ThingySticks/EnvironmentMonitor/Arduino/V1/Images/PcbBottom.png

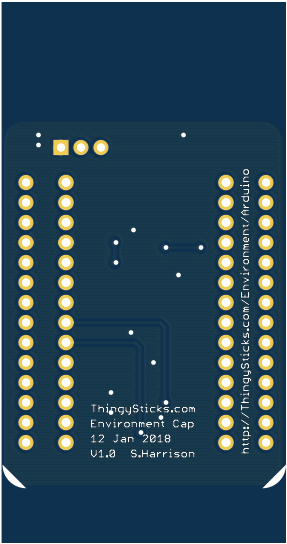
Arduino/V1/Images/PcbBottom.png
