ThingySticks/EnvironmentMonitor/Arduino/V1/Images/PcbTop.png

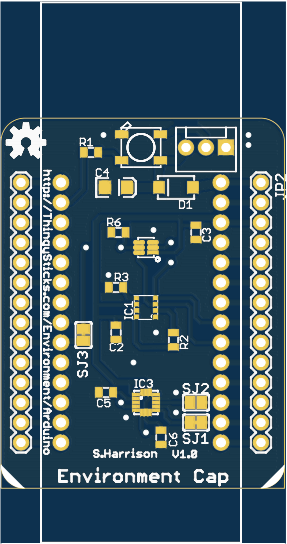
Arduino/V1/Images/PcbTop.png
