ThingySticks/EnvironmentMonitor/ArduinoNano33/V10/BottomBasic/Images/V10/PcbBottomSilkAndValues.png

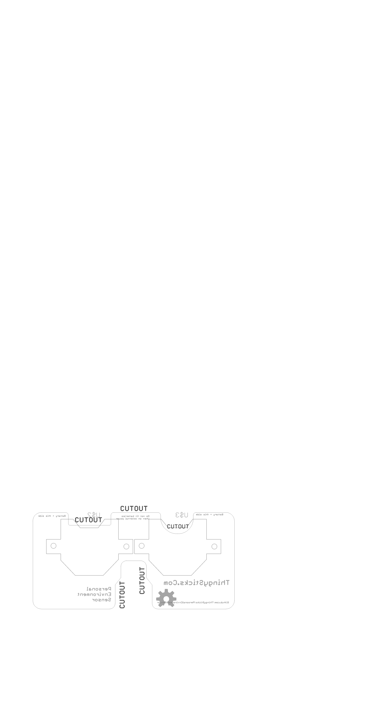
ArduinoNano33/V10/BottomBasic/Images/V10/PcbBottomSilkAndValues.png
