ThingySticks/EnvironmentMonitor/ArduinoNano33/V10/BottomBasic/Images/V10/PcbTopDesign.png

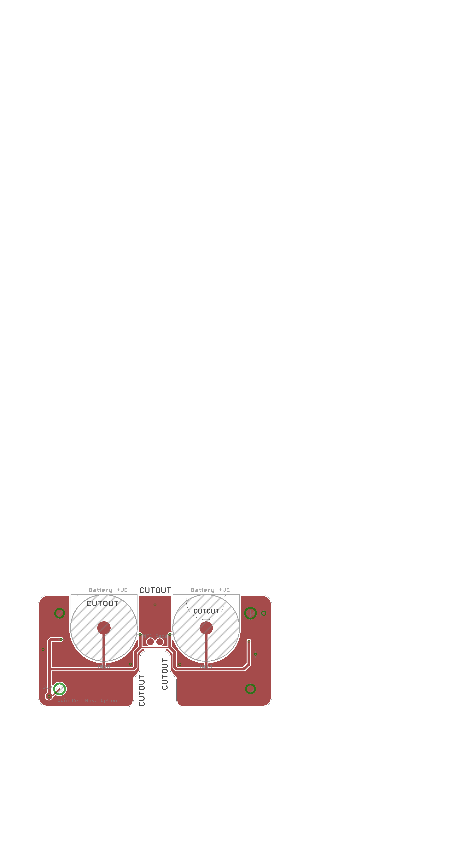
ArduinoNano33/V10/BottomBasic/Images/V10/PcbTopDesign.png
