ThingySticks/EnvironmentMonitor/ArduinoNano33/V10/BottomBasic/Images/V10/PcbTopSilkAndValues.png

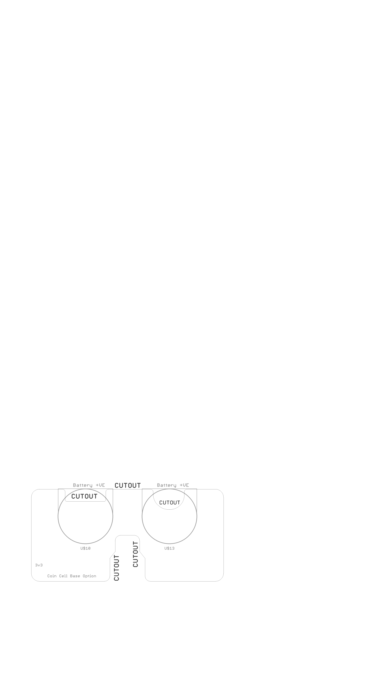
ArduinoNano33/V10/BottomBasic/Images/V10/PcbTopSilkAndValues.png
