ThingySticks/EnvironmentMonitor/ArduinoNano33/V10/BottomCustom/Images/PcbBottomDesign.png

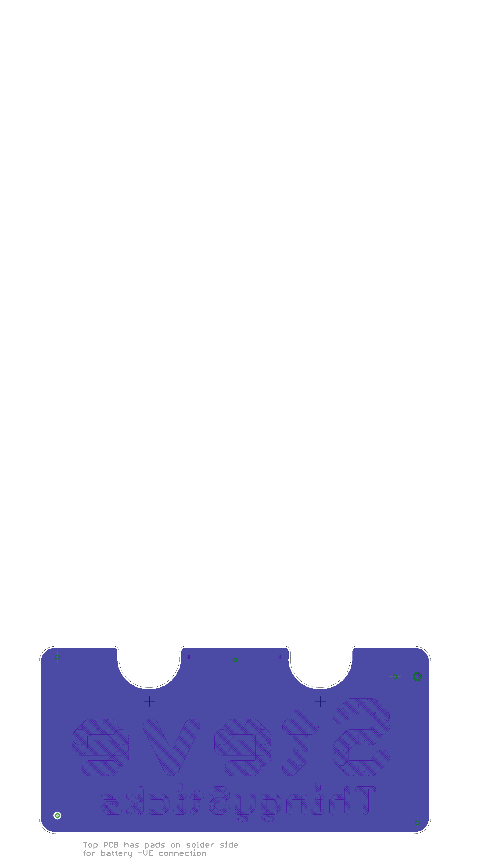
ArduinoNano33/V10/BottomCustom/Images/PcbBottomDesign.png
