ThingySticks/EnvironmentMonitor/ArduinoNano33/V10/BottomCustom/Images/PcbBottomSilkAndValues.png

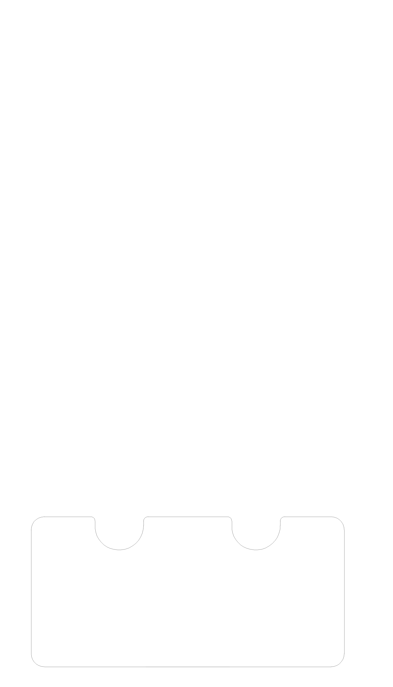
ArduinoNano33/V10/BottomCustom/Images/PcbBottomSilkAndValues.png
