ThingySticks/EnvironmentMonitor/ArduinoNano33/V10/BottomCustom/Images/PcbTopDesign.png

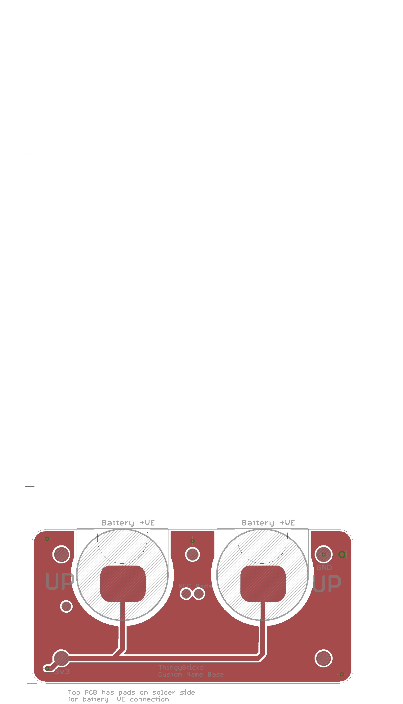
ArduinoNano33/V10/BottomCustom/Images/PcbTopDesign.png
