ThingySticks/EnvironmentMonitor/ArduinoNano33/V10/BottomCustom/Images/PcbTopSilkAndValues.png

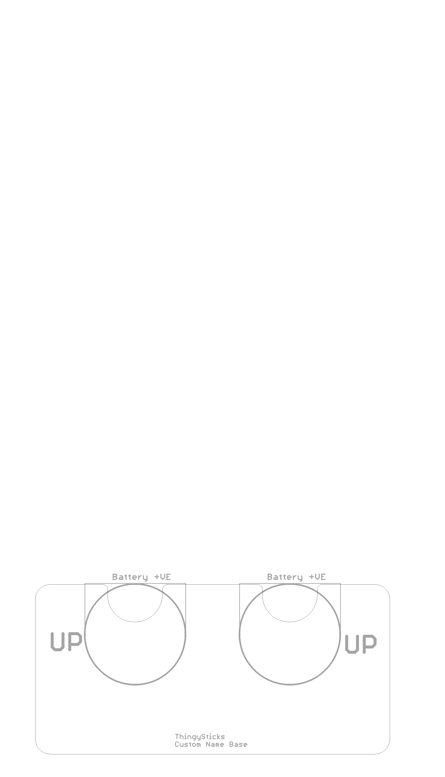
ArduinoNano33/V10/BottomCustom/Images/PcbTopSilkAndValues.png
