ThingySticks/EnvironmentMonitor/ArduinoNano33/V10/BottomCustom/Images/Schematic.png

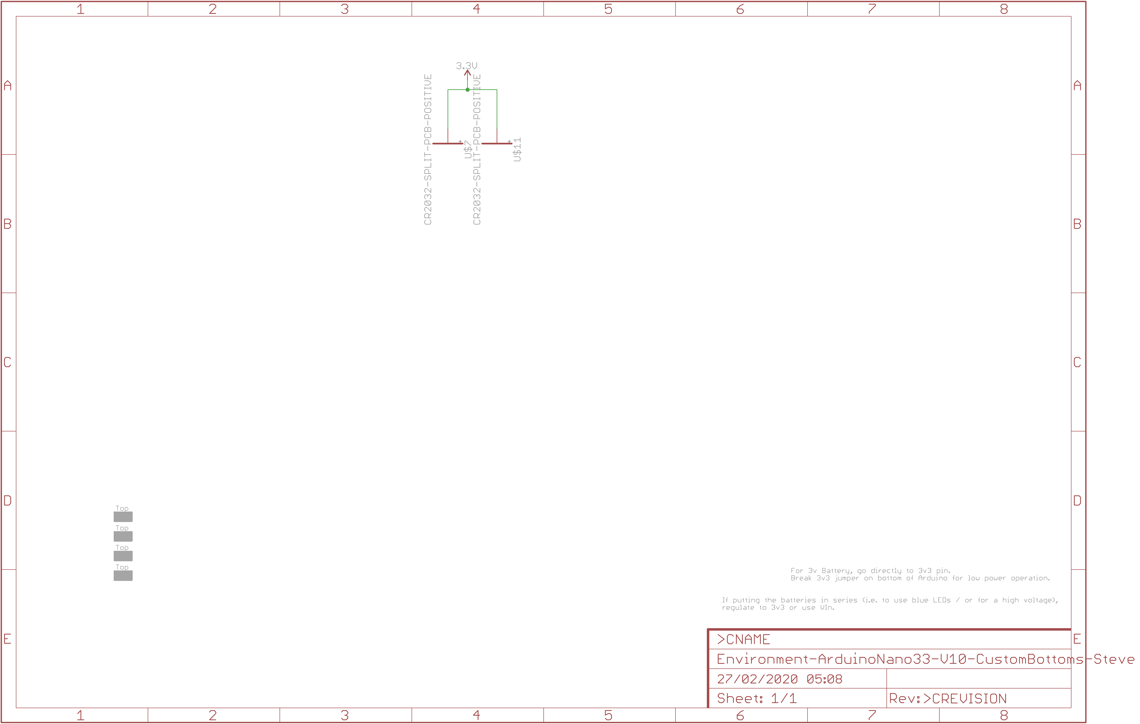
ArduinoNano33/V10/BottomCustom/Images/Schematic.png
