ThingySticks/EnvironmentMonitor/ArduinoNano33/V10/MiddleBasic/Images/V10.1/PcbAllLayersDesign.png

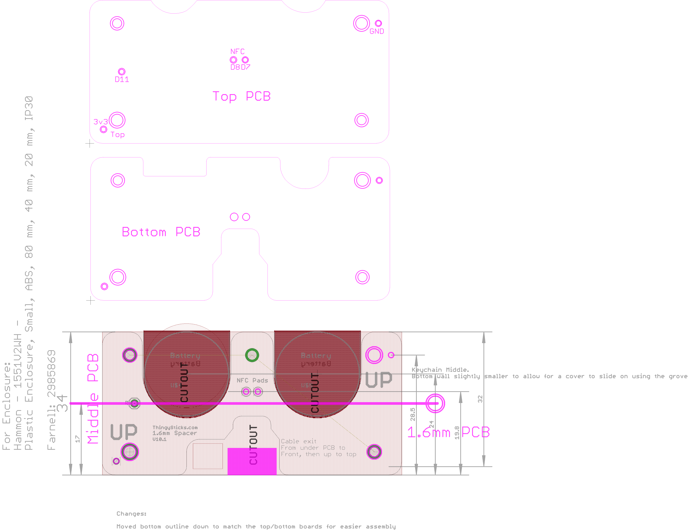
ArduinoNano33/V10/MiddleBasic/Images/V10.1/PcbAllLayersDesign.png
