ThingySticks/EnvironmentMonitor/ArduinoNano33/V10/MiddleBasic/Images/V10.1/PcbBottomDesign.png

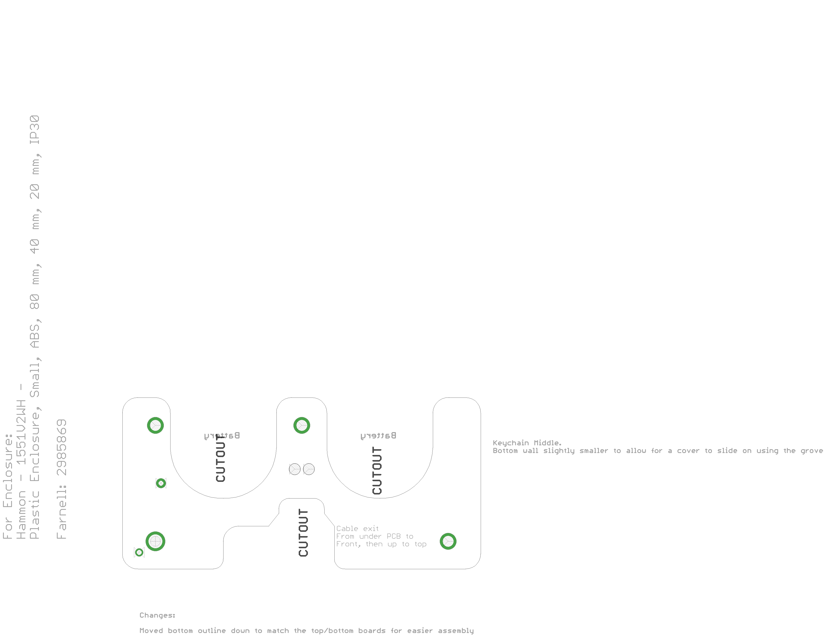
ArduinoNano33/V10/MiddleBasic/Images/V10.1/PcbBottomDesign.png
