ThingySticks/EnvironmentMonitor/ArduinoNano33/V10/MiddleBasic/Images/V10.1/PcbTopDesign.png

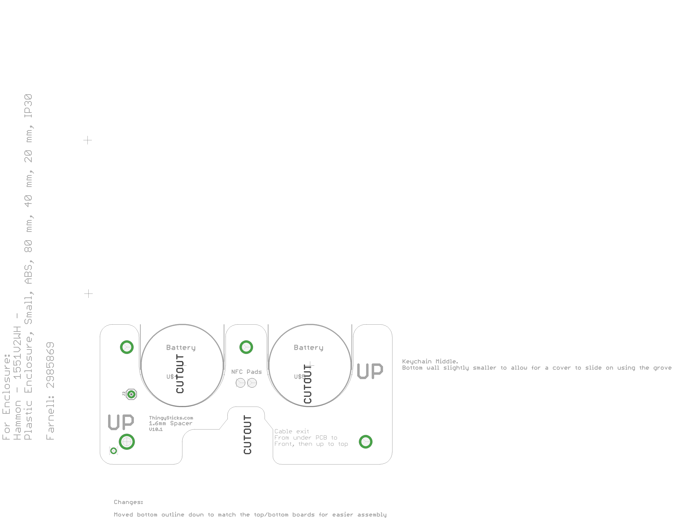
ArduinoNano33/V10/MiddleBasic/Images/V10.1/PcbTopDesign.png
