ThingySticks/EnvironmentMonitor/ArduinoNano33/V10/MiddleWithRing/Images/V10.1/Schematic.png

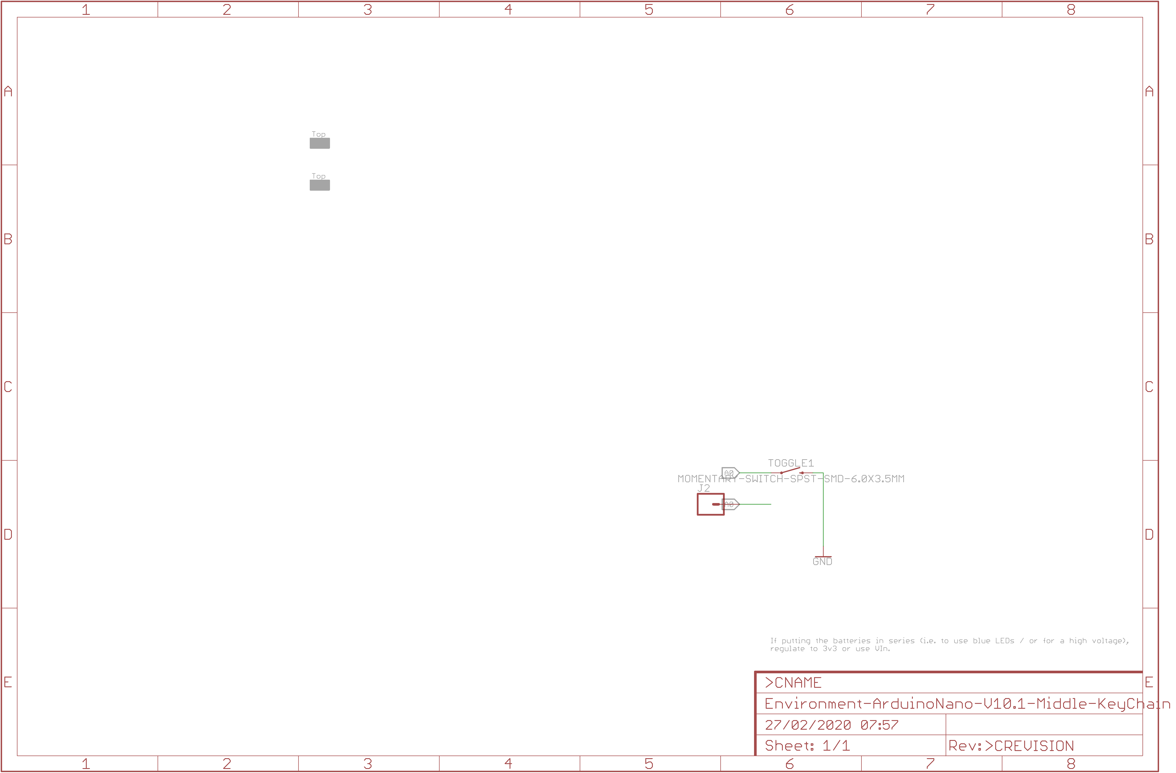
ArduinoNano33/V10/MiddleWithRing/Images/V10.1/Schematic.png
