ThingySticks/EnvironmentMonitor/ArduinoNano33/V10/StencilHolder/Images/PcbAllLayersDesign.png

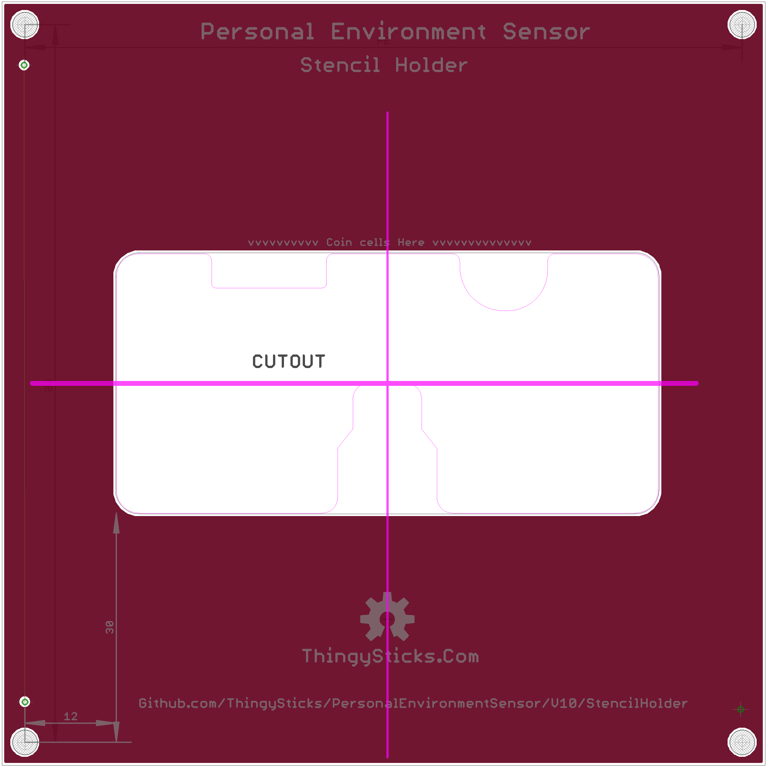
ArduinoNano33/V10/StencilHolder/Images/PcbAllLayersDesign.png
