ThingySticks/EnvironmentMonitor/ArduinoNano33/V10/StencilHolder/Images/PcbBottomDesign.png

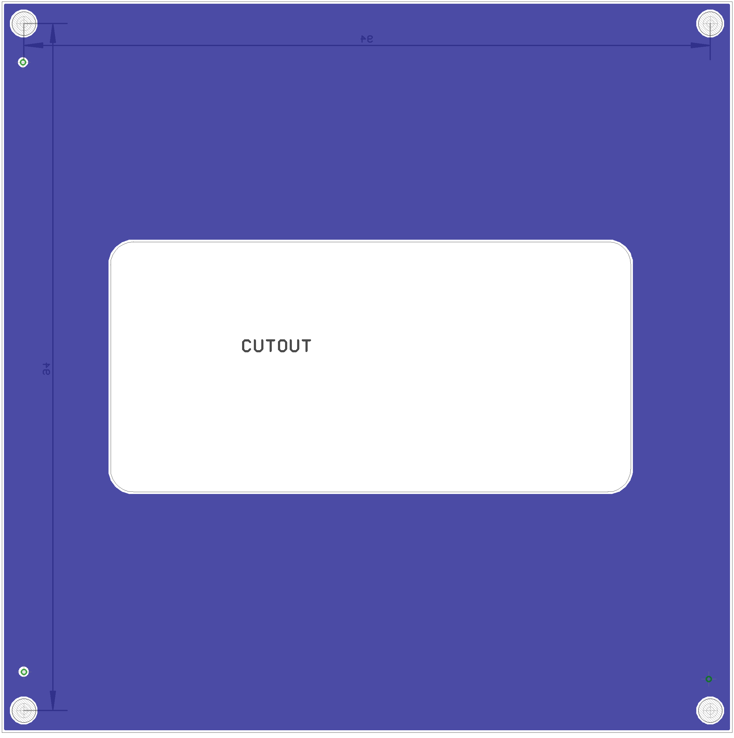
ArduinoNano33/V10/StencilHolder/Images/PcbBottomDesign.png
