ThingySticks/EnvironmentMonitor/ArduinoNano33/V10/StencilHolder/Images/PcbBottomSilkAndValues.png

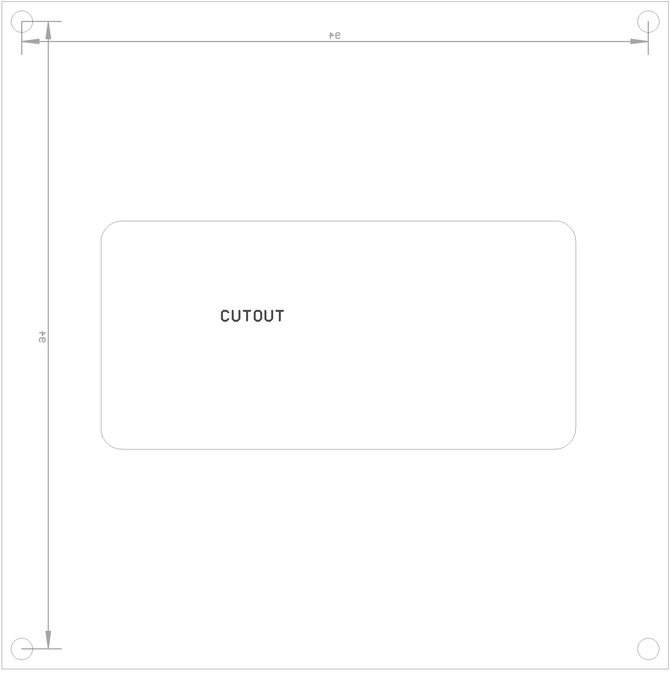
ArduinoNano33/V10/StencilHolder/Images/PcbBottomSilkAndValues.png
