ThingySticks/EnvironmentMonitor/ArduinoNano33/V10/StencilHolder/Images/PcbStencilHolderSilkAndValues.png

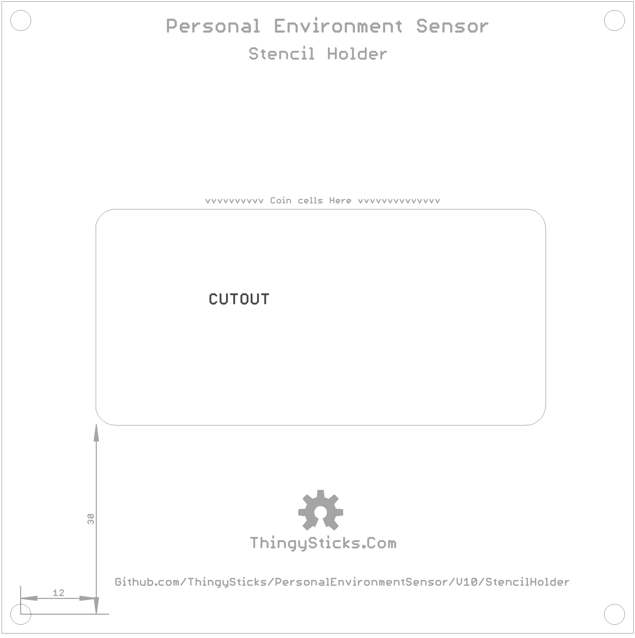
ArduinoNano33/V10/StencilHolder/Images/PcbStencilHolderSilkAndValues.png
