ThingySticks/EnvironmentMonitor/ArduinoNano33/V10/Top/Images/Environment-ArduinoNano33-V10.1-Top.png

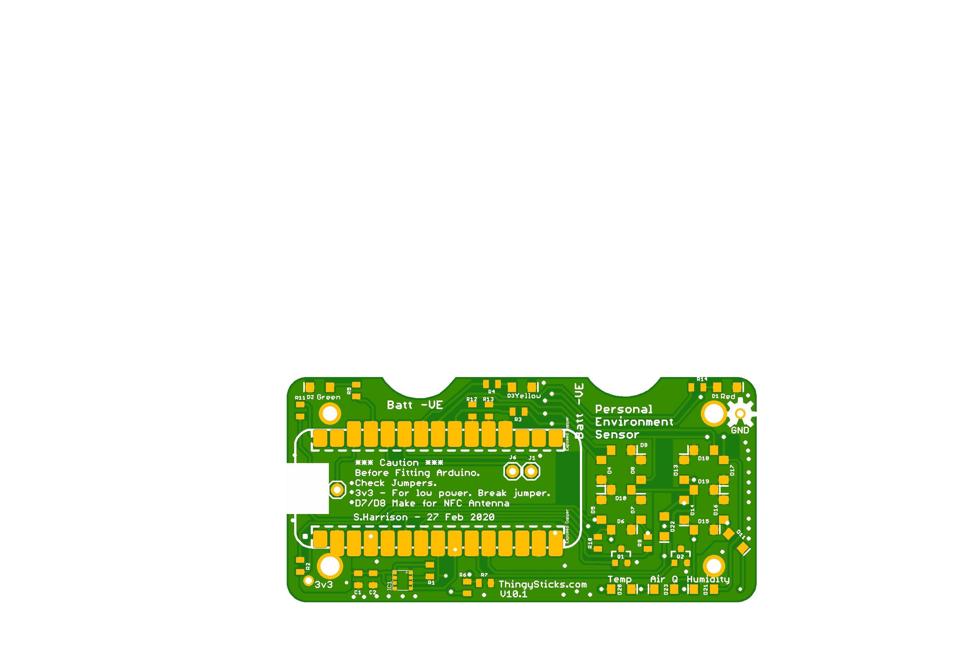
ArduinoNano33/V10/Top/Images/Environment-ArduinoNano33-V10.1-Top.png
