ThingySticks/EnvironmentMonitor/ArduinoNano33/V10/Top/Images/V10.1/PcbBottomDesign.png

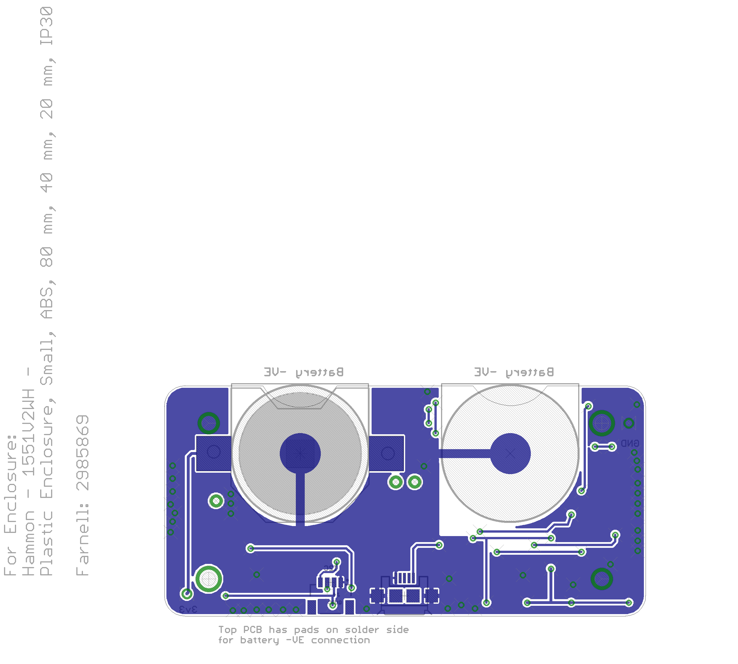
ArduinoNano33/V10/Top/Images/V10.1/PcbBottomDesign.png
