ThingySticks/EnvironmentMonitor/ArduinoNano33/V10/Top/Images/V10.1/PcbTopDesign.png

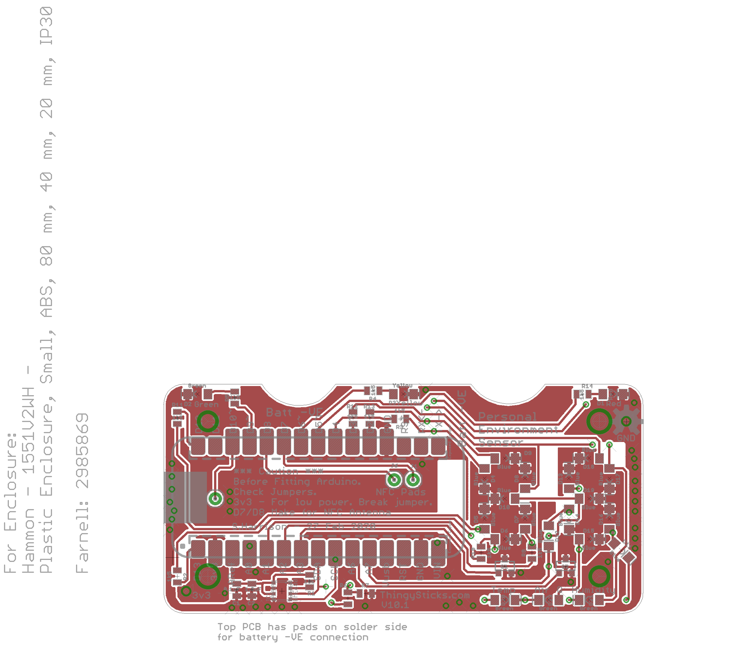
ArduinoNano33/V10/Top/Images/V10.1/PcbTopDesign.png
