ThingySticks/EnvironmentMonitor/Electron/V4/Images/PCB-All.png

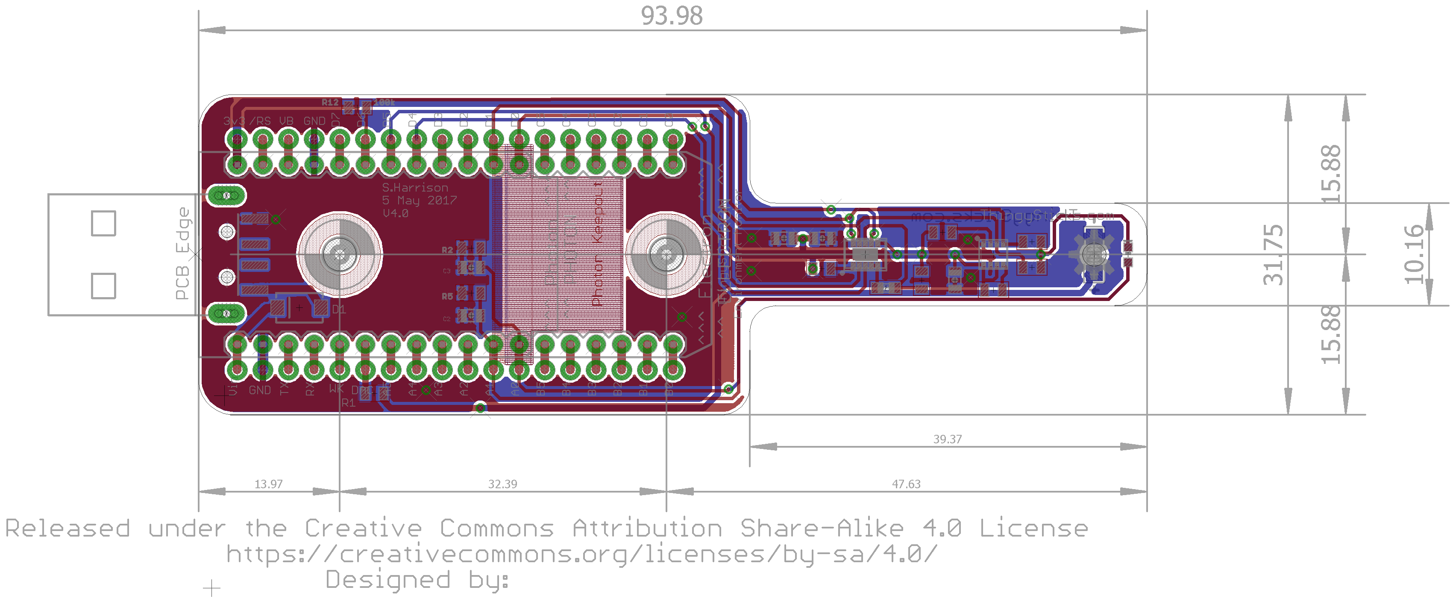
Electron/V4/Images/PCB-All.png
