ThingySticks/EnvironmentMonitor/Electron/V4/Images/PCB-Bottom.png

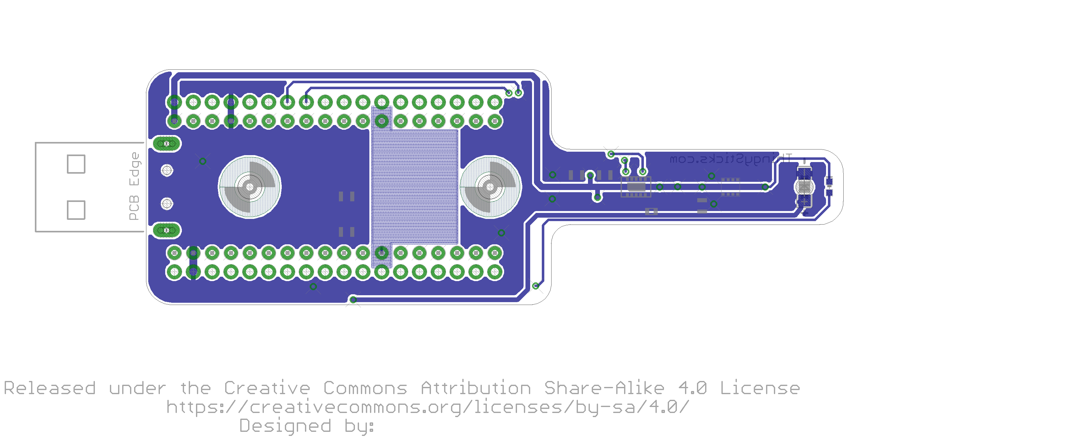
Electron/V4/Images/PCB-Bottom.png
