ThingySticks/EnvironmentMonitor/Electron/V4/Images/PCB-Top.png

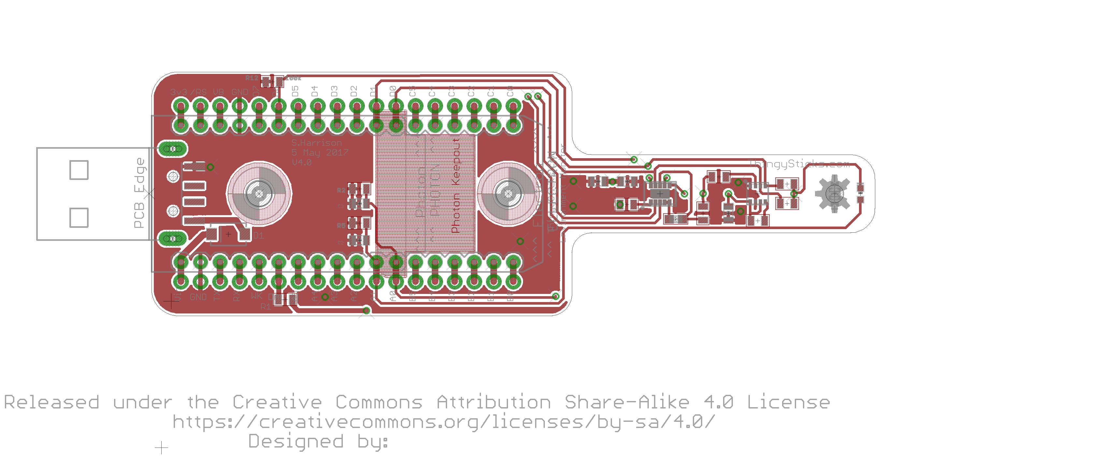
Electron/V4/Images/PCB-Top.png
