ThingySticks/EnvironmentMonitor/Electron/V4/Images/PcbBottom-1.png

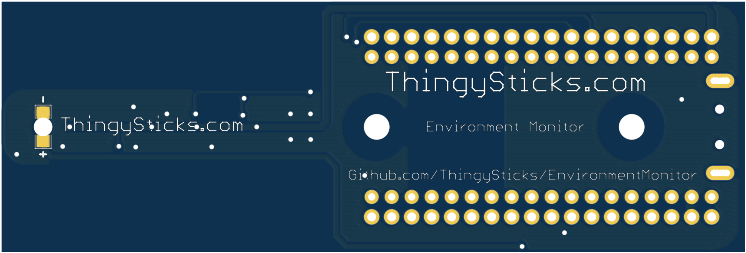
Electron/V4/Images/PcbBottom-1.png
