ThingySticks/EnvironmentMonitor/Electron/V4/Images/PcbTop-1.png

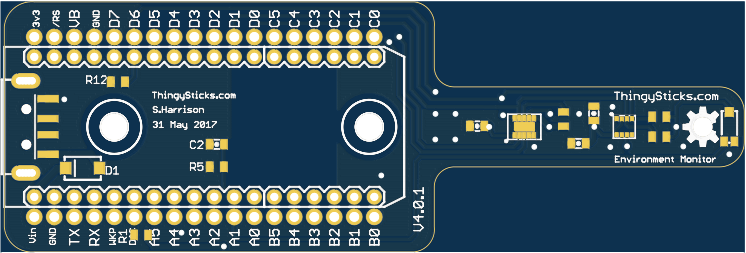
Electron/V4/Images/PcbTop-1.png
