ThingySticks/EnvironmentMonitor/Feather/V6/Images/2019-02-07/CO2.png

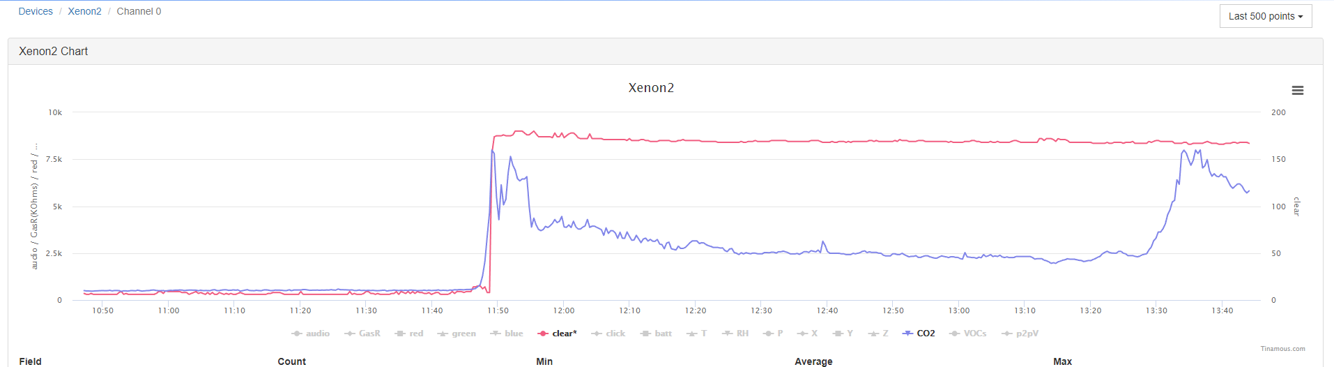
Feather/V6/Images/2019-02-07/CO2.png
