ThingySticks/EnvironmentMonitor/Feather/V6/Images/2019-02-07/Screenshot 2019-02-07 14.03.26.png

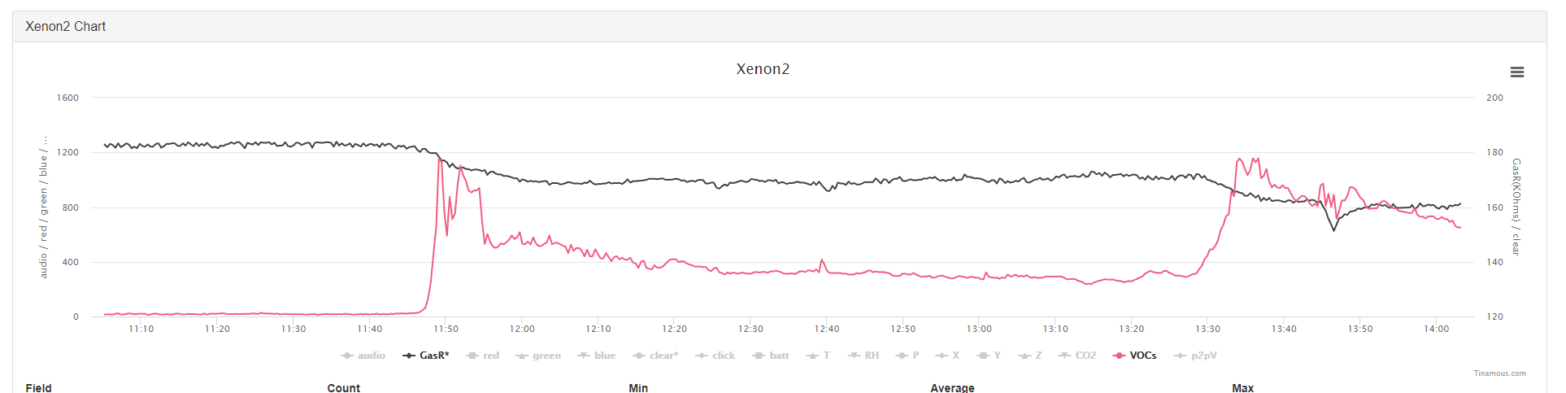
Feather/V6/Images/2019-02-07/Screenshot 2019-02-07 14.03.26.png
