ThingySticks/EnvironmentMonitor/Feather/V6/Images/2019-08-13/2019-08-13 20.44.30.jpg

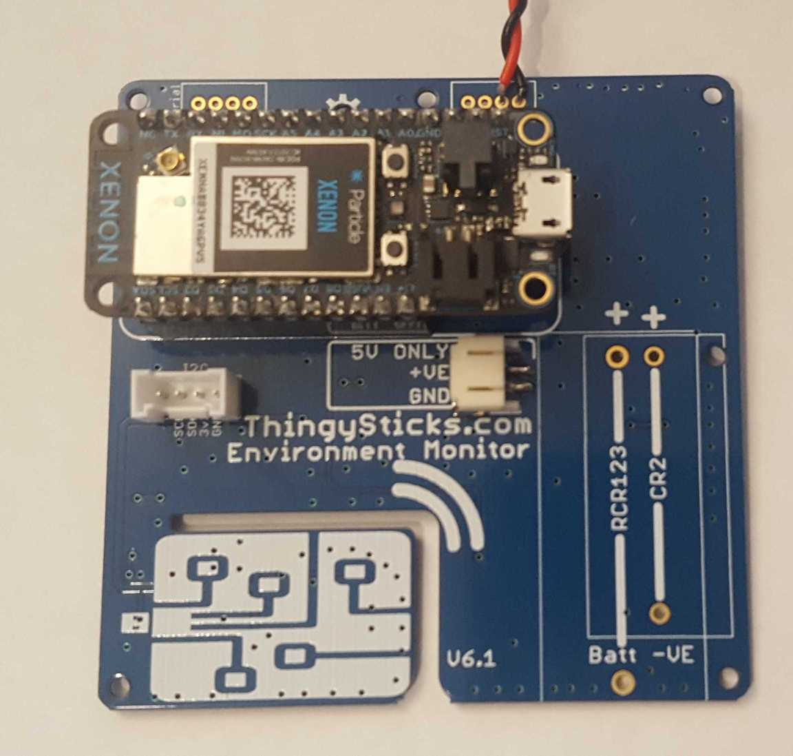
Feather/V6/Images/2019-08-13/2019-08-13 20.44.30.jpg
