ThingySticks/EnvironmentMonitor/Feather/V6/Images/2019-08-13/Enclosure2.jpg

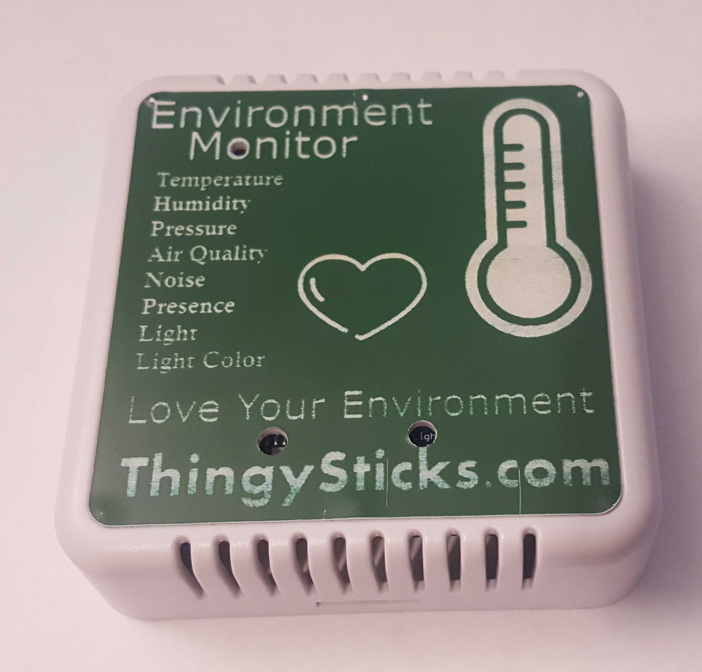
Feather/V6/Images/2019-08-13/Enclosure2.jpg
