ThingySticks/EnvironmentMonitor/Feather/V6/Images/2019-08-13/Enclosure.jpg

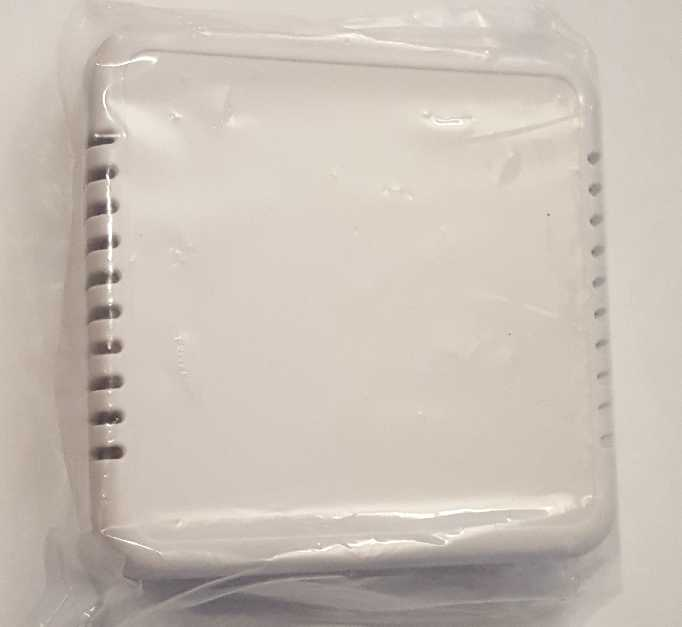
Feather/V6/Images/2019-08-13/Enclosure.jpg
