ThingySticks/EnvironmentMonitor/Feather/V6/Images/bottom.png

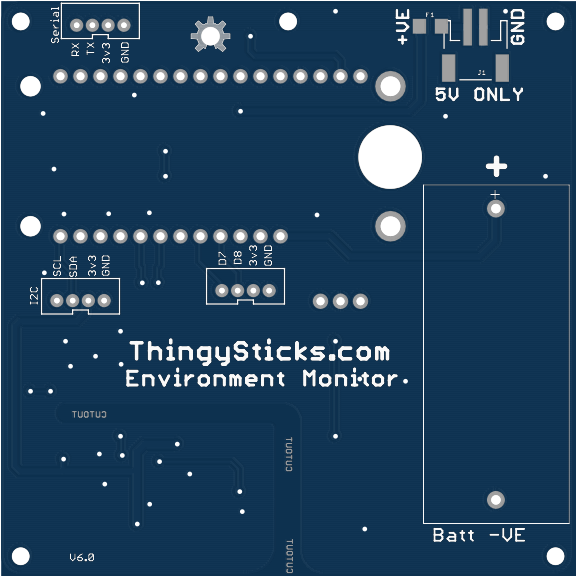
Feather/V6/Images/bottom.png
