ThingySticks/EnvironmentMonitor/Feather/V6/Images/bottom_copper.png

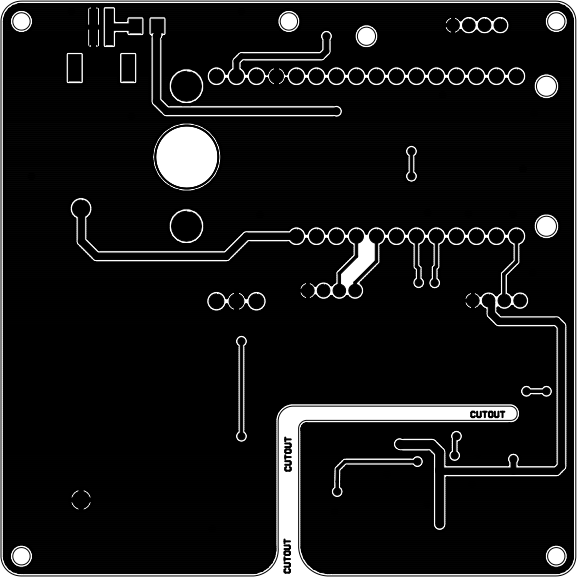
Feather/V6/Images/bottom_copper.png
