ThingySticks/EnvironmentMonitor/Feather/V6/Images/bottom_silkscreen.png

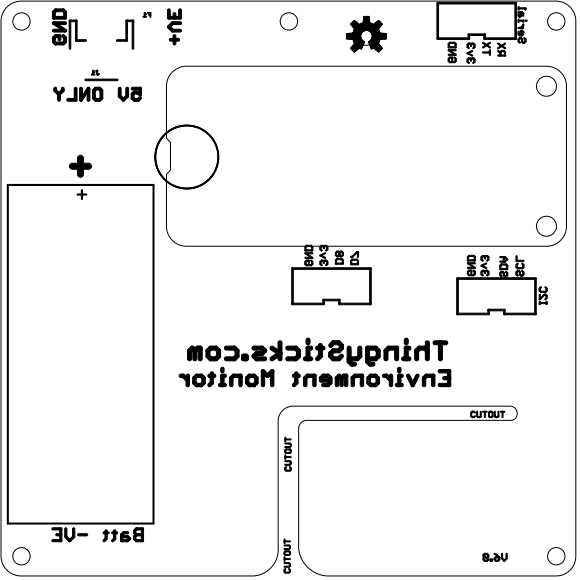
Feather/V6/Images/bottom_silkscreen.png
