ThingySticks/EnvironmentMonitor/Feather/V6/Images/mill.png

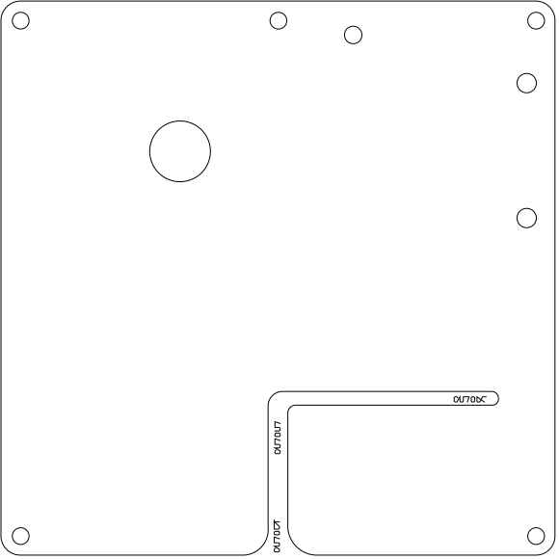
Feather/V6/Images/mill.png
