ThingySticks/EnvironmentMonitor/Feather/V6/Images/PcbAll.png

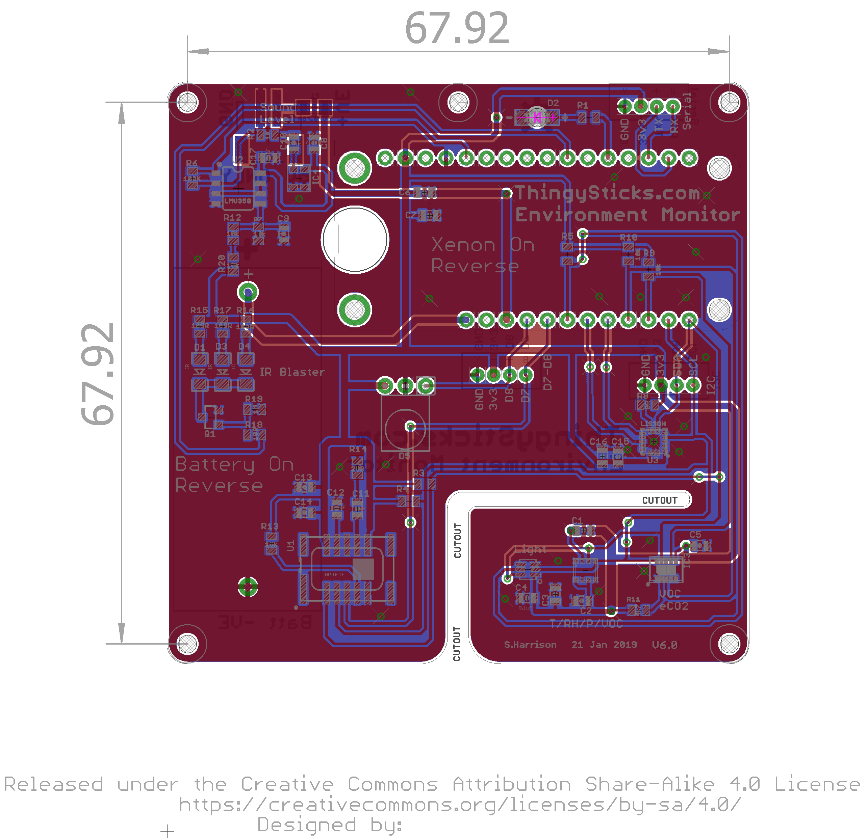
Feather/V6/Images/PcbAll.png
