ThingySticks/EnvironmentMonitor/Feather/V6/Images/PcbAllLayersDesign.png

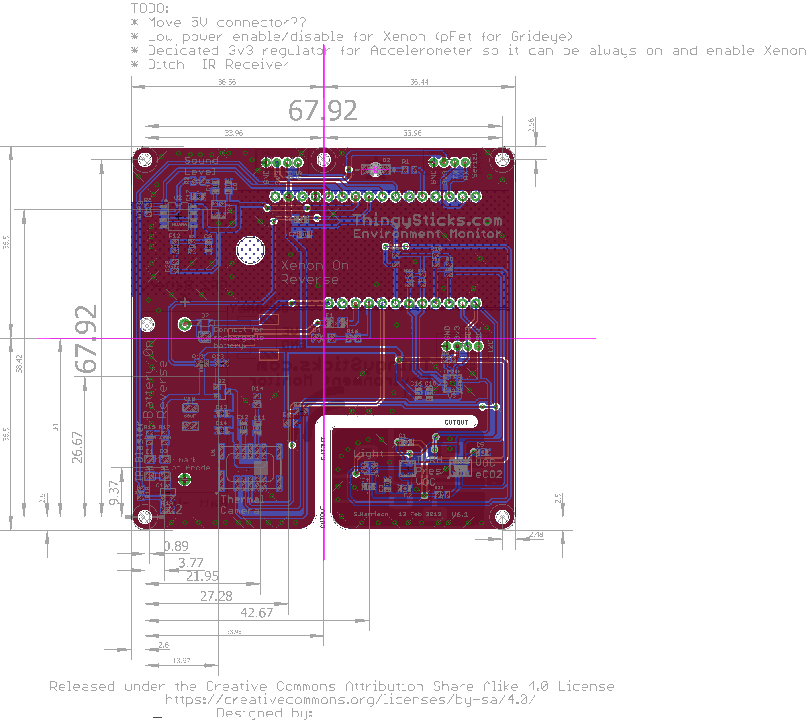
Feather/V6/Images/PcbAllLayersDesign.png
