ThingySticks/EnvironmentMonitor/Feather/V6/Images/PcbBottomDesign.png

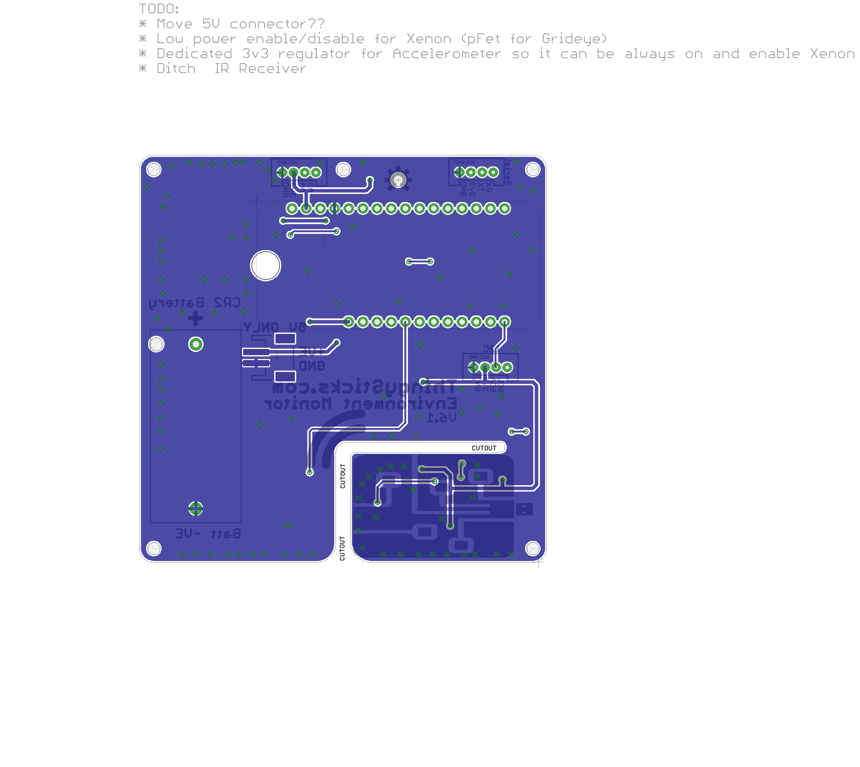
Feather/V6/Images/PcbBottomDesign.png
