ThingySticks/EnvironmentMonitor/Feather/V6/Images/Schematic.png

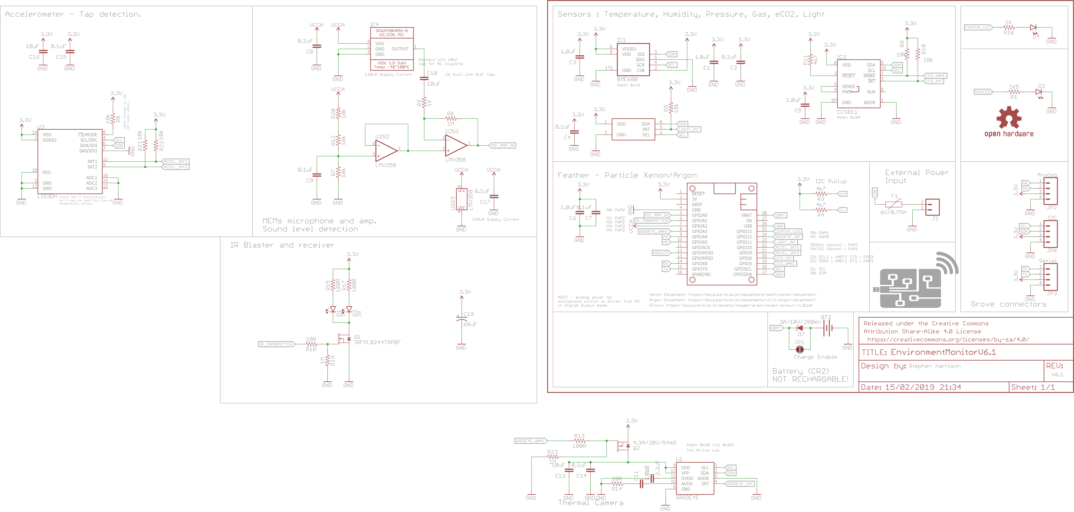
Feather/V6/Images/Schematic.png
