ThingySticks/EnvironmentMonitor/Feather/V6/Images/top.png

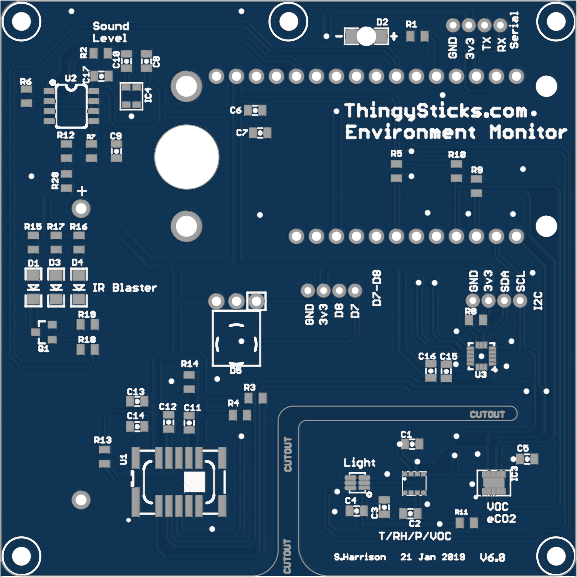
Feather/V6/Images/top.png
