ThingySticks/EnvironmentMonitor/Feather/V6/Images/top_copper.png

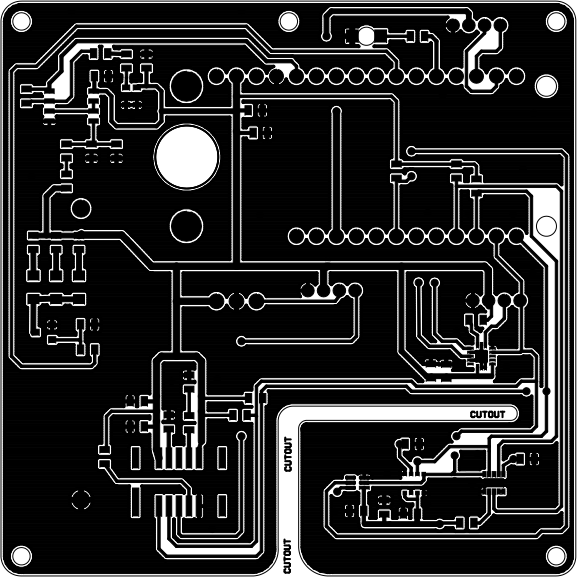
Feather/V6/Images/top_copper.png
