ThingySticks/EnvironmentMonitor/Feather/V6/Images/top_silkscreen.png

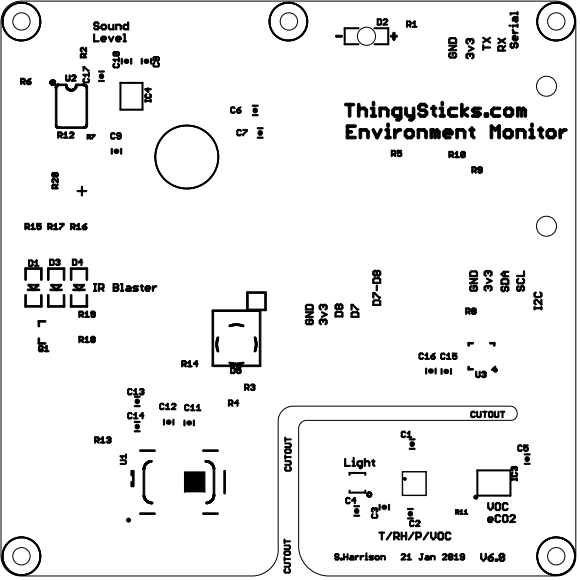
Feather/V6/Images/top_silkscreen.png
