ThingySticks/EnvironmentMonitor/Photon/V4.1/Images/PCB-All.png

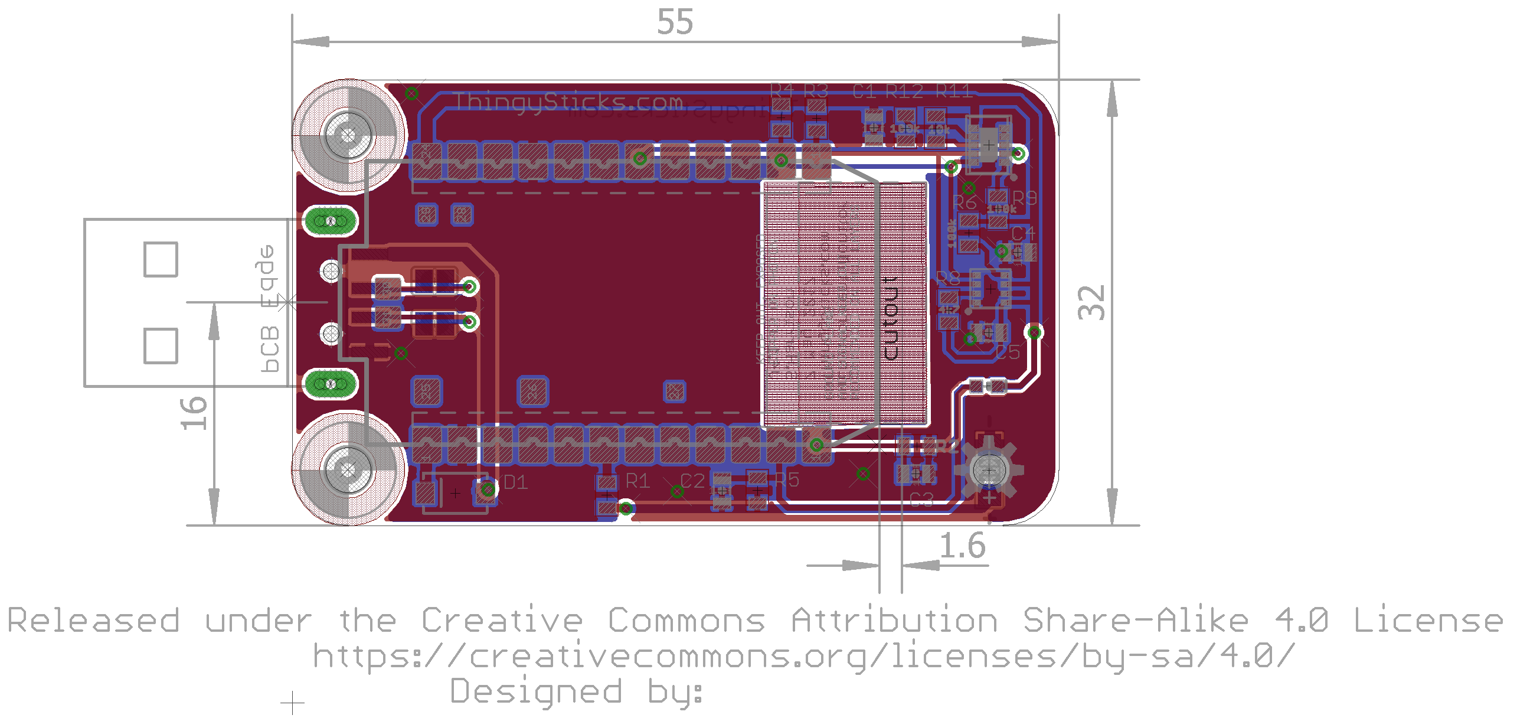
Photon/V4.1/Images/PCB-All.png
