ThingySticks/EnvironmentMonitor/Photon/V4.1/Images/Schematic.png

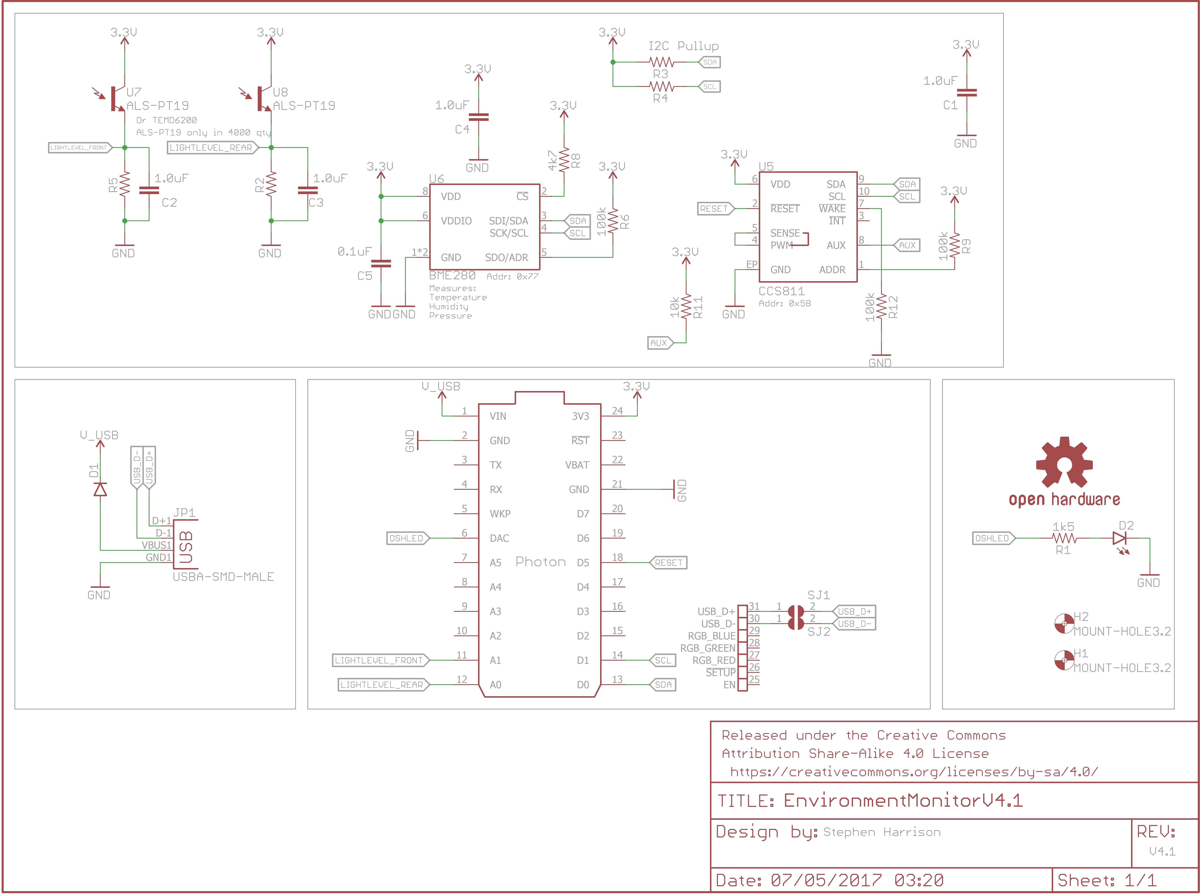
Photon/V4.1/Images/Schematic.png
