ThingySticks/EnvironmentMonitor/Electron/V2/PCB/Environment-V21-PcbAll.pdf

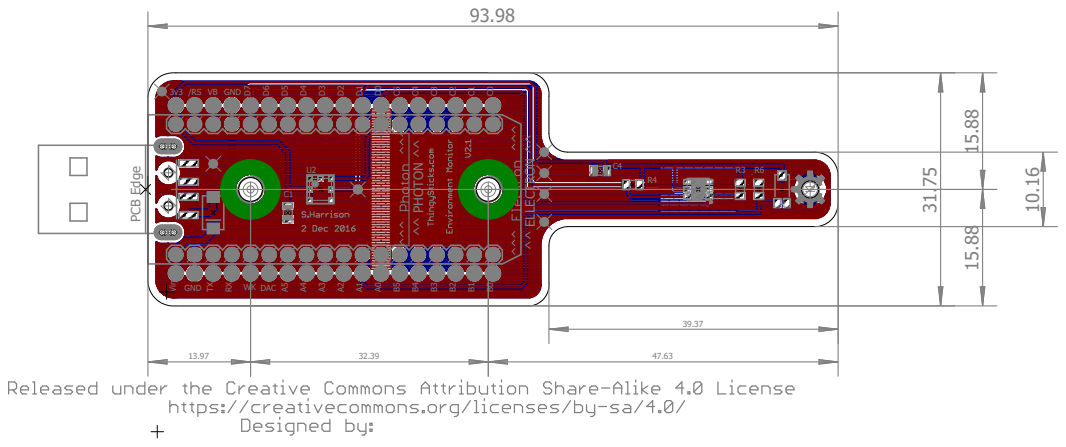
[picture p71: page 1]

D21R Photon Keepout PCB Edge 3v3 /RS VB GND D7 VinGND TXRXWK DAC A5A4A3A2A1A0B5B4B3B2B1B0 D6D5D4D3D2D1D0C5C4C3C2C1C0 U2 C1 D1 ^^ PHOTON ^^ ^^ ELLECTRON ^^ R3 R4 C4 R6 31.75 15.88 93.98 13.97 32.39 47.63 10.16 15.88 39.37
