ThingySticks/EnvironmentMonitor/Electron/V2/PCB/EnvironmentMonitorV2-PCB-All.pdf

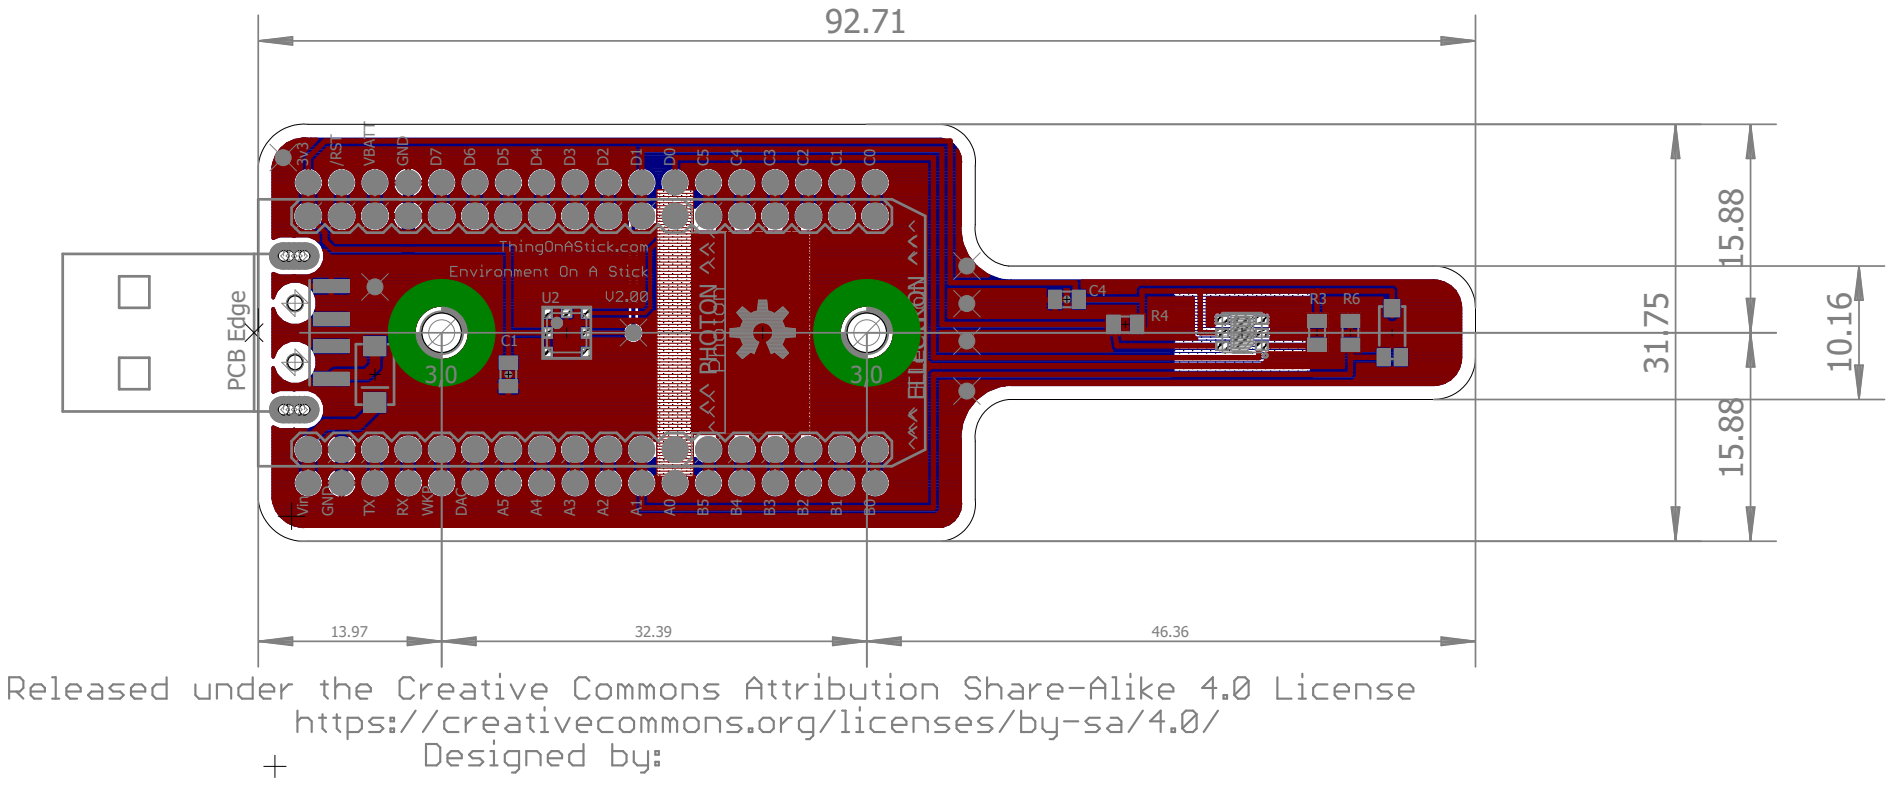
[picture p72: page 1]

Photon Keepout PCB Edge 3v3 /RST VBAT GND D7 Vin GND TXRXWKP DAC A5A4A3A2A1A0B5B4B3B2B1B0 D6D5D4D3D2D1D0C5C4C3C2C1C0 U2 C1 D1 ^^ PHOTON ^^ ^^ ELLECTRON ^^ R3 R4 C4 R6 31.75 15.88 92.71 13.97 32.39 46.36 10.16 15.88 3,0 3,0
