ThingySticks/EnvironmentMonitor/Electron/V1/PCB/EnvironmentOnAStick-All.pdf

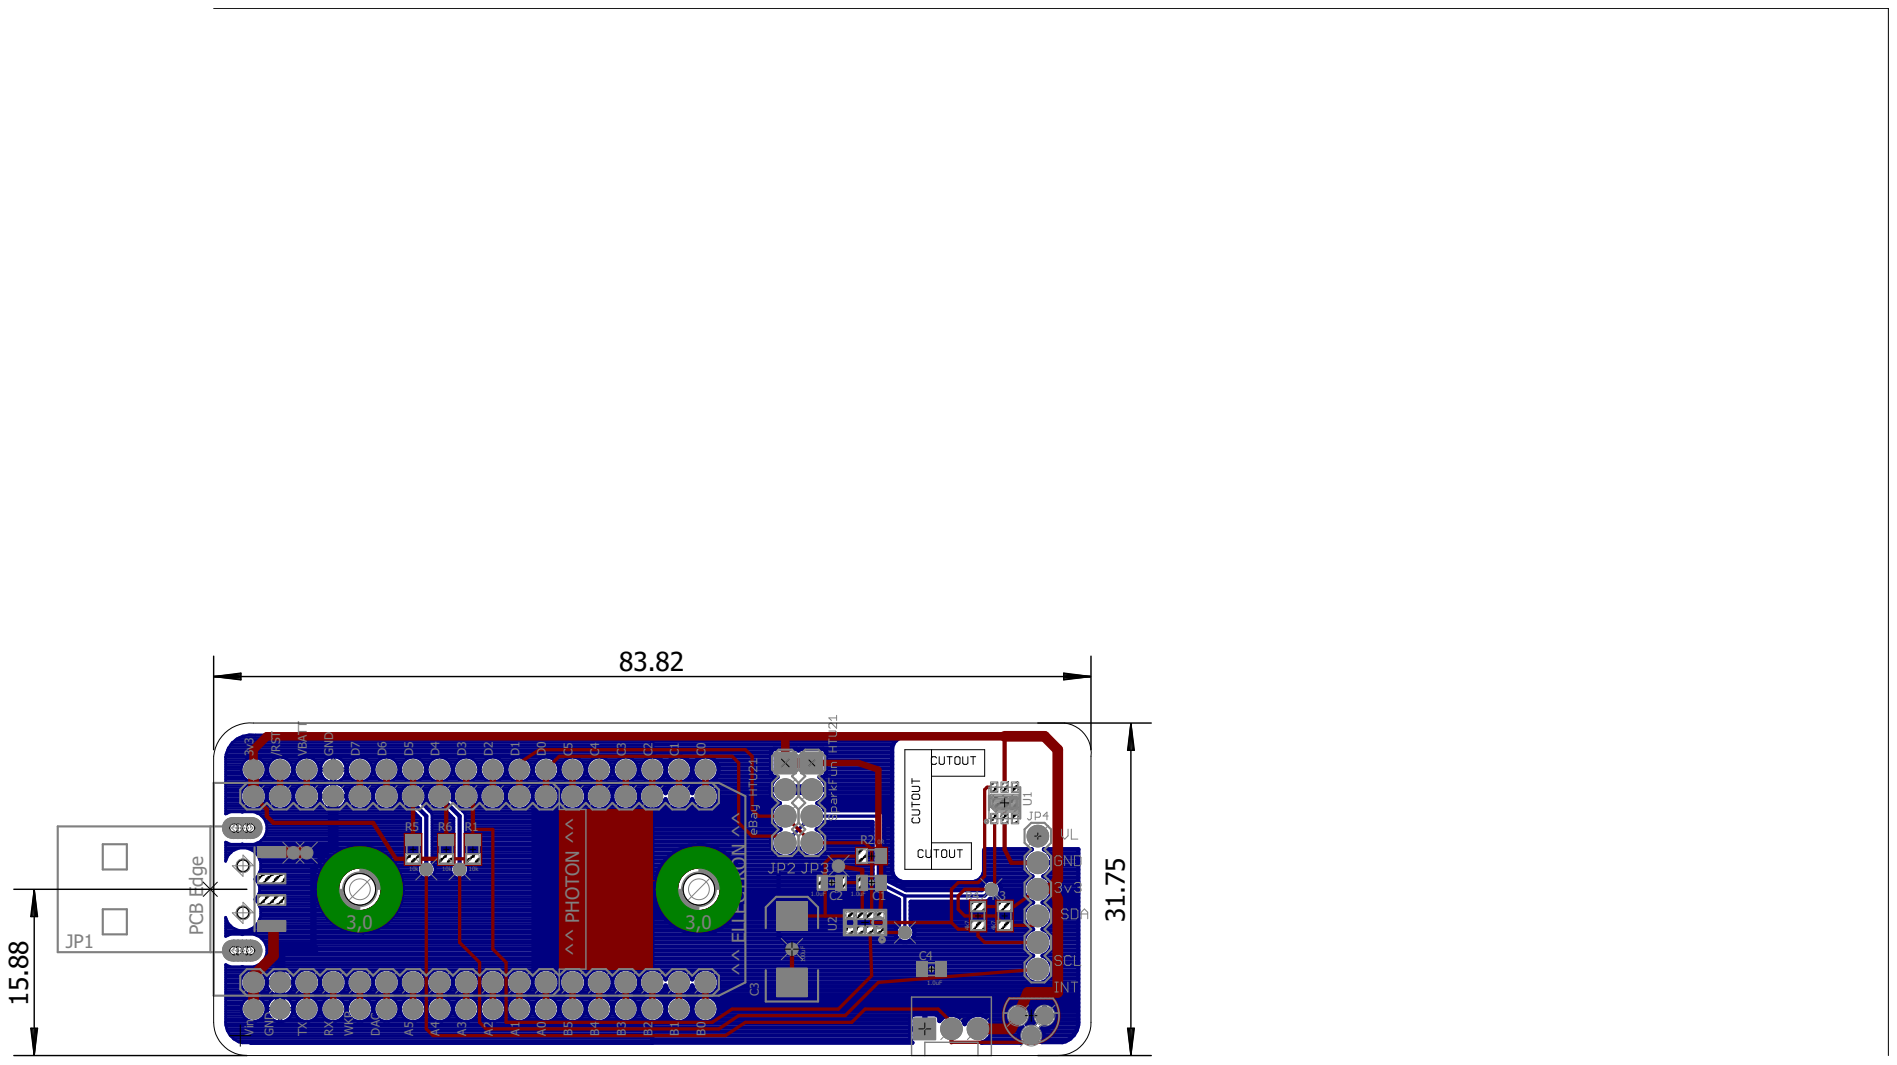
[picture p73: page 1]

Photon Keepout PCB Edge 3v3 /RST VBAT GND D7 Vin GND TXRXWKP DAC A5A4A3A2A1A0B5B4B3B2B1B0 D6D5D4D3D2D1D0C5C4C3C2C1C0 JP1 U1 U2 R1 C2 C1 C3 R2 R4 R3 R5 C4 R6 ^^ PHOTON ^^ ^^ ELLECTRON ^^ 10k 1.0uF 1.0uF 100uF 0R 4k7 4k7 10k 1.0uF 10k 31.75 15.88 83.82 3,0 3,0
