ThingySticks/EnvironmentMonitor/Electron/V1/PCB/EnvironmentOnAStick-pcb-all.pdf

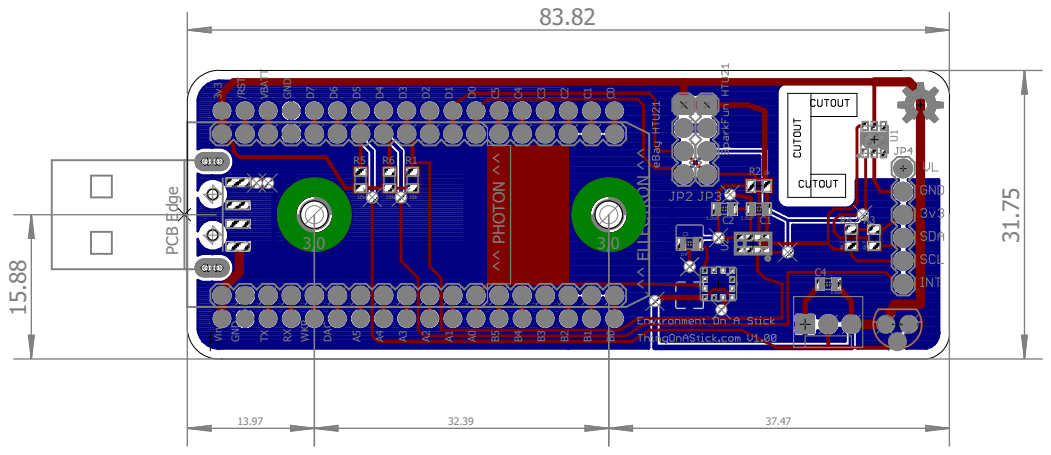
[picture p74: page 1]

100uF 3C Photon Keepout PCB Edge 3v3 /RST VBATT GND D7 Vin GND TXRXWKP DAC A5A4A3A2A1A0B5B4B3B2B1B0 D6D5D4D3D2D1D0C5C4C3C2C1C0 U1 U2 R1 C2 C1 R2 R4 R3 R5 C4 R6 C5 ^^ PHOTON ^^ ^^ ELLECTRON ^^ 10k 1.0uF 1.0uF 0R 4k7 4k7 10k 1.0uF 10k 1nF 31.75 15.88 83.82 13.97 32.39 37.47 3,0 3,0
