ThingySticks/EnvironmentMonitor/Feather/V6/PCB/EnvironmentMonitorV6.1.brd

## EAGLE design Feather/V6/PCB/EnvironmentMonitorV6.1.brd (2020-01-12)

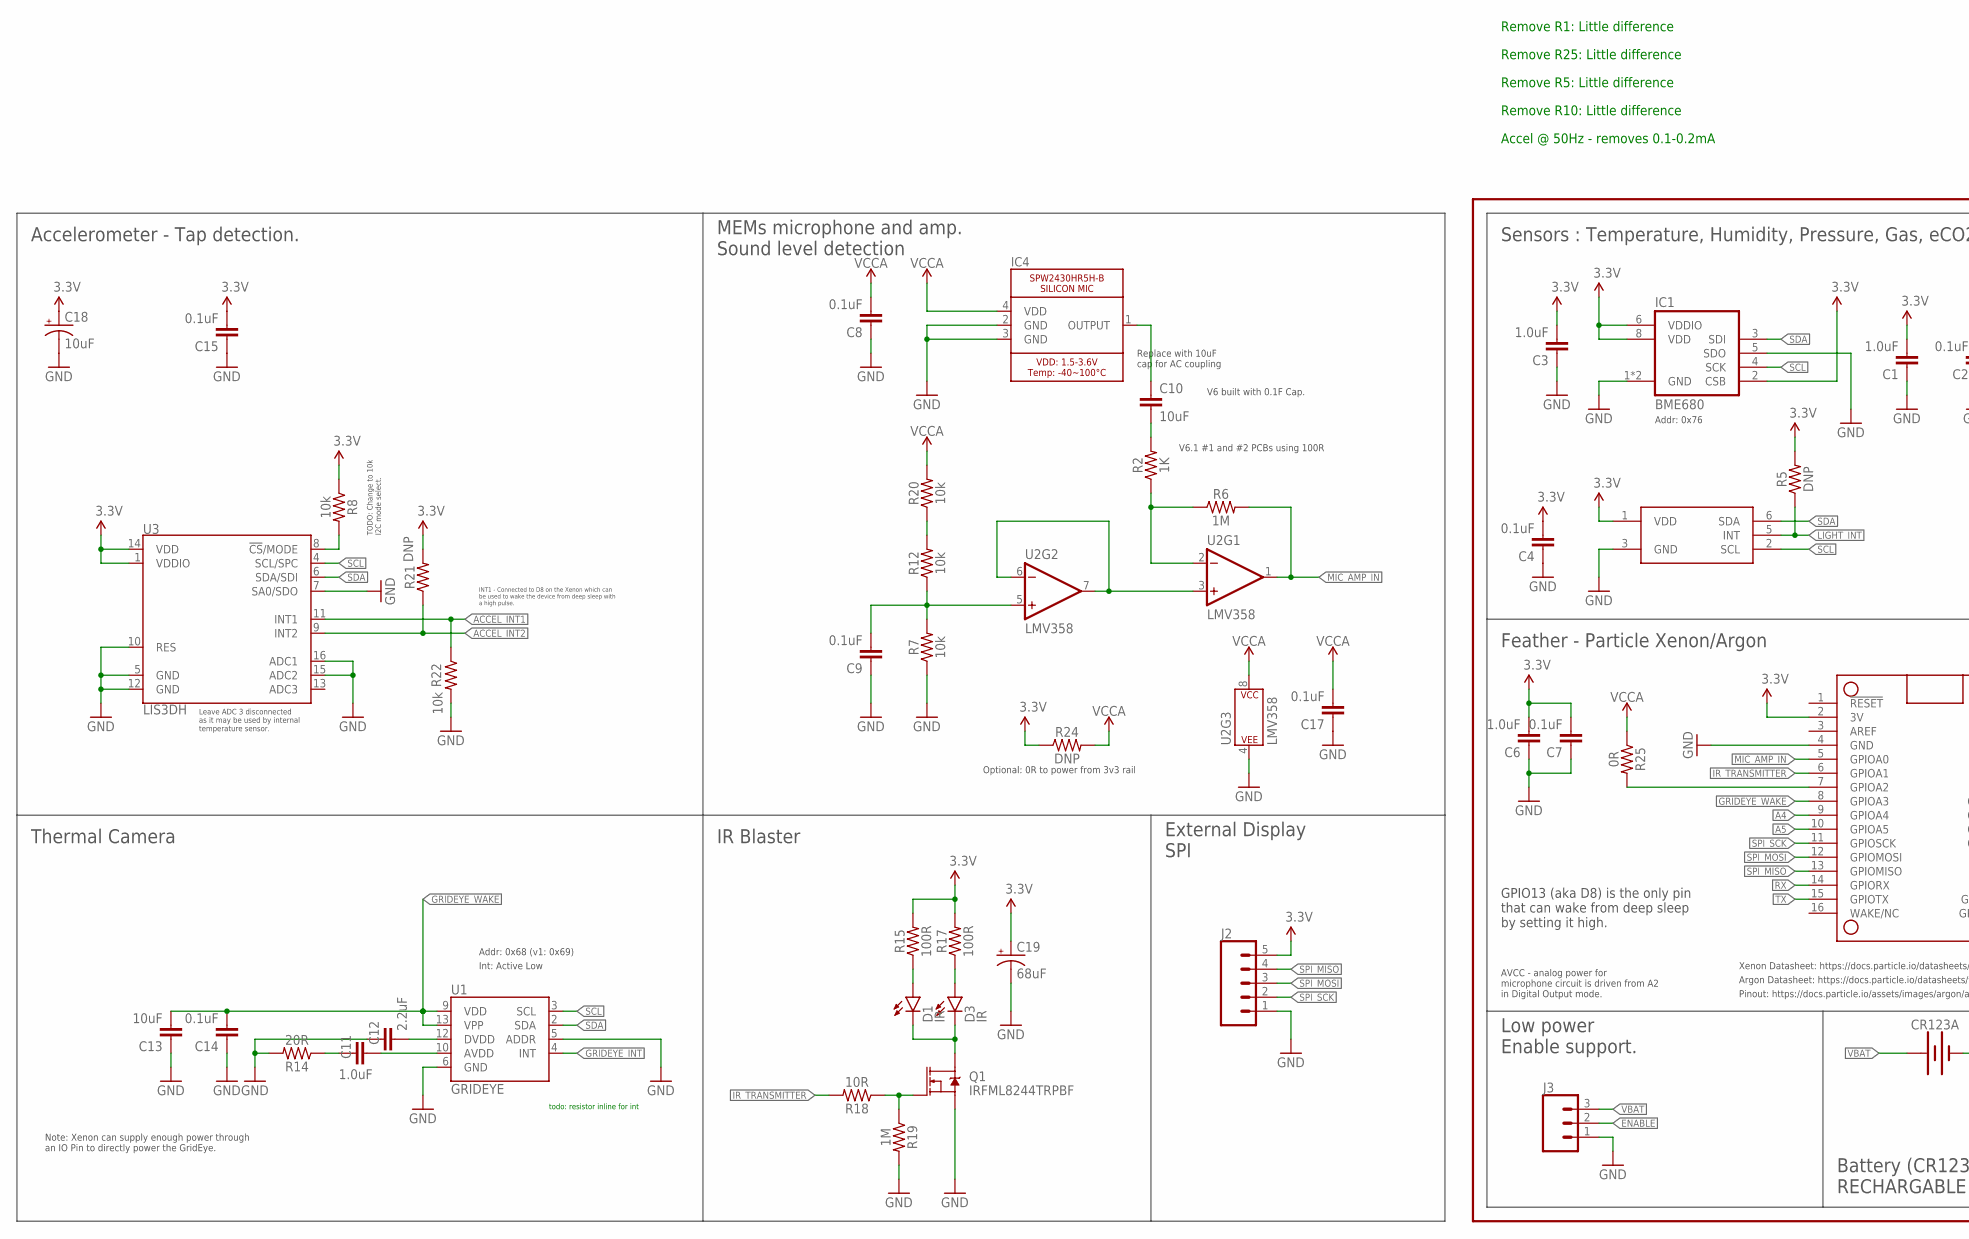
[picture p85: schematic EnvironmentMonitorV6.1.sch, sheet 1, part in row 1, column 1]

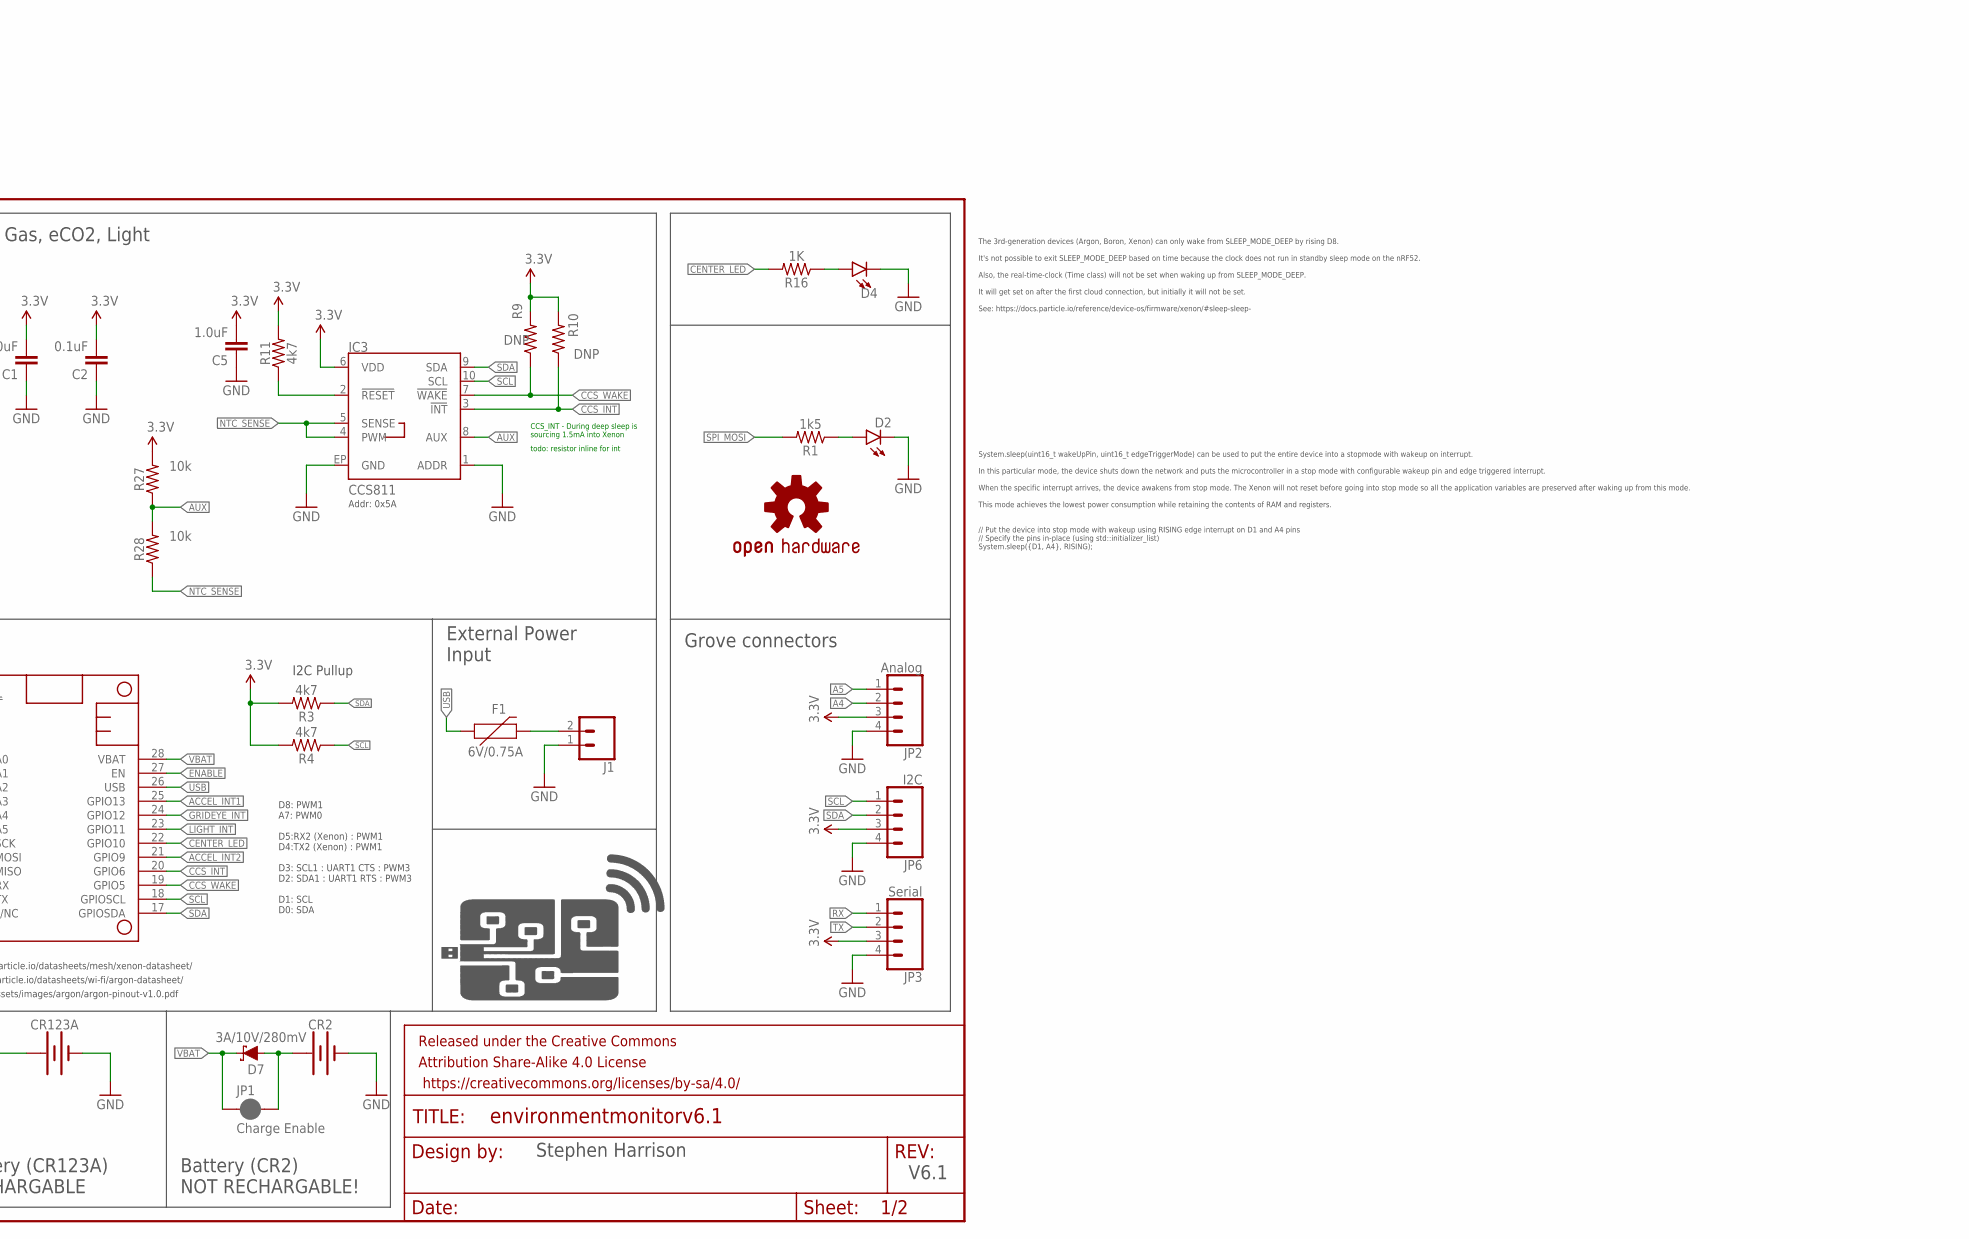
[picture p86: schematic EnvironmentMonitorV6.1.sch, sheet 1, part in row 1, column 2]

Parts:
C1, C3, C5, C6, C11: 1.0uF; 0805-CAP
C2, C4, C7, C8, C9, C14, C15, C17: 0.1uF; 0805-CAP
C10, C13: 10uF; 0805-CAP
C12: 2.2uF; 0805-CAP; FARNELL 2070473
C18: 10uF; EIA3216; FARNELL 1457413
C19: 68uF; EIA3528
CR2: BATTERYCR2-NO-HOLES; BATTERY_CR2-HOLDER-NO-HOLES
CR123A: BATTERY-16340; BATTERY_16340-HOLDER
D1, D3: IR; LED-1206; FARNELL 2313501
D2: LED1206-BOTTOM; LED-1206-BOTTOM
D4: LED1206; LED-1206
D7: 3A/10V/280mV; SOD-323
F1: 6V/0.75A; 1206; FARNELL 2786571
FRAME1: FRAME-LETTER; CREATIVE_COMMONS
IC1: BME680
IC2: TCS3472; FN-6
IC3: CCS811; LGA10
IC4: SPW2430HR5H-B
IC5: FEATHERWINGPADS_AND_PLACE_ONLY; FEATHERWIND_PADS_AND_PLACE
J1: CONN_02JST-2-PH-SIDE; JST-2-SMD
J2: CONN_05SMD2; 1X05_1MM_RA
J3: CONN_03SMD; 1X03-1MM-RA
JP1: Charge Enable; SMT-JUMPER_2_NC_PASTE_SILK
JP2: Analog; JST-4-PH-GROVE
JP3: Serial; JST-4-PH-GROVE
JP6: I2C; JST-4-PH-GROVE
LOGO1: OSHW-LOGOM; OSHW-LOGO-M
Q1: IRFML8244TRPBF; SOT23-3; FARNELL 1857298
R1: 1k5; 0805
R2, R16: 1K; 0805
R3, R4, R11: 4k7; 0805
R5, R9, R10, R21, R24: DNP; 0805
R6: 1M; 0805
R7, R8, R12, R20, R22, R27, R28: 10k; 0805
R14: 20R; 0805; FARNELL 2447604
R15, R17: 100R; 0805
R18: 10R; 0805
R19: 1M; 0805; FARNELL 2129354
R25: 0R; 0805
U1: GRIDEYE; GRIDEYE-AMG88
U2: LMV358; SO08
U3: LIS3DH; LGA-16-3X3
U$1: THINGYSTICKS_LOGOLOGO_2; THINGYSTICKS_LOGO_2

Connections:
3.3V: C1.2, C2.2, C3.2, C4.2, C5.2, C6.2, C7.2, C15.2, C18.+, C19.A (+), IC1.2 (CSB), IC1.6 (VDDIO), IC1.8 (VDD), IC2.1 (VDD), IC3.6 (VDD), IC5.2 (3V), J2.5, JP2.3, JP3.3, JP6.3, R3.2, R4.2, R5.2, R8.1, R9.2, R10.2, R11.2, R15.2, R17.2, R21.2, R24.1, R27.2, U3.1 (VDDIO), U3.14 (VDD)
A4: IC5.9 (GPIOA4), JP2.2
A5: IC5.10 (GPIOA5), JP2.1
ACCEL_INT1: IC5.25 (GPIO13), R22.1, U3.11 (INT1)
ACCEL_INT2: IC5.21 (GPIO9), R21.1, U3.9 (INT2)
AUX: IC3.8 (AUX), R27.1, R28.2
CCS8_RESET: IC3.2 (!RESET!), R11.1
CCS_INT: IC3.3 (!INT!), IC5.20 (GPIO6), R10.1
CCS_WAKE: IC3.7 (!WAKE!), IC5.19 (GPIO5), R9.1
CENTER_LED: IC5.22 (GPIO10), R16.2
ENABLE: IC5.27 (EN), J3.2
GND: C1.1, C2.1, C3.1, C4.1, C5.1, C6.1, C7.1, C8.1, C9.1, C12.1, C13.1, C14.1, C15.1, C17.1, C18.-, C19.C (-), CR2.P$2 (-), CR123A.P$2 (-), D2.C, D4.C, IC1.1 (GND), IC1.5 (SDO), IC1.7 (GND), IC2.3 (GND), IC3.1 (ADDR), IC3.EP (GND), IC4.2 (GND), IC4.3 (GND), IC5.4 (GND), J1.1 (2), J2.1, J3.1, JP2.4, JP3.4, JP6.4, Q1.2 (S), R7.1, R14.2, R19.2, R22.2, U1.5 (ADDR), U1.6 (GND), U2.4 (P$V-), U3.5 (GND), U3.7 (SA0/SDO), U3.10 (RES), U3.12 (GND), U3.15 (ADC2), U3.16 (ADC1)
GRIDEYE_INT: IC5.24 (GPIO12), U1.4 (INT)
GRIDEYE_WAKE: C13.2, C14.2, IC5.8 (GPIOA3), U1.9 (VDD), U1.13 (VPP)
IR_TRANSMITTER: IC5.6 (GPIOA1), R18.2
LIGHT_INT: IC2.5 (INT), IC5.23 (GPIO11), R5.1
MIC_AMP_IN: IC5.5 (GPIOA0), R6.2, U2.1 (OUT)
unnamed: R2.1, R6.1, U2.2 (-IN)
unnamed: D1.A, R15.1
unnamed: C10.2, R2.2
unnamed: U2.3 (+IN), U2.6 (-IN), U2.7 (OUT)
unnamed: D2.A, R1.1
unnamed: C10.1, IC4.1 (OUTPUT)
unnamed: D3.A, R17.1
unnamed: C9.2, R7.2, R12.1, U2.5 (+IN)
unnamed: D1.C, D3.C, Q1.3 (D)
unnamed: R12.2, R20.1
unnamed: IC5.7 (GPIOA2), R25.2
unnamed: C12.2, U1.12 (DVDD)
unnamed: C11.2, U1.10 (AVDD)
unnamed: C11.1, R14.1
unnamed: CR2.P$1 (+), D7.A, JP1.2
unnamed: Q1.1 (G), R18.1, R19.1
unnamed: F1.2, J1.2 (1)
unnamed: D4.A, R16.1
unnamed: R8.2, U3.8 (!CS!/MODE)
NTC_SENSE: IC3.4 (PWM), IC3.5 (SENSE), R28.1
RX: IC5.14 (GPIORX), JP3.1
SCL: IC1.4 (SCK), IC2.2 (SCL), IC3.10 (SCL), IC5.18 (GPIOSCL), JP6.1, R4.1, U1.3 (SCL), U3.4 (SCL/SPC)
SDA: IC1.3 (SDI), IC2.6 (SDA), IC3.9 (SDA), IC5.17 (GPIOSDA), JP6.2, R3.1, U1.2 (SDA), U3.6 (SDA/SDI)
SPI_MISO: IC5.13 (GPIOMISO), J2.4
SPI_MOSI: IC5.12 (GPIOMOSI), J2.3, R1.2
SPI_SCK: IC5.11 (GPIOSCK), J2.2
TX: IC5.15 (GPIOTX), JP3.2
USB: F1.1, IC5.26 (USB)
VBAT: CR123A.P$1 (+), D7.C, IC5.28 (VBAT), J3.3, JP1.1
VCCA: C8.2, C17.2, IC4.4 (VDD), R20.2, R24.2, R25.1, U2.8 (P$V+)

Notes on the sheet:
I2C Pullup
V6.1
Stephen Harrison
Xenon Datasheet: https://docs.particle.io/datasheets/mesh/xenon-datasheet/
Argon Datasheet: https://docs.particle.io/datasheets/wi-fi/argon-datasheet/
Pinout: https://docs.particle.io/assets/images/argon/argon-pinout-v1.0.pdf
D8: PWM1 A7: PWM0 D5:RX2 (Xenon) : PWM1 D4:TX2 (Xenon) : PWM1 D3: SCL1 : UART1 CTS : PWM3 D2: SDA1 : UART1 RTS : PWM3 D1: SCL D0: SDA
Replace with 10uF cap for AC coupling
Addr: 0x5A
Accelerometer - Tap detection.
MEMs microphone and amp. Sound level detection
IR Blaster
Thermal Camera
Battery (CR2) NOT RECHARGABLE!
Grove connectors
Feather - Particle Xenon/Argon
Sensors : Temperature, Humidity, Pressure, Gas, eCO2, Light
External Power Input
Addr: 0x76
TODO: Change to 10k I2C mode select.
V6 built with 0.1F Cap.
Leave ADC 3 disconnected as it may be used by internal temperature sensor.
Addr: 0x68 (v1: 0x69)
Int: Active Low
AVCC - analog power for microphone circuit is driven from A2 in Digital Output mode.
GPIO13 (aka D8) is the only pin that can wake from deep sleep by setting it high.
The 3rd-generation devices (Argon, Boron, Xenon) can only wake from SLEEP_MODE_DEEP by rising D8. It's not possible to exit SLEEP_MODE_DEEP based on time because the clock does not run in standby sleep mode on the nRF52. Also, the real-time-clock (Time class) will not be set when waking up from SLE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
System.sleep(uint16_t wakeUpPin, uint16_t edgeTriggerMode) can be used to put the entire device into a stopmode with wakeup on interrupt. In this particular mode, the device shuts down the network and puts the microcontroller in a stop mode with configurable wakeup pin and edge triggered interrupt.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
// Put the device into stop mode with wakeup using RISING edge interrupt on D1 and A4 pins // Specify the pins in-place (using std::initializer_list) System.sleep({D1, A4}, RISING);
INT1 - Connected to D8 on the Xenon which can be used to wake the device from deep sleep with a high pulse.
Battery (CR123A) RECHARGABLE
Note: Xenon can supply enough power through an IO Pin to directly power the GridEye.
Low power Enable support.
Optional: 0R to power from 3v3 rail
External Display SPI
V6.1 #1 and #2 PCBs using 100R
Remove R5: Little difference
Remove R10: Little difference
Accel @ 50Hz - removes 0.1-0.2mA
Remove R25: Little difference
Remove R1: Little difference
CCS_INT - During deep sleep is sourcing 1.5mA into Xenon
todo: resistor inline for int

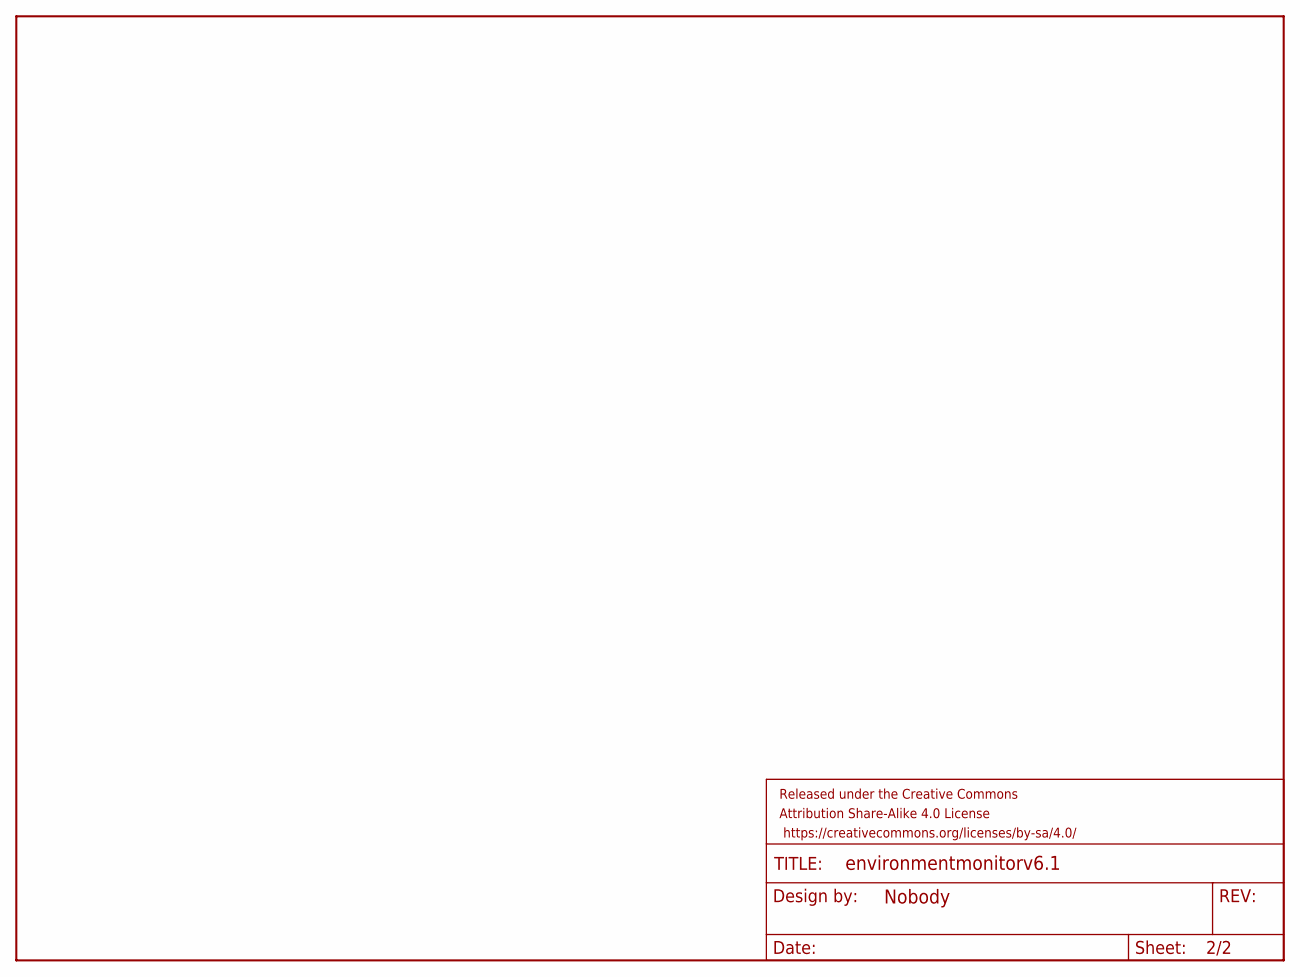
[picture p87: schematic EnvironmentMonitorV6.1.sch, sheet 2]

Parts:
FRAME2: FRAME-LETTERNO_PACKAGE; DUMMY
