ThingySticks/EnvironmentMonitor/Feather/V6/PCB/EnvironmentMonitorV6.1.brd

## EAGLE design Feather/V6/PCB/EnvironmentMonitorV6.1.brd (continued)

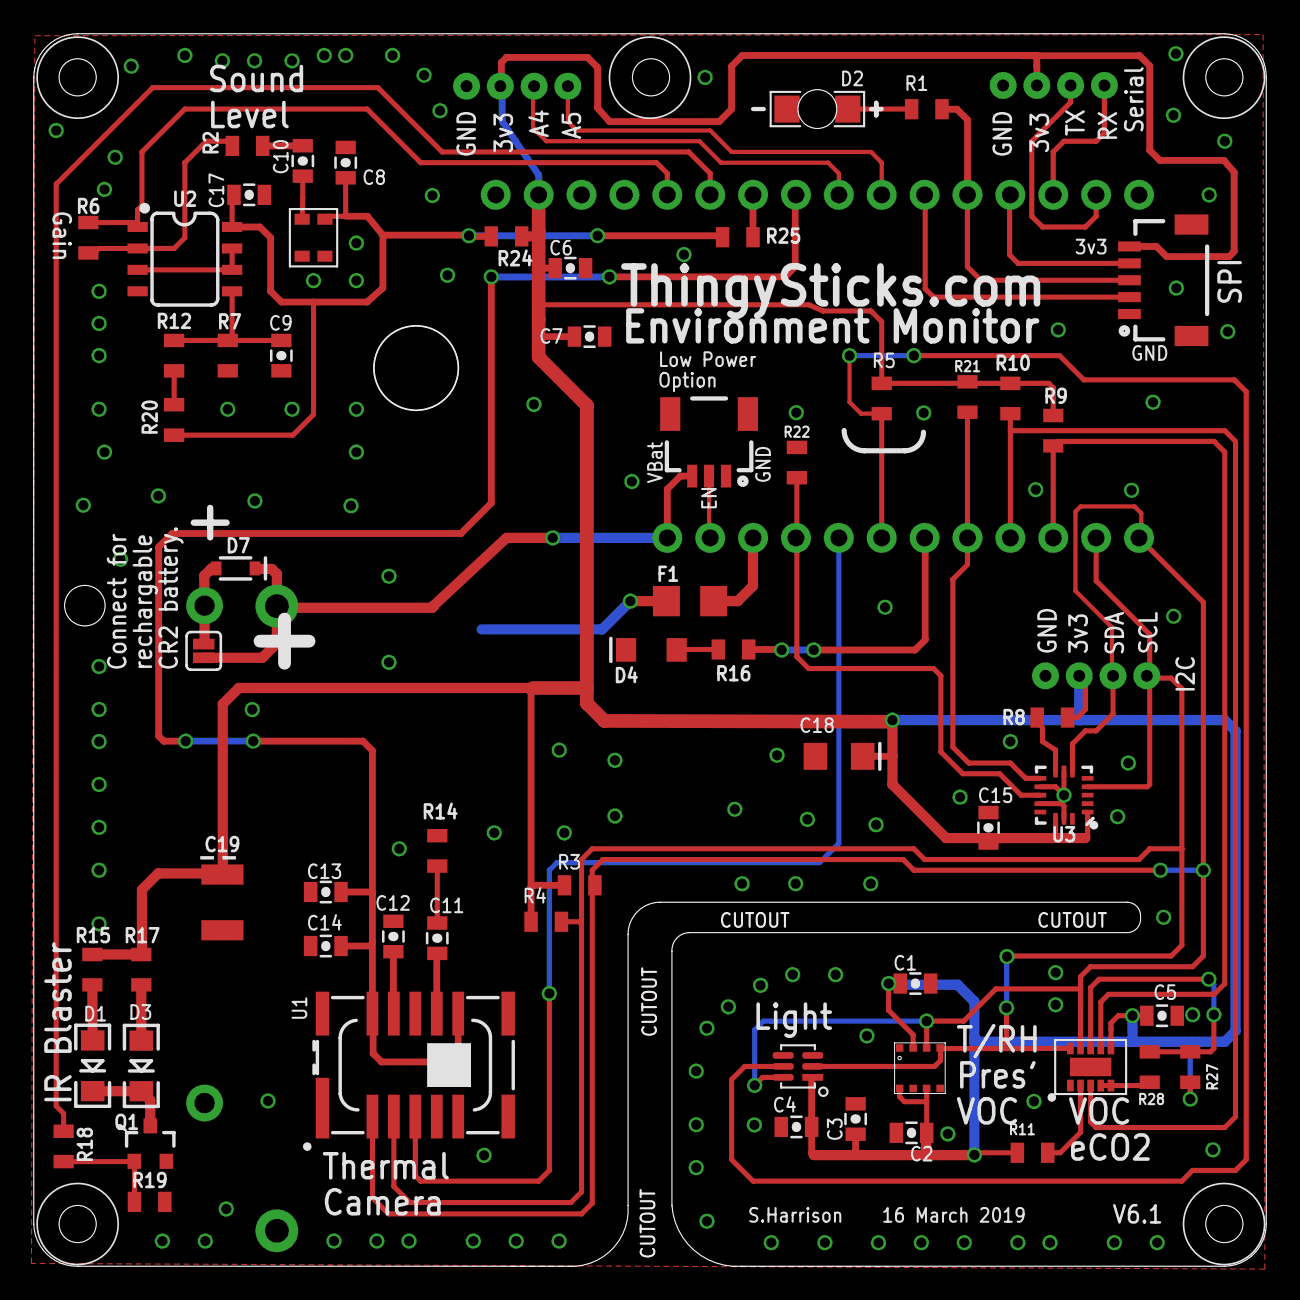
[picture p88: board EnvironmentMonitorV6.1.brd from above]

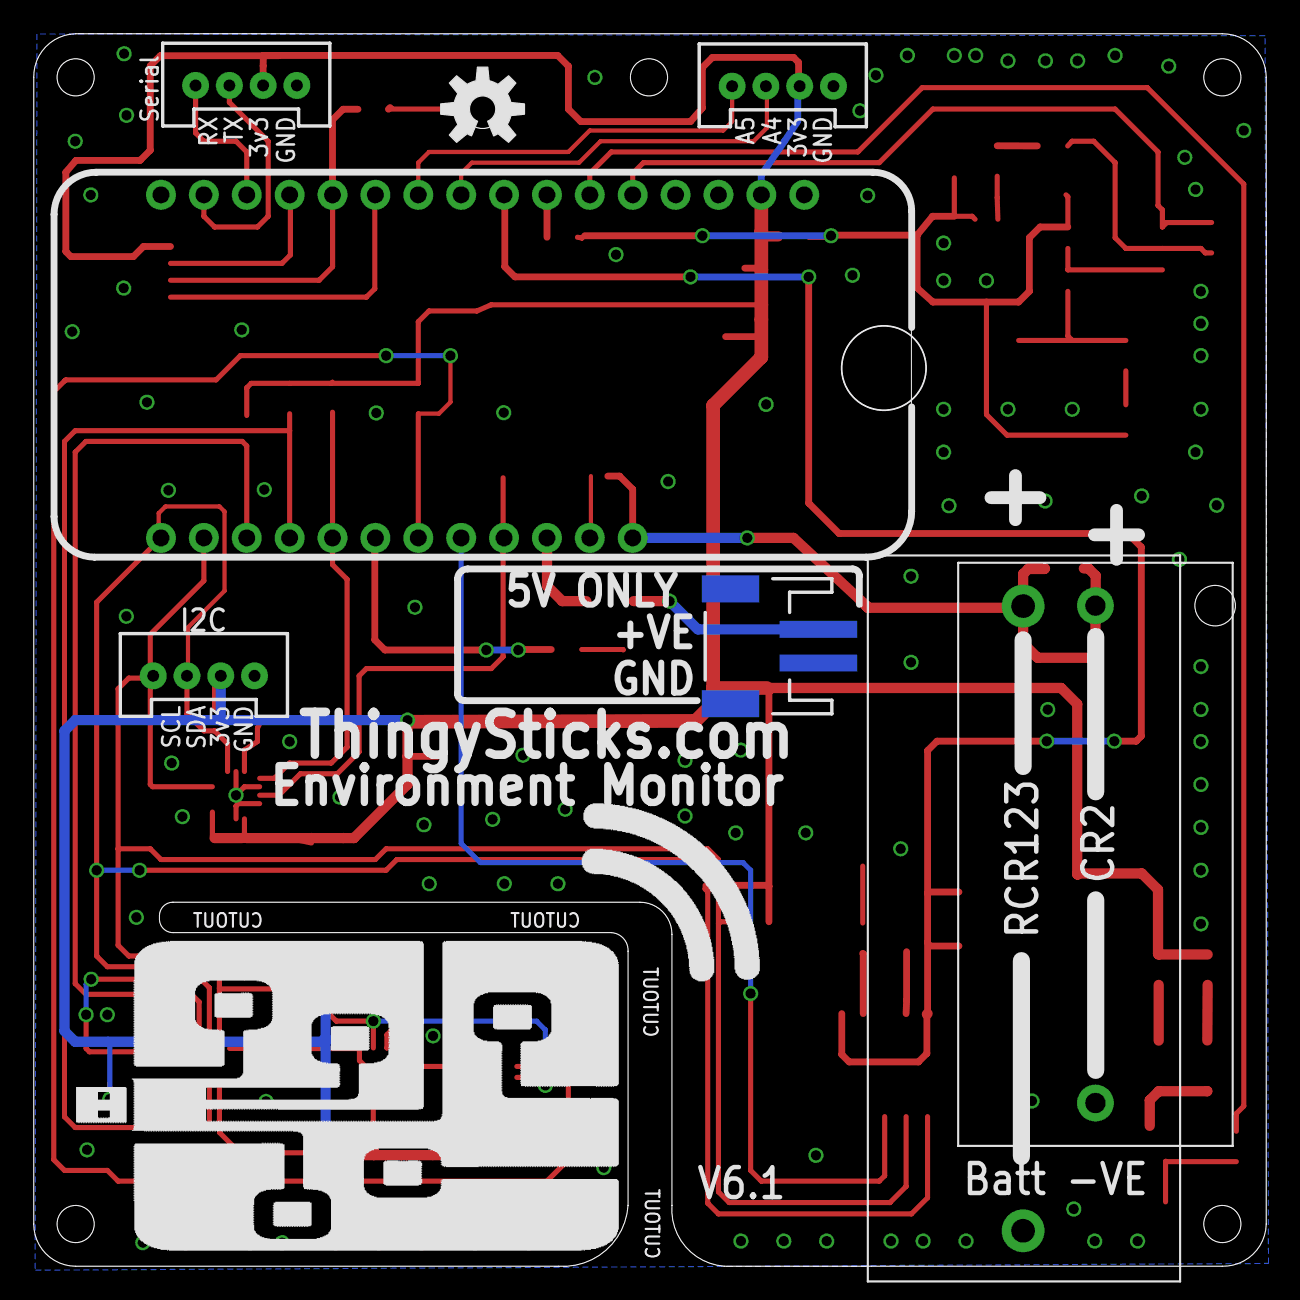
[picture p89: board EnvironmentMonitorV6.1.brd from below]

Board: 2 copper layers, 73.0 x 73.0 mm, 71 parts (9 on the bottom side), 47 nets.
