ThingySticks/EnvironmentMonitor/Feather/V6/Base PCBs/RS485/RS385BasePcb/Environment-V6-RS485-BasePcb.brd

## EAGLE design Feather/V6/Base PCBs/RS485/RS385BasePcb/Environment-V6-RS485-BasePcb.brd (2020-01-12)

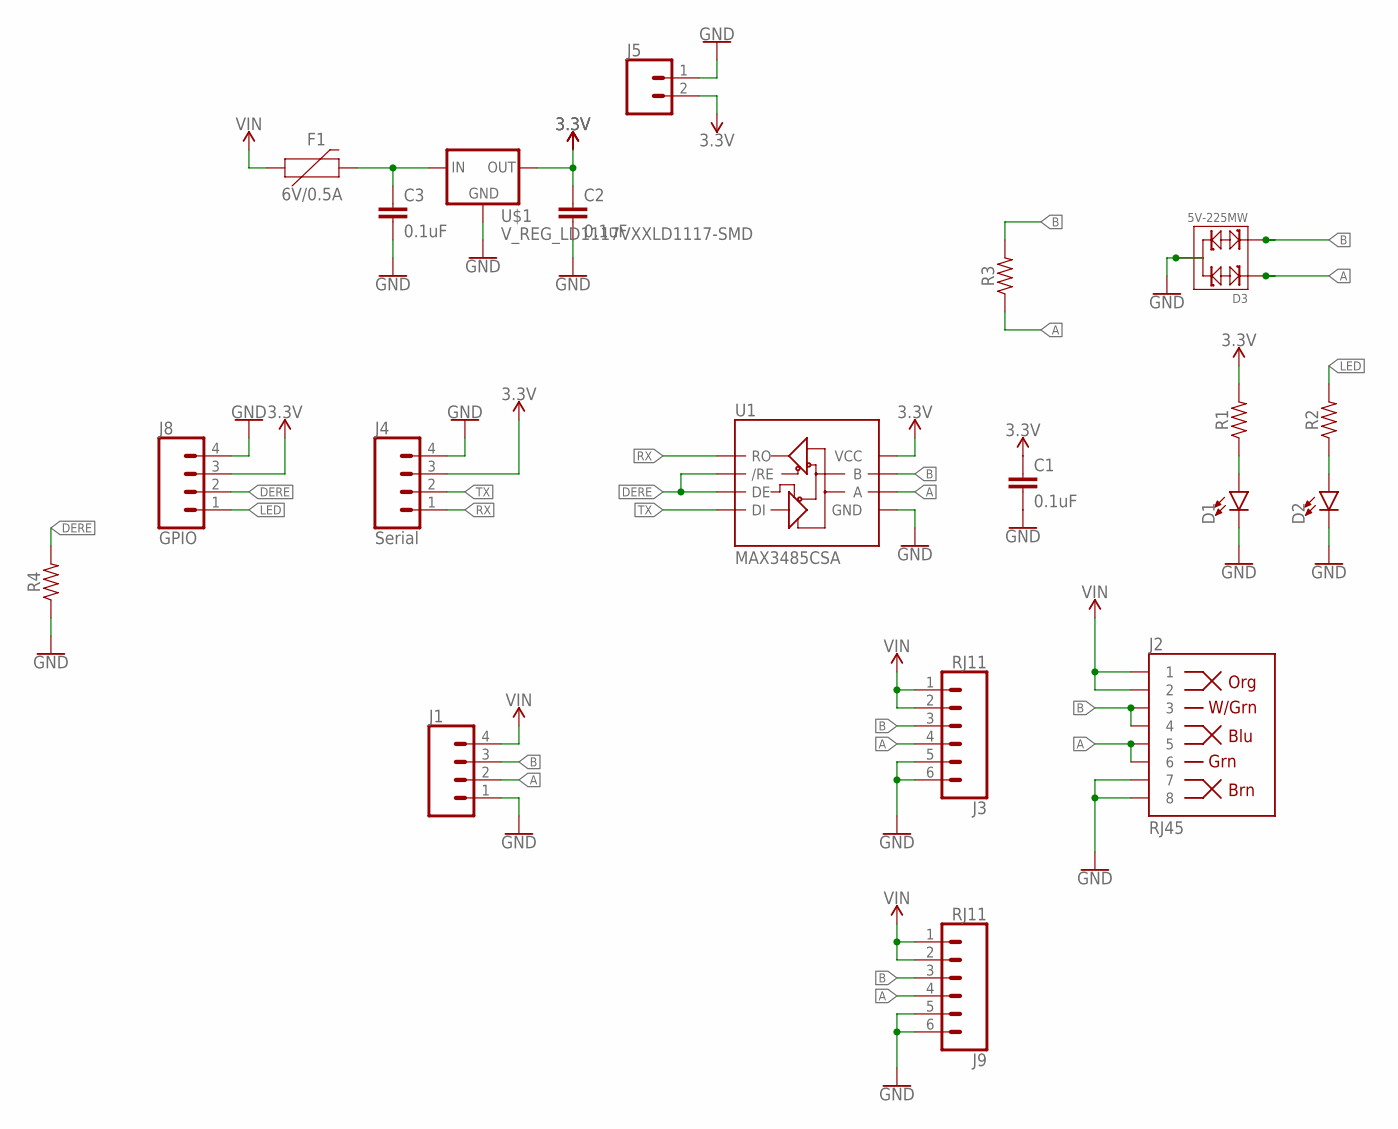
[picture p90: schematic Environment-V6-RS485-BasePcb.sch]

Parts:
C1, C2, C3: 0.1uF; 0805
D1, D2: LED1206; LED-1206
D3: 5V-225MW; SOT-23
F1: 6V/0.5A; 1206
J1: CONN_04SCREW; SCREWTERMINAL-3.5MM-4
J2: RJ45; RJ45-8
J3, J9: RJ11; RJ11-6
J4: Serial; JST-4-PH-GROVE
J5: CONN_02-JST-2MM-SMT; JST-2-SMD
J8: GPIO; JST-4-PH-GROVE
R1, R2, R3, R4: 0805
U1: MAX3485CSA; SO08
U$1: V_REG_LD1117VXXLD1117-SMD; SOT223

Connections:
3.3V: C1.1, C2.1, J4.3, J5.2 (1), J8.3, R1.2, U1.8 (VCC), U$1.2 (OUT)
A: D3.1, J1.2, J2.5, J2.6, J3.4, J9.4, R3.1, U1.6 (A)
B: D3.2, J1.3, J2.3, J2.4, J3.3, J9.3, R3.2, U1.7 (B)
DERE: J8.2, R4.2, U1.2 (/RE), U1.3 (DE)
GND: C1.2, C2.2, C3.2, D1.C, D2.C, D3.3, J1.1, J2.7, J2.8, J3.5, J3.6, J4.4, J5.1 (2), J8.4, J9.5, J9.6, R4.1, U1.5 (GND), U$1.1 (GND)
LED: J8.1, R2.2
unnamed: D2.A, R2.1
unnamed: C3.1, F1.2, U$1.3 (IN)
unnamed: D1.A, R1.1
RX: J4.1, U1.1 (RO)
TX: J4.2, U1.4 (DI)
VIN: F1.1, J1.4, J2.1, J2.2, J3.1, J3.2, J9.1, J9.2

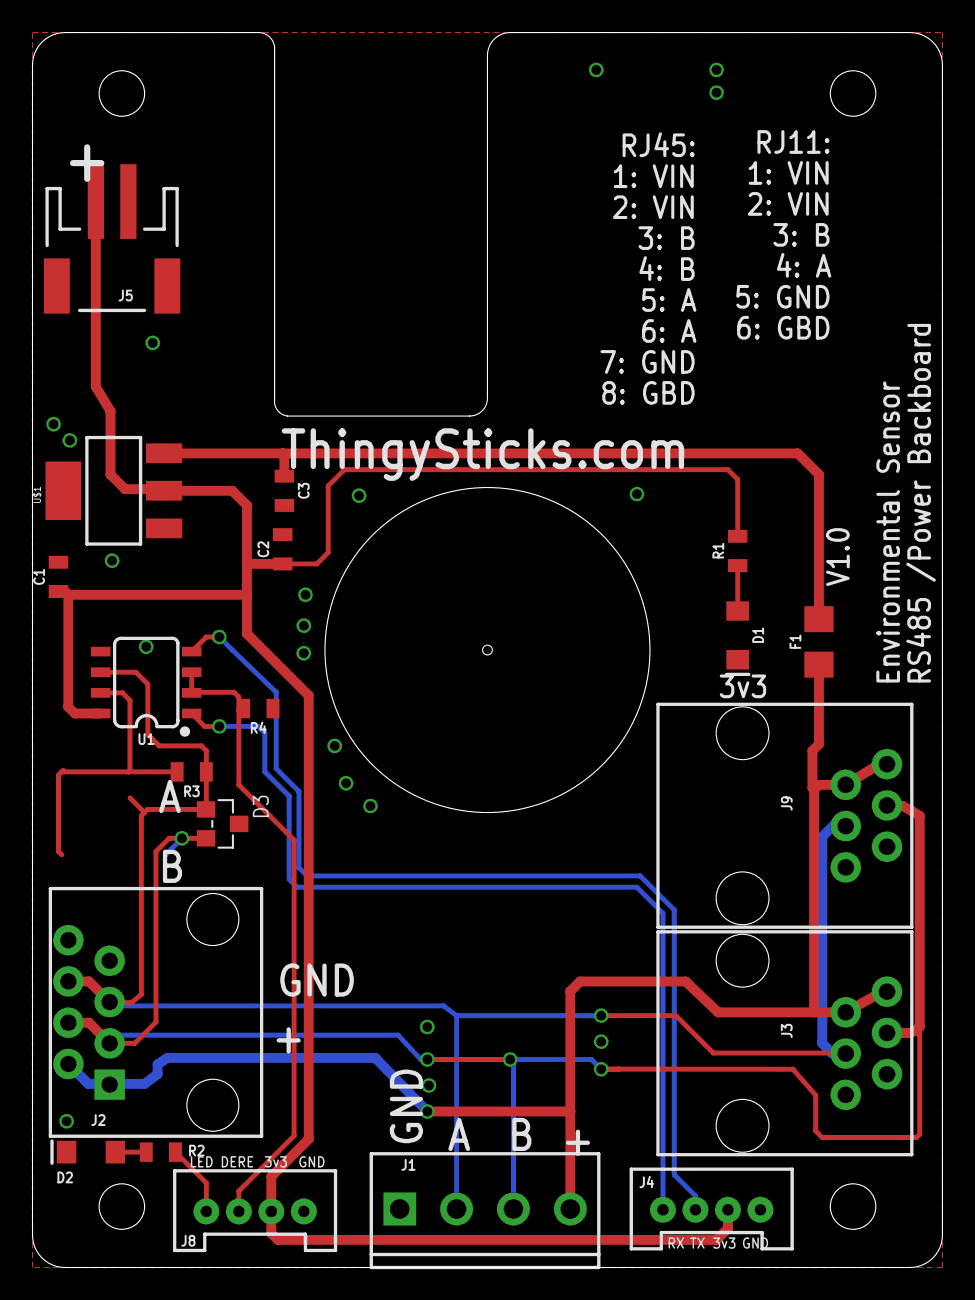
[picture p91: board Environment-V6-RS485-BasePcb.brd from above]

Board: 2 copper layers, 56.0 x 76.0 mm, 20 parts (0 on the bottom side), 12 nets.
