ThingySticks/EnvironmentMonitor/Feather/V5/PCB/EnvironmentMonitorV5.brd

## EAGLE design Feather/V5/PCB/EnvironmentMonitorV5.brd (2019-01-22, an earlier design)

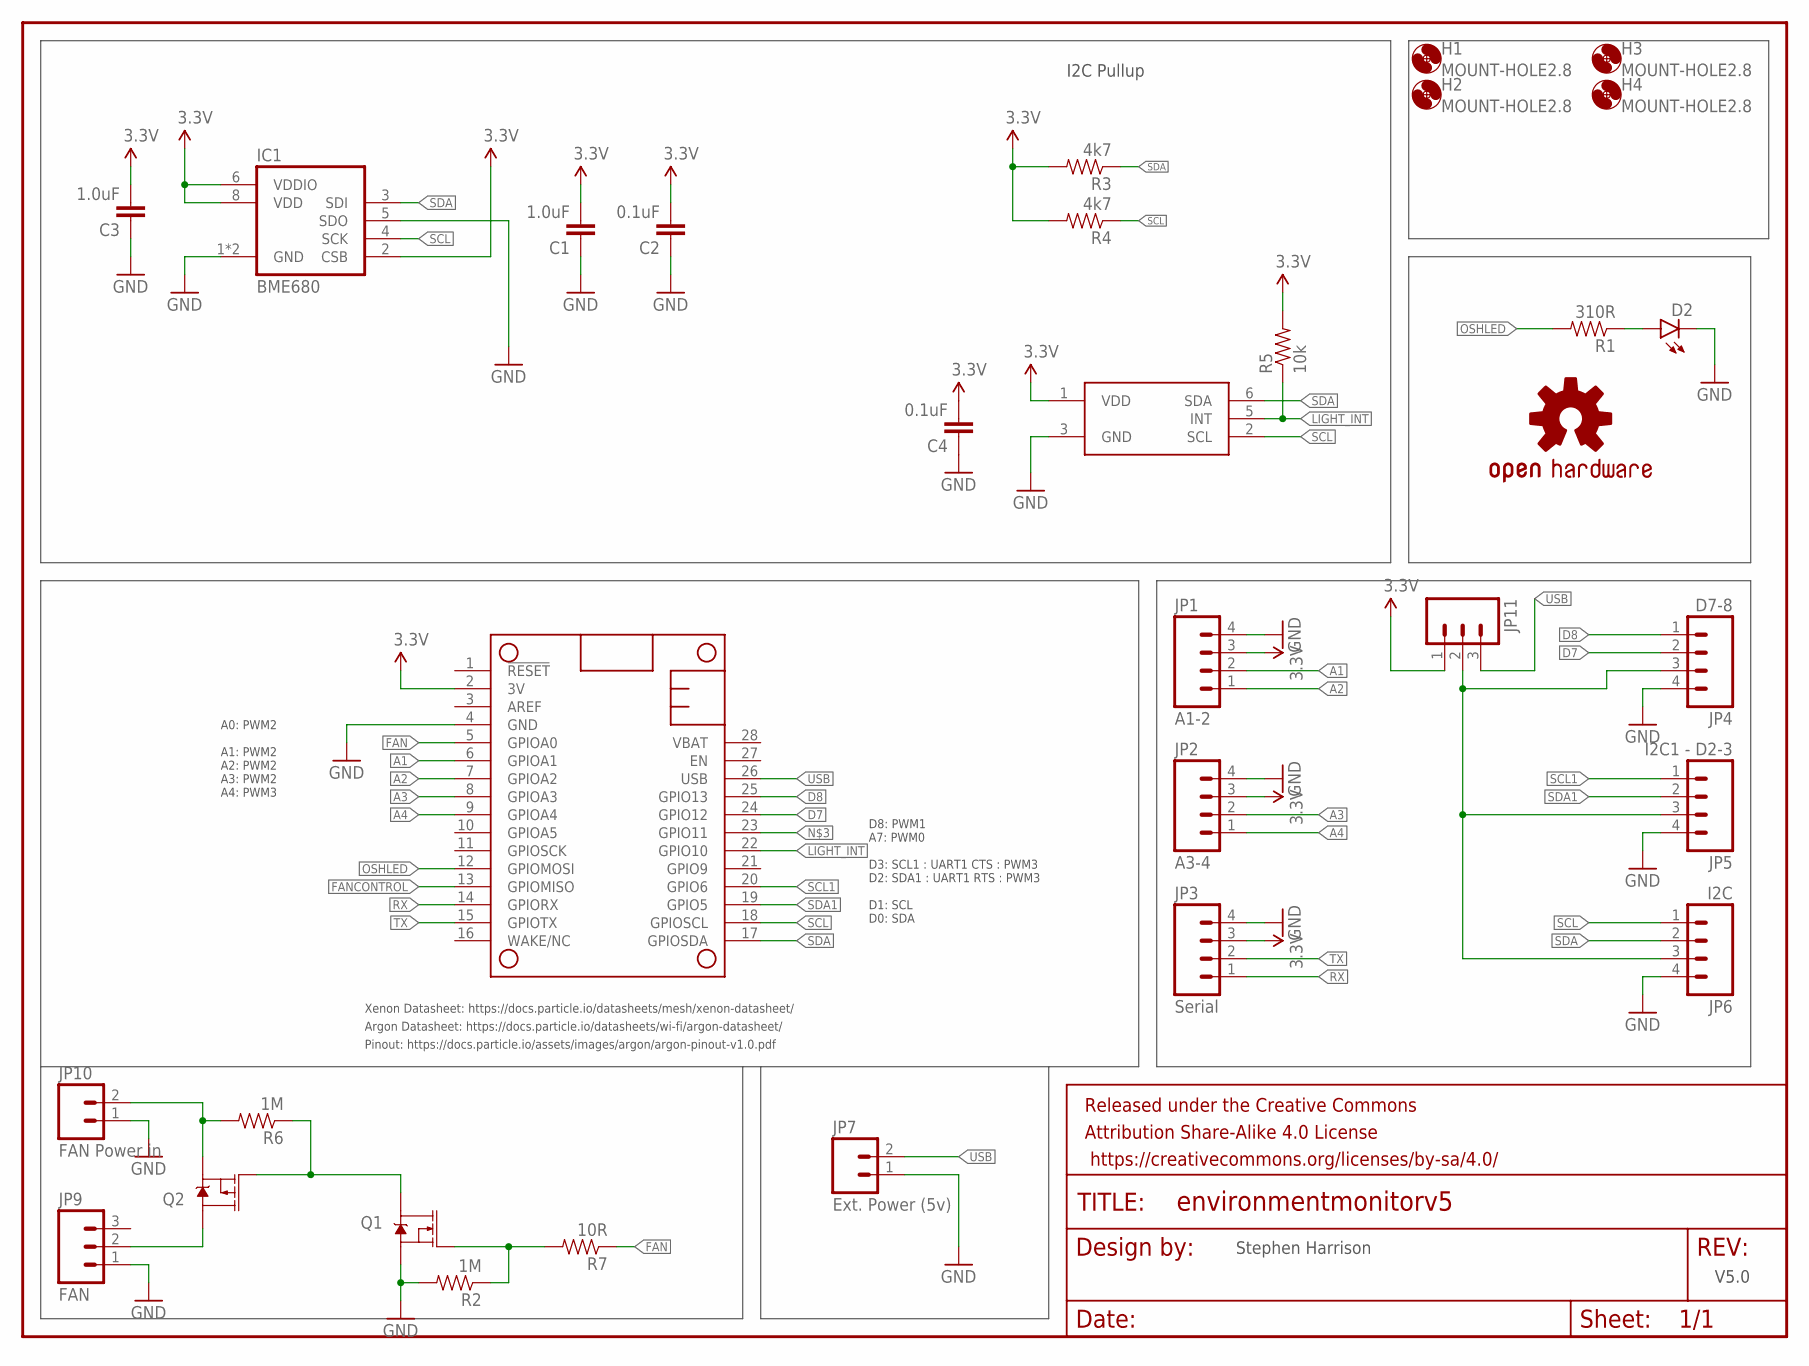
[picture p92: schematic EnvironmentMonitorV5.sch]

Parts:
C1, C3: 1.0uF; 0805-CAP
C2, C4: 0.1uF; 0805-CAP
D2: LED1206-BOTTOM; LED-1206-BOTTOM
FRAME1: FRAME-LETTER; CREATIVE_COMMONS
H1, H2, H3, H4: MOUNT-HOLE2.8; 2,8
IC1: BME680
IC2: TCS3472; FN-6
JP1: A1-2; JST-4-PTH-VERT
JP2: A3-4; JST-4-PTH-VERT
JP3: Serial; JST-4-PTH-VERT
JP4: D7-8; JST-4-PTH-VERT
JP5: I2C1 - D2-3; JST-4-PTH-VERT
JP6: I2C; JST-4-PTH-VERT
JP7: Ext. Power (5v); MOLEX-1X2_LOCK
JP9: FAN; MOLEX-1X3
JP10: FAN Power in; MOLEX-1X2_LOCK
JP11: M03PTH; 1X03
LOGO1: OSHW-LOGOM; OSHW-LOGO-M
MS1: FEATHERWING_NODIM; FEATHERWING_DIM
Q1: 220mA/50V/3.5Ω; SOT23-3
Q2: 4.3A/20V/54mΩ; SOT23-3
R1: 310R; 0805
R2, R6: 1M; 0805
R3, R4: 4k7; 0805
R5: 10k; 0805
R7: 10R; 0805

Connections:
3.3V: C1.2, C2.2, C3.2, C4.2, IC1.2 (CSB), IC1.6 (VDDIO), IC1.8 (VDD), IC2.1 (VDD), JP1.3, JP2.3, JP3.3, JP11.1, MS1.2 (3V), R3.2, R4.2, R5.2
A1: JP1.2, MS1.6 (GPIOA1)
A2: JP1.1, MS1.7 (GPIOA2)
A3: JP2.2, MS1.8 (GPIOA3)
A4: JP2.1, MS1.9 (GPIOA4)
D7: JP4.2, MS1.24 (GPIO12)
D8: JP4.1, MS1.25 (GPIO13)
FAN: MS1.5 (GPIOA0), R7.1
FANCONTROL: MS1.13 (GPIOMISO)
GND: C1.1, C2.1, C3.1, C4.1, D2.C, IC1.1 (GND), IC1.5 (SDO), IC1.7 (GND), IC2.3 (GND), JP1.4, JP2.4, JP3.4, JP4.4, JP5.4, JP6.4, JP7.1, JP9.1, JP10.1, MS1.4 (GND), Q1.2 (S), R2.2
LIGHT_INT: IC2.5 (INT), MS1.22 (GPIO10), R5.1
unnamed: JP10.2, Q2.2 (S), R6.2
unnamed: Q1.3 (D), Q2.1 (G), R6.1
unnamed: JP4.3, JP5.3, JP6.3, JP11.2
unnamed: Q1.1 (G), R2.1, R7.2
unnamed: D2.A, R1.1
unnamed: JP9.2, Q2.3 (D)
OSHLED: MS1.12 (GPIOMOSI), R1.2
RX: JP3.1, MS1.14 (GPIORX)
SCL: IC1.4 (SCK), IC2.2 (SCL), JP6.1, MS1.18 (GPIOSCL), R4.1
SCL1: JP5.1, MS1.20 (GPIO6)
SDA: IC1.3 (SDI), IC2.6 (SDA), JP6.2, MS1.17 (GPIOSDA), R3.1
SDA1: JP5.2, MS1.19 (GPIO5)
TX: JP3.2, MS1.15 (GPIOTX)
USB: JP7.2, JP11.3, MS1.26 (USB)

Notes on the sheet:
I2C Pullup
V5.0
Stephen Harrison
Xenon Datasheet: https://docs.particle.io/datasheets/mesh/xenon-datasheet/
Argon Datasheet: https://docs.particle.io/datasheets/wi-fi/argon-datasheet/
Pinout: https://docs.particle.io/assets/images/argon/argon-pinout-v1.0.pdf
A0: PWM2 A1: PWM2 A2: PWM2 A3: PWM2 A4: PWM3
D8: PWM1 A7: PWM0 D3: SCL1 : UART1 CTS : PWM3 D2: SDA1 : UART1 RTS : PWM3 D1: SCL D0: SDA

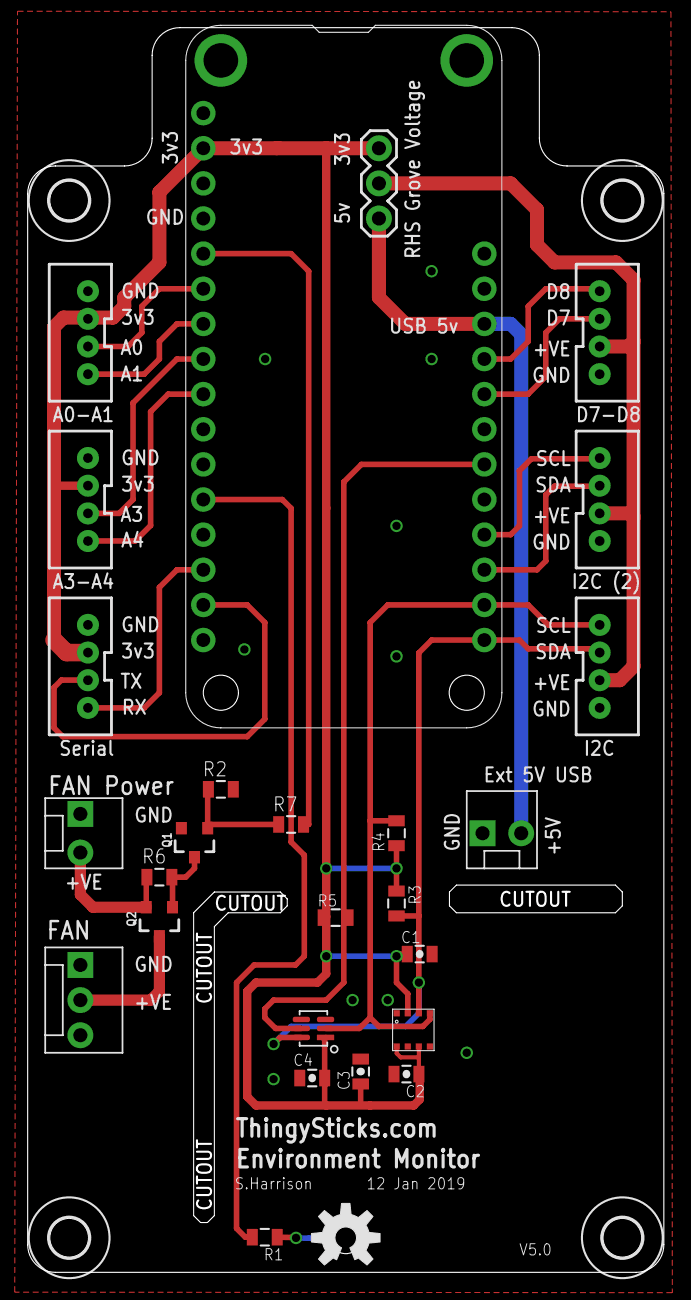
[picture p93: board EnvironmentMonitorV5.brd from above]

Board: 2 copper layers, 46.0 x 90.0 mm, 33 parts (1 on the bottom side), 24 nets.
