ThingySticks/EnvironmentMonitor/Feather/V5/PCB/EnvironmentMonitorV5.1.brd

## EAGLE design Feather/V5/PCB/EnvironmentMonitorV5.1.brd (2019-01-22, an earlier design)

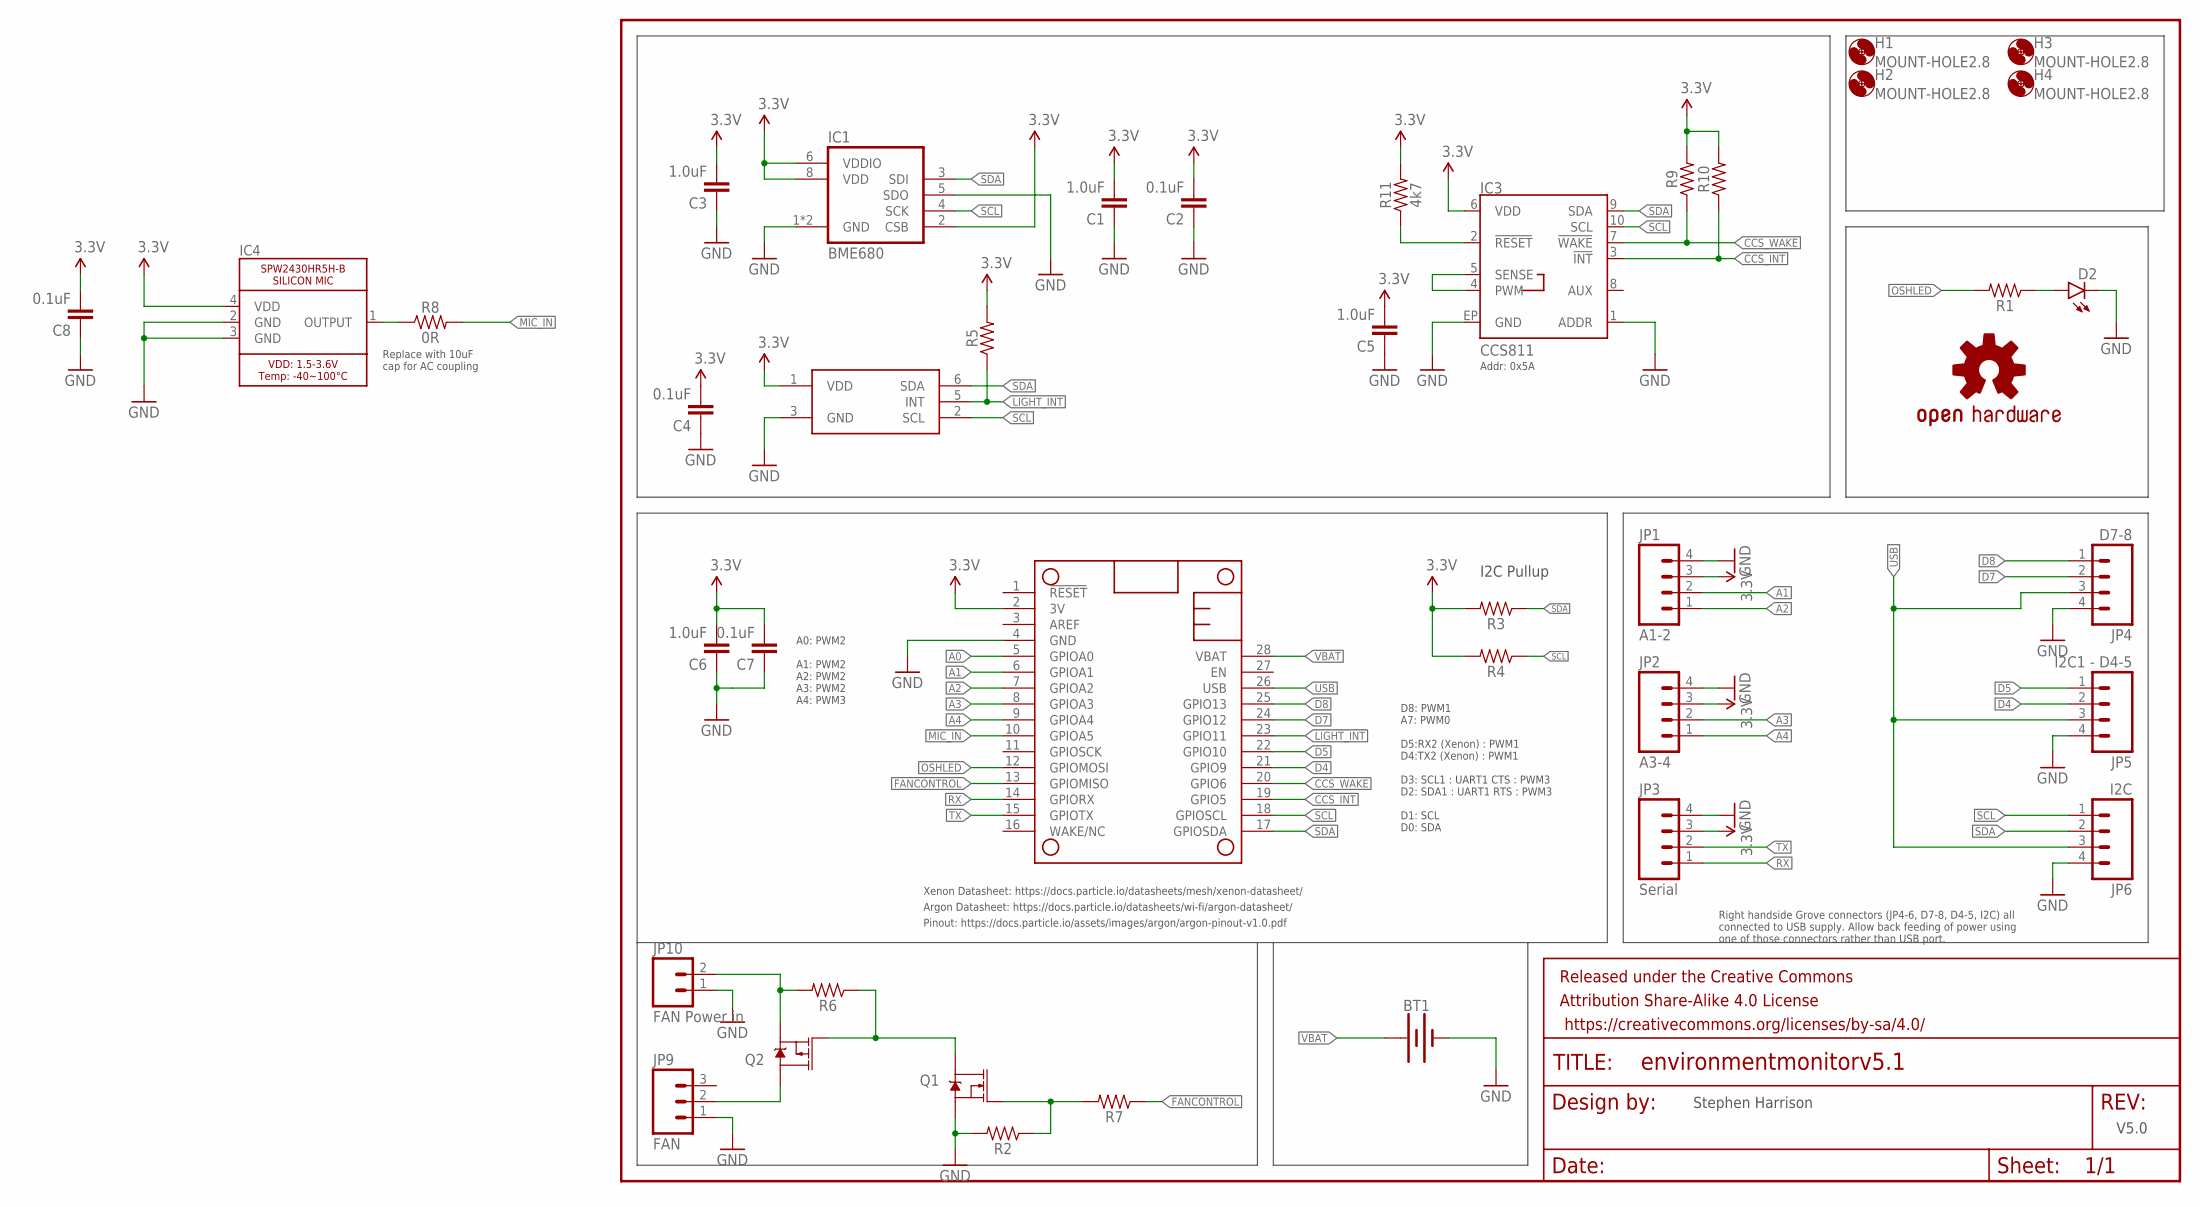
[picture p94: schematic EnvironmentMonitorV5.1.sch]

Parts:
BT1: BATTERY-16340; BATTERY_16340-HOLDER
C1, C3, C5, C6: 1.0uF; 0805-CAP
C2, C4, C7, C8: 0.1uF; 0805-CAP
D2: LED1206-BOTTOM; LED-1206-BOTTOM
FRAME1: FRAME-LETTER; CREATIVE_COMMONS
H1, H2, H3, H4: MOUNT-HOLE2.8; 2,8
IC1: BME680
IC2: TCS3472; FN-6
IC3: CCS811; LGA10
IC4: SPW2430HR5H-B
IC5: FEATHERWING_NODIM; FEATHERWING_DIM
JP1: A1-2; JST-4-PTH-VERT
JP2: A3-4; JST-4-PTH-VERT
JP3: Serial; JST-4-PTH-VERT
JP4: D7-8; JST-4-PTH-VERT
JP5: I2C1 - D4-5; JST-4-PTH-VERT
JP6: I2C; JST-4-PTH-VERT
JP9: FAN; MOLEX-1X3
JP10: FAN Power in; MOLEX-1X2_LOCK
LOGO1: OSHW-LOGOM; OSHW-LOGO-M
Q1: 220mA/50V/3.5Ω; SOT23-3
Q2: 4.3A/20V/54mΩ; SOT23-3
R1, R2, R3, R4, R5, R6, R7, R9, R10: 0805
R8: 0R; 0805
R11: 4k7; 0805

Connections:
3.3V: C1.2, C2.2, C3.2, C4.2, C5.2, C6.2, C7.2, C8.2, IC1.2 (CSB), IC1.6 (VDDIO), IC1.8 (VDD), IC2.1 (VDD), IC3.6 (VDD), IC4.4 (VDD), IC5.2 (3V), JP1.3, JP2.3, JP3.3, R3.2, R4.2, R5.2, R9.2, R10.2, R11.2
A0: IC5.5 (GPIOA0)
A1: IC5.6 (GPIOA1), JP1.2
A2: IC5.7 (GPIOA2), JP1.1
A3: IC5.8 (GPIOA3), JP2.2
A4: IC5.9 (GPIOA4), JP2.1
CCS8_RESET: IC3.2 (!RESET!), R11.1
CCS_INT: IC3.3 (!INT!), IC5.19 (GPIO5), R10.1
CCS_WAKE: IC3.7 (!WAKE!), IC5.20 (GPIO6), R9.1
D4: IC5.21 (GPIO9), JP5.2
D5: IC5.22 (GPIO10), JP5.1
D7: IC5.24 (GPIO12), JP4.2
D8: IC5.25 (GPIO13), JP4.1
FANCONTROL: IC5.13 (GPIOMISO), R7.1
GND: BT1.P$2 (-), C1.1, C2.1, C3.1, C4.1, C5.1, C6.1, C7.1, C8.1, D2.C, IC1.1 (GND), IC1.5 (SDO), IC1.7 (GND), IC2.3 (GND), IC3.1 (ADDR), IC3.EP (GND), IC4.2 (GND), IC4.3 (GND), IC5.4 (GND), JP1.4, JP2.4, JP3.4, JP4.4, JP5.4, JP6.4, JP9.1, JP10.1, Q1.2 (S), R2.2
LIGHT_INT: IC2.5 (INT), IC5.23 (GPIO11), R5.1
MIC_IN: IC5.10 (GPIOA5), R8.2
unnamed: JP10.2, Q2.2 (S), R6.2
unnamed: Q1.3 (D), Q2.1 (G), R6.1
unnamed: IC3.4 (PWM), IC3.5 (SENSE)
unnamed: Q1.1 (G), R2.1, R7.2
unnamed: D2.A, R1.1
unnamed: IC4.1 (OUTPUT), R8.1
unnamed: JP9.2, Q2.3 (D)
OSHLED: IC5.12 (GPIOMOSI), R1.2
RX: IC5.14 (GPIORX), JP3.1
SCL: IC1.4 (SCK), IC2.2 (SCL), IC3.10 (SCL), IC5.18 (GPIOSCL), JP6.1, R4.1
SDA: IC1.3 (SDI), IC2.6 (SDA), IC3.9 (SDA), IC5.17 (GPIOSDA), JP6.2, R3.1
TX: IC5.15 (GPIOTX), JP3.2
USB: IC5.26 (USB), JP4.3, JP5.3, JP6.3
VBAT: BT1.P$1 (+), IC5.28 (VBAT)

Notes on the sheet:
I2C Pullup
V5.0
Stephen Harrison
Xenon Datasheet: https://docs.particle.io/datasheets/mesh/xenon-datasheet/
Argon Datasheet: https://docs.particle.io/datasheets/wi-fi/argon-datasheet/
Pinout: https://docs.particle.io/assets/images/argon/argon-pinout-v1.0.pdf
A0: PWM2 A1: PWM2 A2: PWM2 A3: PWM2 A4: PWM3
D8: PWM1 A7: PWM0 D5:RX2 (Xenon) : PWM1 D4:TX2 (Xenon) : PWM1 D3: SCL1 : UART1 CTS : PWM3 D2: SDA1 : UART1 RTS : PWM3 D1: SCL D0: SDA
Replace with 10uF cap for AC coupling
Addr: 0x5A
Right handside Grove connectors (JP4-6, D7-8, D4-5, I2C) all connected to USB supply. Allow back feeding of power using one of those connectors rather than USB port.

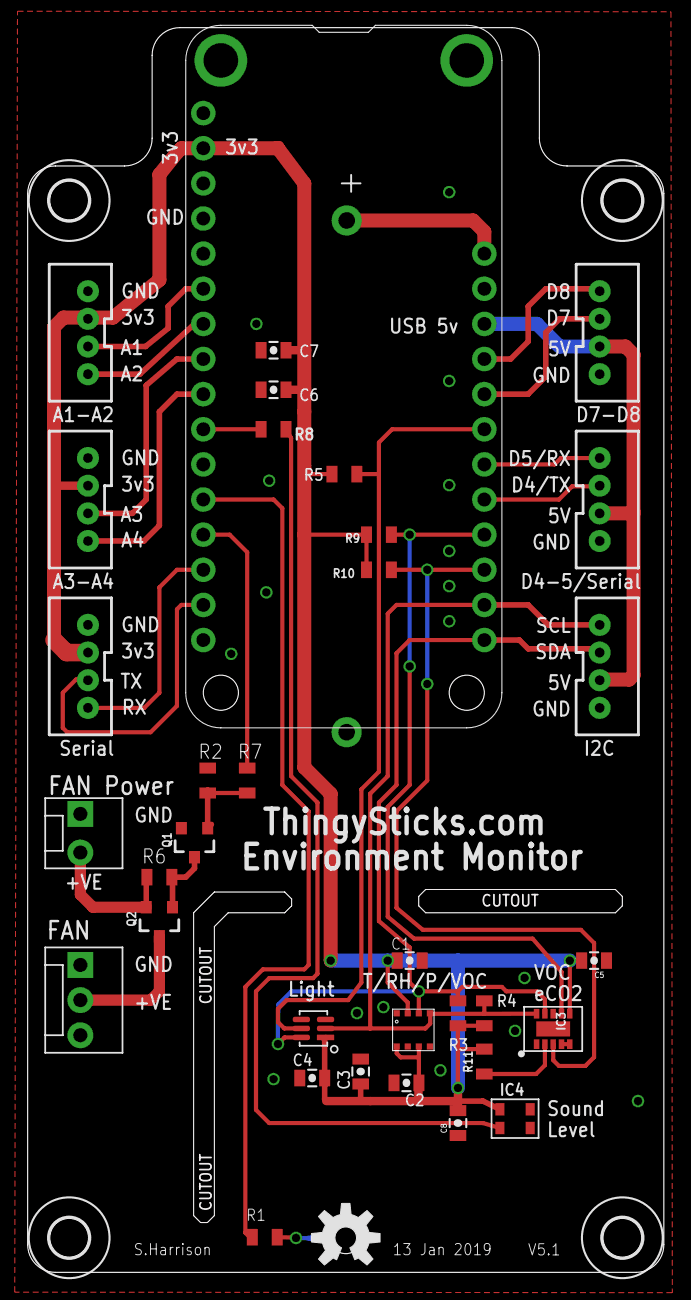
[picture p95: board EnvironmentMonitorV5.1.brd from above]

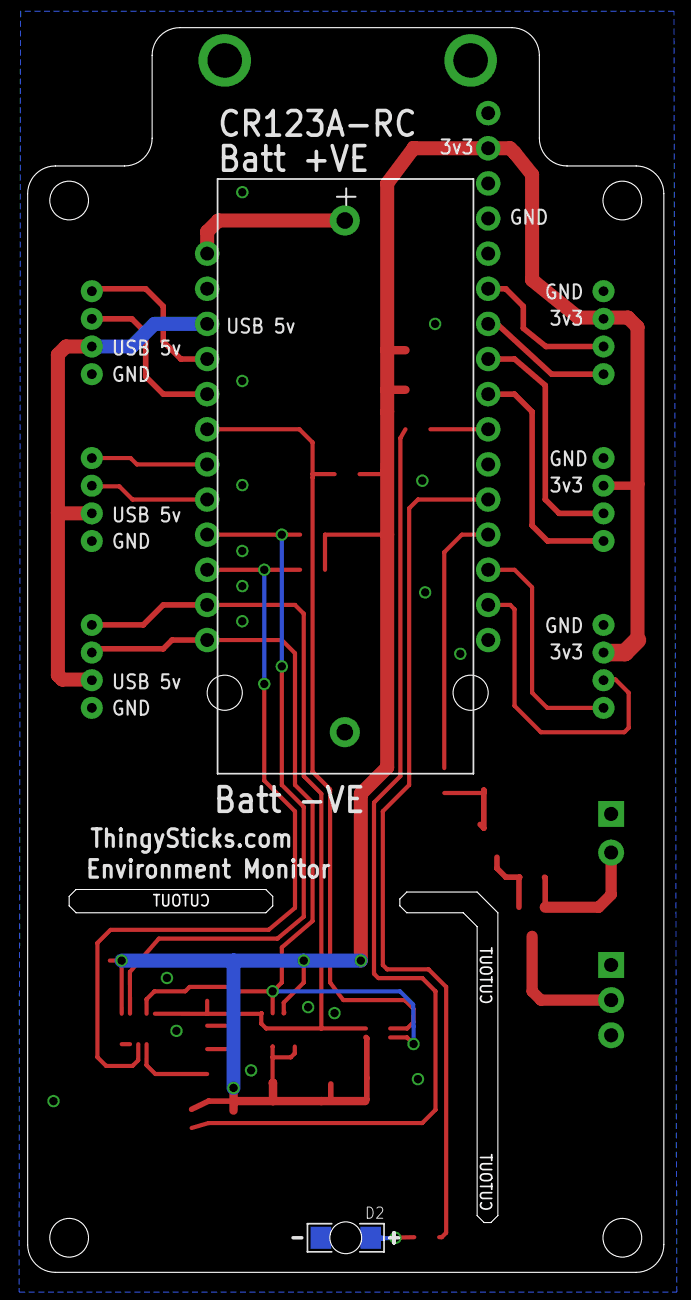
[picture p96: board EnvironmentMonitorV5.1.brd from below]

Board: 2 copper layers, 46.0 x 90.0 mm, 42 parts (2 on the bottom side), 30 nets.
