ThingySticks/EnvironmentMonitor/Electron/V3/PCB/EnvironmentMonitorV3.brd

## EAGLE design Electron/V3/PCB/EnvironmentMonitorV3.brd (2018-02-17, an earlier design)

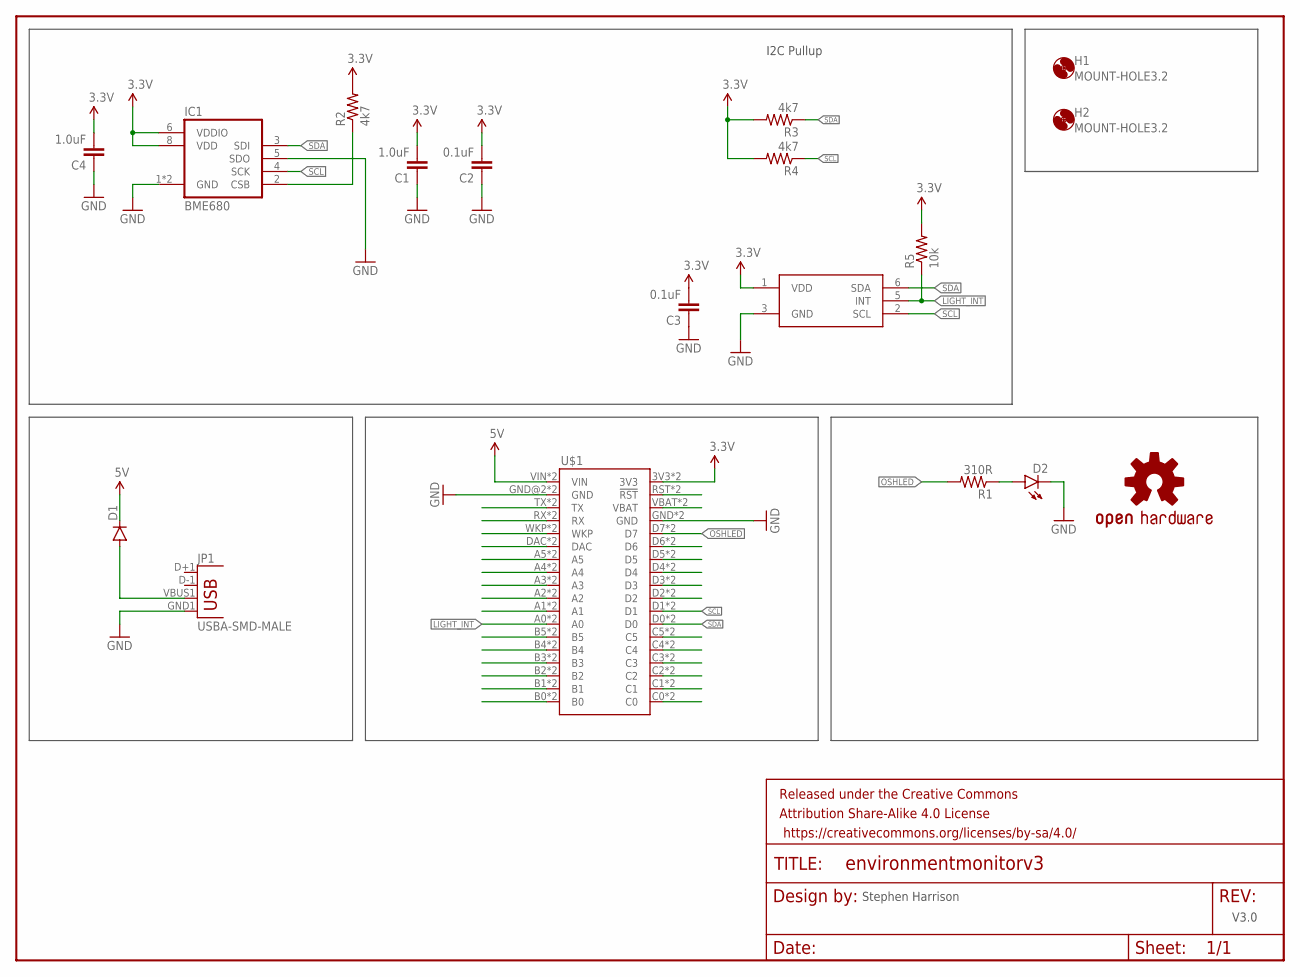
[picture p97: schematic EnvironmentMonitorV3.sch]

Parts:
C1, C4: 1.0uF; 0805-CAP
C2, C3: 0.1uF; 0805-CAP
D1: DIODESMA; SMA-DIODE
D2: LED1206-BOTTOM; LED-1206-BOTTOM
FRAME1: FRAME-LETTER; CREATIVE_COMMONS
H1, H2: MOUNT-HOLE3.2; 3,2
IC1: BME680
JP1: USBA-SMD-MALE; USB-A-SMT-MALE
LOGO1: OSHW-LOGOM; OSHW-LOGO-M
R1: 310R; 0805
R2, R3, R4: 4k7; 0805
R5: 10k; 0805
U$1: ELECTRONDUALNAMED; ELECTRON_SIMPLE_SILK_NAMES_DUAL
U$2: TCS3472; FN-6

Connections:
3.3V: C1.2, C2.2, C3.2, C4.2, IC1.6 (VDDIO), IC1.8 (VDD), R2.2, R3.2, R4.2, R5.2, U$1.3V3, U$1.3V3_1 (3V3), U$2.1 (VDD)
5V: D1.C, U$1.VIN, U$1.VIN_1B (VIN)
GND: C1.1, C2.1, C3.1, C4.1, D2.C, IC1.1 (GND), IC1.5 (SDO), IC1.7 (GND), JP1.GND1 (GND), U$1.GND, U$1.GND@2 (GND), U$1.GND_1 (GND), U$1.GND_1B (GND), U$2.3 (GND)
LIGHT_INT: R5.1, U$1.A0, U$1.A0_1 (A0), U$2.5 (INT)
unnamed: U$1.RST (!RST), U$1.RST_1 (!RST)
unnamed: U$1.VBAT, U$1.VBATT_1 (VBAT)
unnamed: IC1.2 (CSB), R2.1
unnamed: U$1.D6, U$1.D6_1 (D6)
unnamed: D1.A, JP1.VBUS1 (VBUS)
unnamed: D2.A, R1.1
unnamed: U$1.D5, U$1.D5_1 (D5)
unnamed: U$1.D2, U$1.D2_1 (D2)
unnamed: U$1.D4, U$1.D4_1 (D4)
unnamed: U$1.D3, U$1.D3_1 (D3)
unnamed: U$1.C5, U$1.C5_1 (C5)
unnamed: U$1.C4, U$1.C4_1 (C4)
unnamed: U$1.C3, U$1.C3_1 (C3)
unnamed: U$1.C2, U$1.C2_1 (C2)
unnamed: U$1.C1, U$1.C1_1 (C1)
unnamed: U$1.C0, U$1.C0_1 (C0)
unnamed: U$1.B0, U$1.B0_1 (B0)
unnamed: U$1.B1, U$1.B1_1 (B1)
unnamed: U$1.B2, U$1.B2_1 (B2)
unnamed: U$1.B3, U$1.B3_1 (B3)
unnamed: U$1.B4, U$1.B4_1 (B4)
unnamed: U$1.B5, U$1.B5_1 (B5)
unnamed: U$1.A1, U$1.A1_1 (A1)
unnamed: U$1.A2, U$1.A2_1 (A2)
unnamed: U$1.A3, U$1.A3_1 (A3)
unnamed: U$1.A4, U$1.A4_1 (A4)
unnamed: U$1.A5, U$1.A5_1 (A5)
unnamed: U$1.DAC, U$1.DAC_1 (DAC)
unnamed: U$1.WKP, U$1.WKP_1 (WKP)
unnamed: U$1.RX, U$1.RX_1 (RX)
unnamed: U$1.TX, U$1.TX_1 (TX)
OSHLED: R1.2, U$1.D7, U$1.D7_1 (D7)
SCL: IC1.4 (SCK), R4.1, U$1.D1, U$1.D1_1 (D1), U$2.2 (SCL)
SDA: IC1.3 (SDI), R3.1, U$1.D0, U$1.D0_1 (D0), U$2.6 (SDA)

Notes on the sheet:
I2C Pullup
V3.0
Stephen Harrison

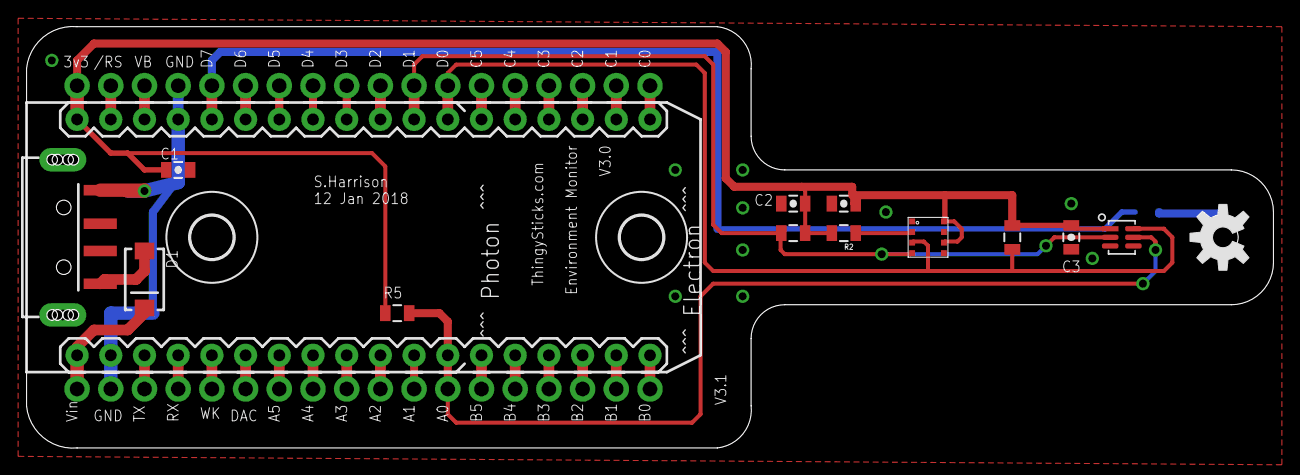
[picture p98: board EnvironmentMonitorV3.brd from above]

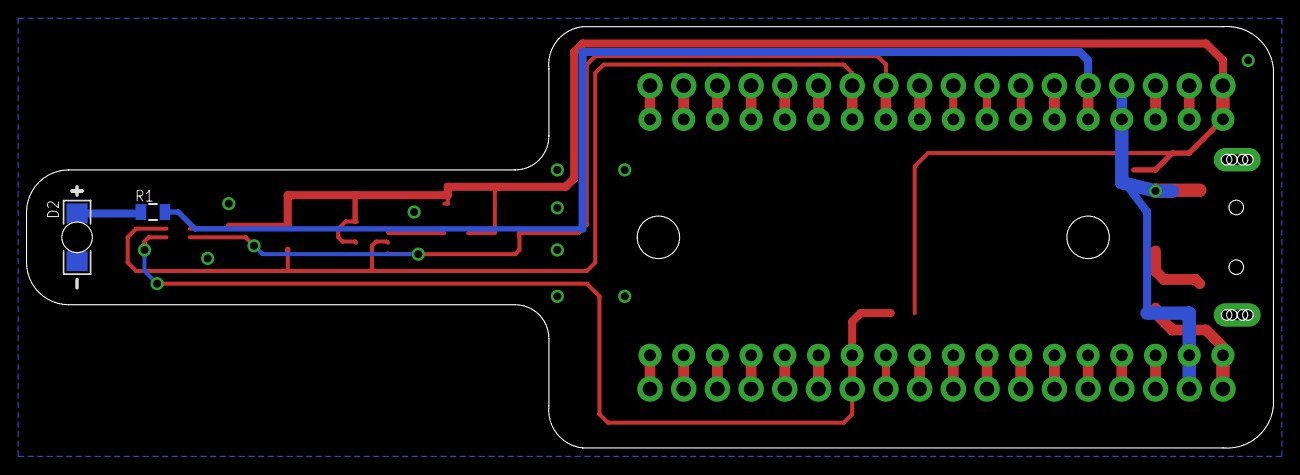
[picture p99: board EnvironmentMonitorV3.brd from below]

Board: 2 copper layers, 94.0 x 31.8 mm, 19 parts (2 on the bottom side), 38 nets.
