ThingySticks/EnvironmentMonitor/Arduino/V1/PCB/ArduinoAirQuailtyTop.brd

## EAGLE design Arduino/V1/PCB/ArduinoAirQuailtyTop.brd (2018-02-17)

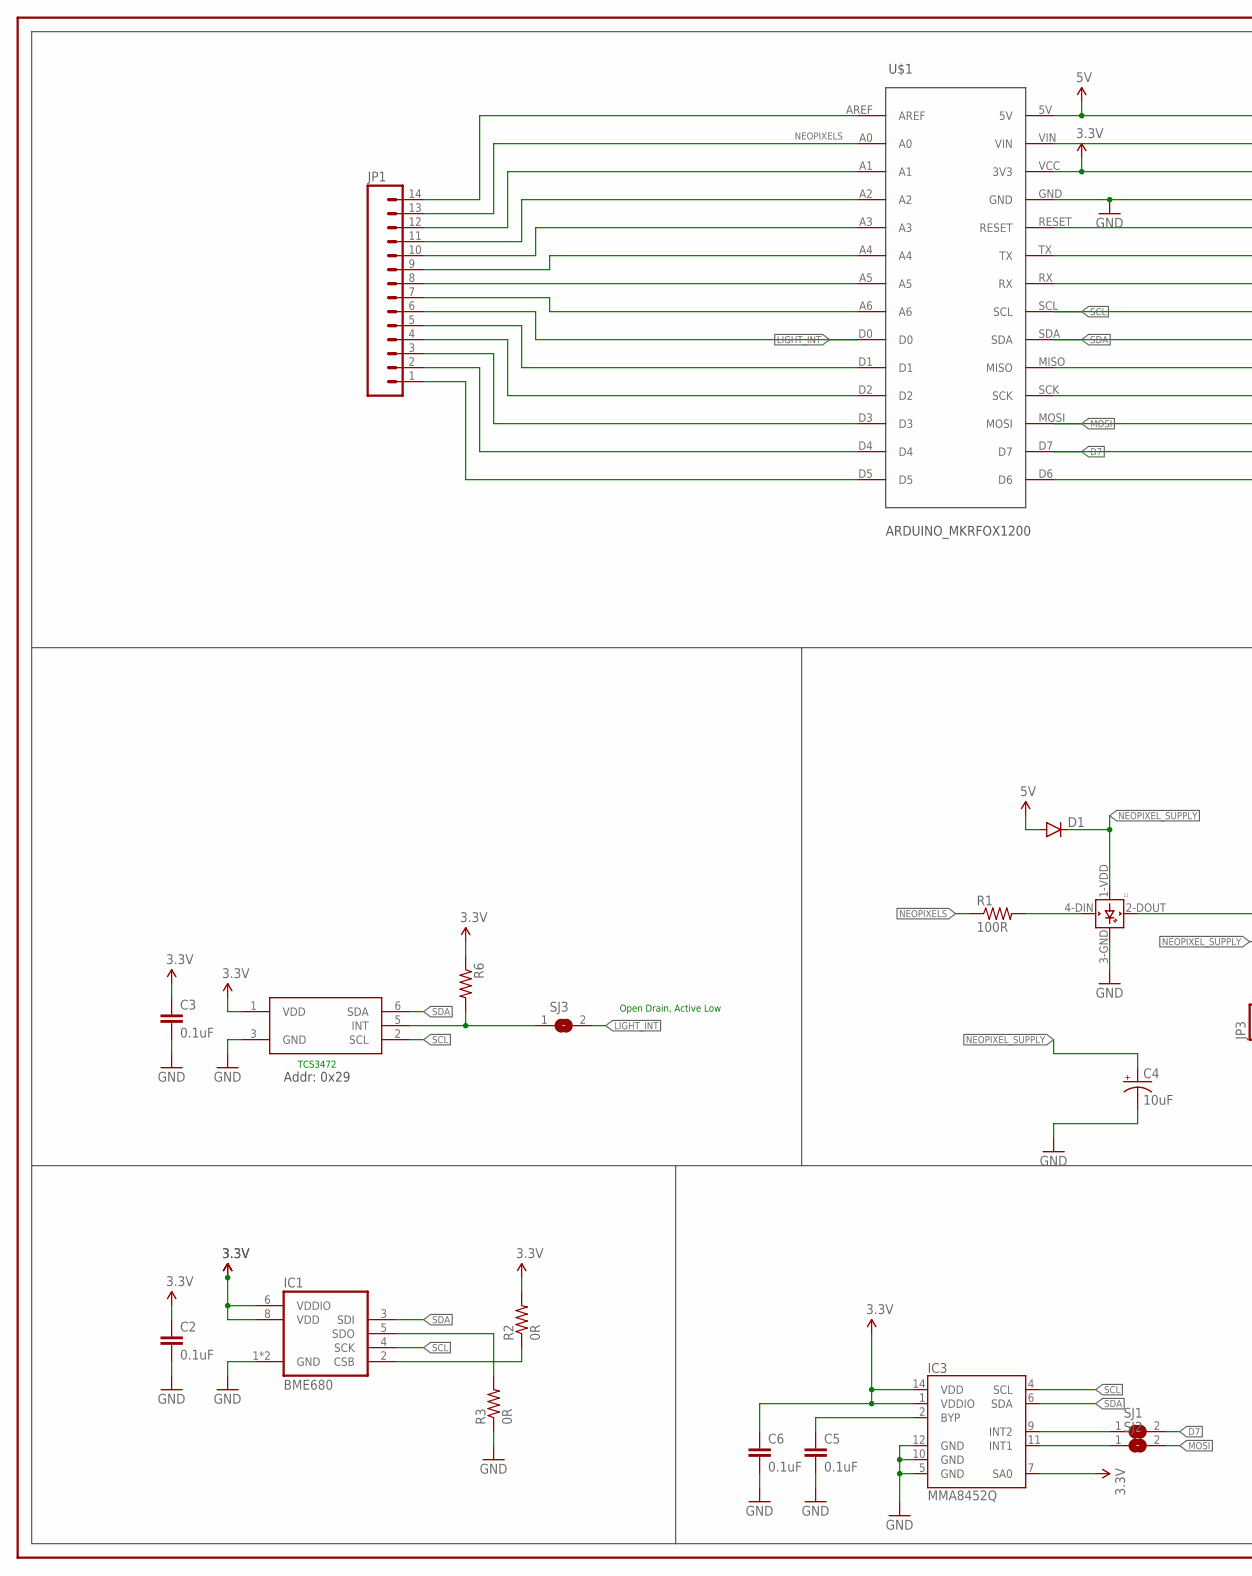
[picture p100: schematic ArduinoAirQuailtyTop.sch, part in row 1, column 1]

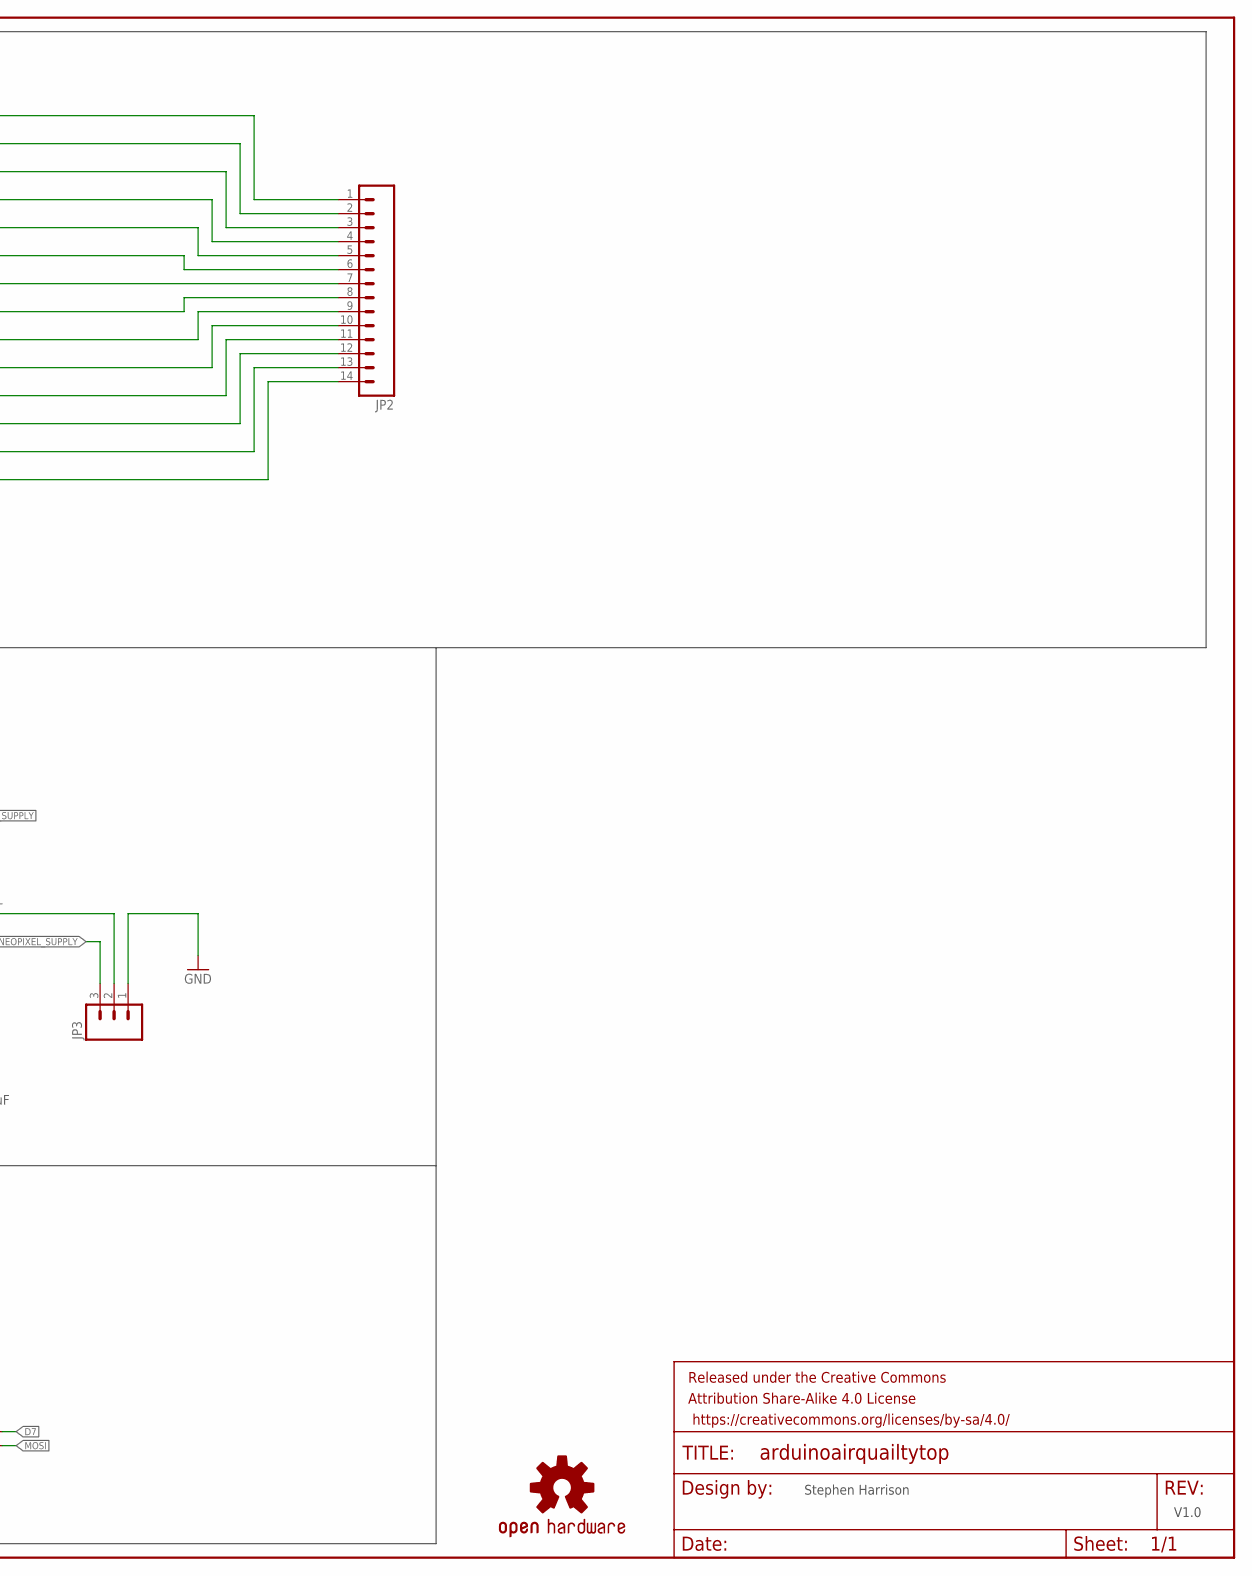
[picture p101: schematic ArduinoAirQuailtyTop.sch, part in row 1, column 2]

Parts:
C2, C3, C5, C6: 0.1uF; 0805
C4: 10uF; EIA3216
D1: DIODESMA; SMA-DIODE
FRAME1: FRAME-LEDGER; CREATIVE_COMMONS
IC1: BME680; MOUSER 262-BME680
IC2: TCS34725FN; FN-6; MOUSER 985-TCS34725FN
IC3: MMA8452Q; QFN-16_0.5MM; MOUSER 841-MMA8452QT
JP1, JP2: M14; 1X14
JP3: M03POLAR; MOLEX-1X3
L1: WS2812B
LOGO1: OSHW-LOGOM; OSHW-LOGO-M
R1: 100R; 0805
R2, R3: 0R; 0805
R6: RESISTOR0805-RES; 0805
SJ1, SJ2, SJ3: SJ
U$1: ARDUINO_MKRFOX1200

Connections:
3.3V: C2.1, C3.1, C6.1, IC1.6 (VDDIO), IC1.8 (VDD), IC2.1 (VDD), IC3.1 (VDDIO), IC3.7 (SA0), IC3.14 (VDD), JP2.3, R2.2, R6.1, U$1.VCC (3V3)
5V: D1.A, JP2.1, U$1.5V
D7: JP2.13, SJ1.2, U$1.D7
GND: C2.2, C3.2, C4.C (-), C5.2, C6.2, IC1.1 (GND), IC1.7 (GND), IC2.3 (GND), IC3.5 (GND), IC3.10 (GND), IC3.12 (GND), JP2.4, JP3.1, L1.3-GND (GND), R3.1, U$1.GND
LIGHT_INT: JP1.6, SJ3.2, U$1.D0
MOSI: JP2.12, SJ2.2, U$1.MOSI
unnamed: IC3.9 (INT2), SJ1.1
unnamed: IC3.11 (INT1), SJ2.1
unnamed: JP1.1, U$1.D5
unnamed: JP1.2, U$1.D4
unnamed: JP1.3, U$1.D3
unnamed: C5.1, IC3.2 (BYP)
unnamed: JP1.4, U$1.D2
unnamed: JP1.5, U$1.D1
unnamed: JP1.7, U$1.A6
unnamed: JP1.8, U$1.A5
unnamed: JP1.9, U$1.A4
unnamed: JP1.10, U$1.A3
unnamed: JP1.11, U$1.A2
unnamed: JP1.12, U$1.A1
unnamed: JP1.14, U$1.AREF
unnamed: JP2.14, U$1.D6
unnamed: JP2.11, U$1.SCK
unnamed: JP2.10, U$1.MISO
unnamed: JP2.7, U$1.RX
unnamed: JP2.6, U$1.TX
unnamed: JP2.5, U$1.RESET
unnamed: JP2.2, U$1.VIN
unnamed: IC1.5 (SDO), R3.2
unnamed: IC1.2 (CSB), R2.1
unnamed: IC2.5 (INT), R6.2, SJ3.1
unnamed: L1.4-DIN (DIN), R1.2
unnamed: JP3.2, L1.2-DOUT (DOUT)
NEOPIXELS: JP1.13, R1.1, U$1.A0
NEOPIXEL_SUPPLY: C4.A (+), D1.C, JP3.3, L1.1-VDD (VDD)
SCL: IC1.4 (SCK), IC2.2 (SCL), IC3.4 (SCL), JP2.8, U$1.SCL
SDA: IC1.3 (SDI), IC2.6 (SDA), IC3.6 (SDA), JP2.9, U$1.SDA

Notes on the sheet:
TCS3472
Open Drain, Active Low
Stephen Harrison
V1.0
Addr: 0x29

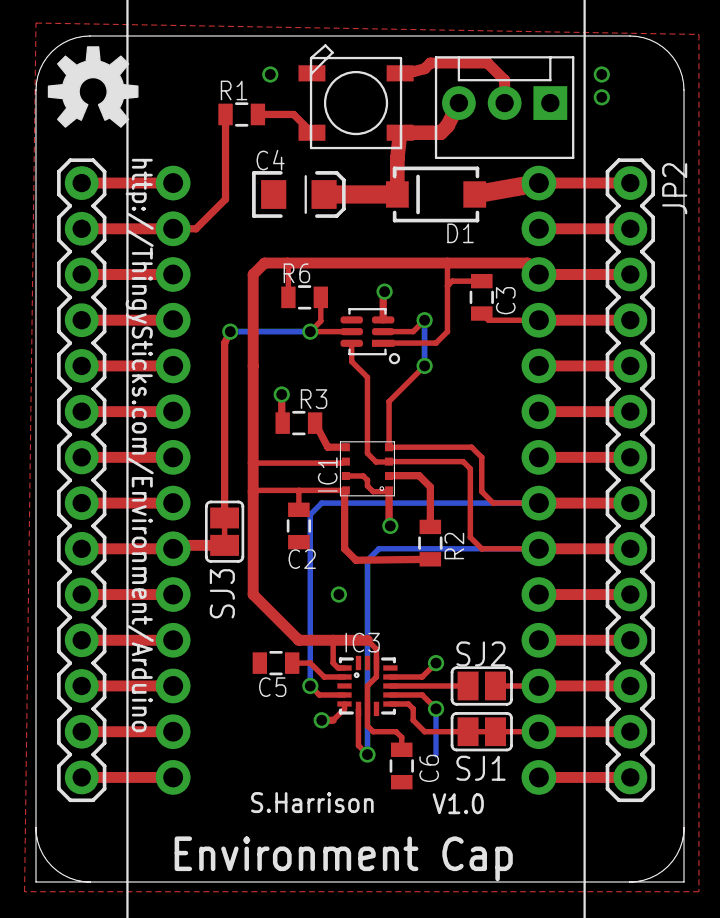
[picture p102: board ArduinoAirQuailtyTop.brd from above]

Board: 2 copper layers, 36.0 x 47.0 mm, 23 parts (0 on the bottom side), 37 nets.
