ThingySticks/EnvironmentMonitor/Electron/V4/PCB/EnvironmentMonitorV4.brd

## EAGLE design Electron/V4/PCB/EnvironmentMonitorV4.brd (2018-01-11)

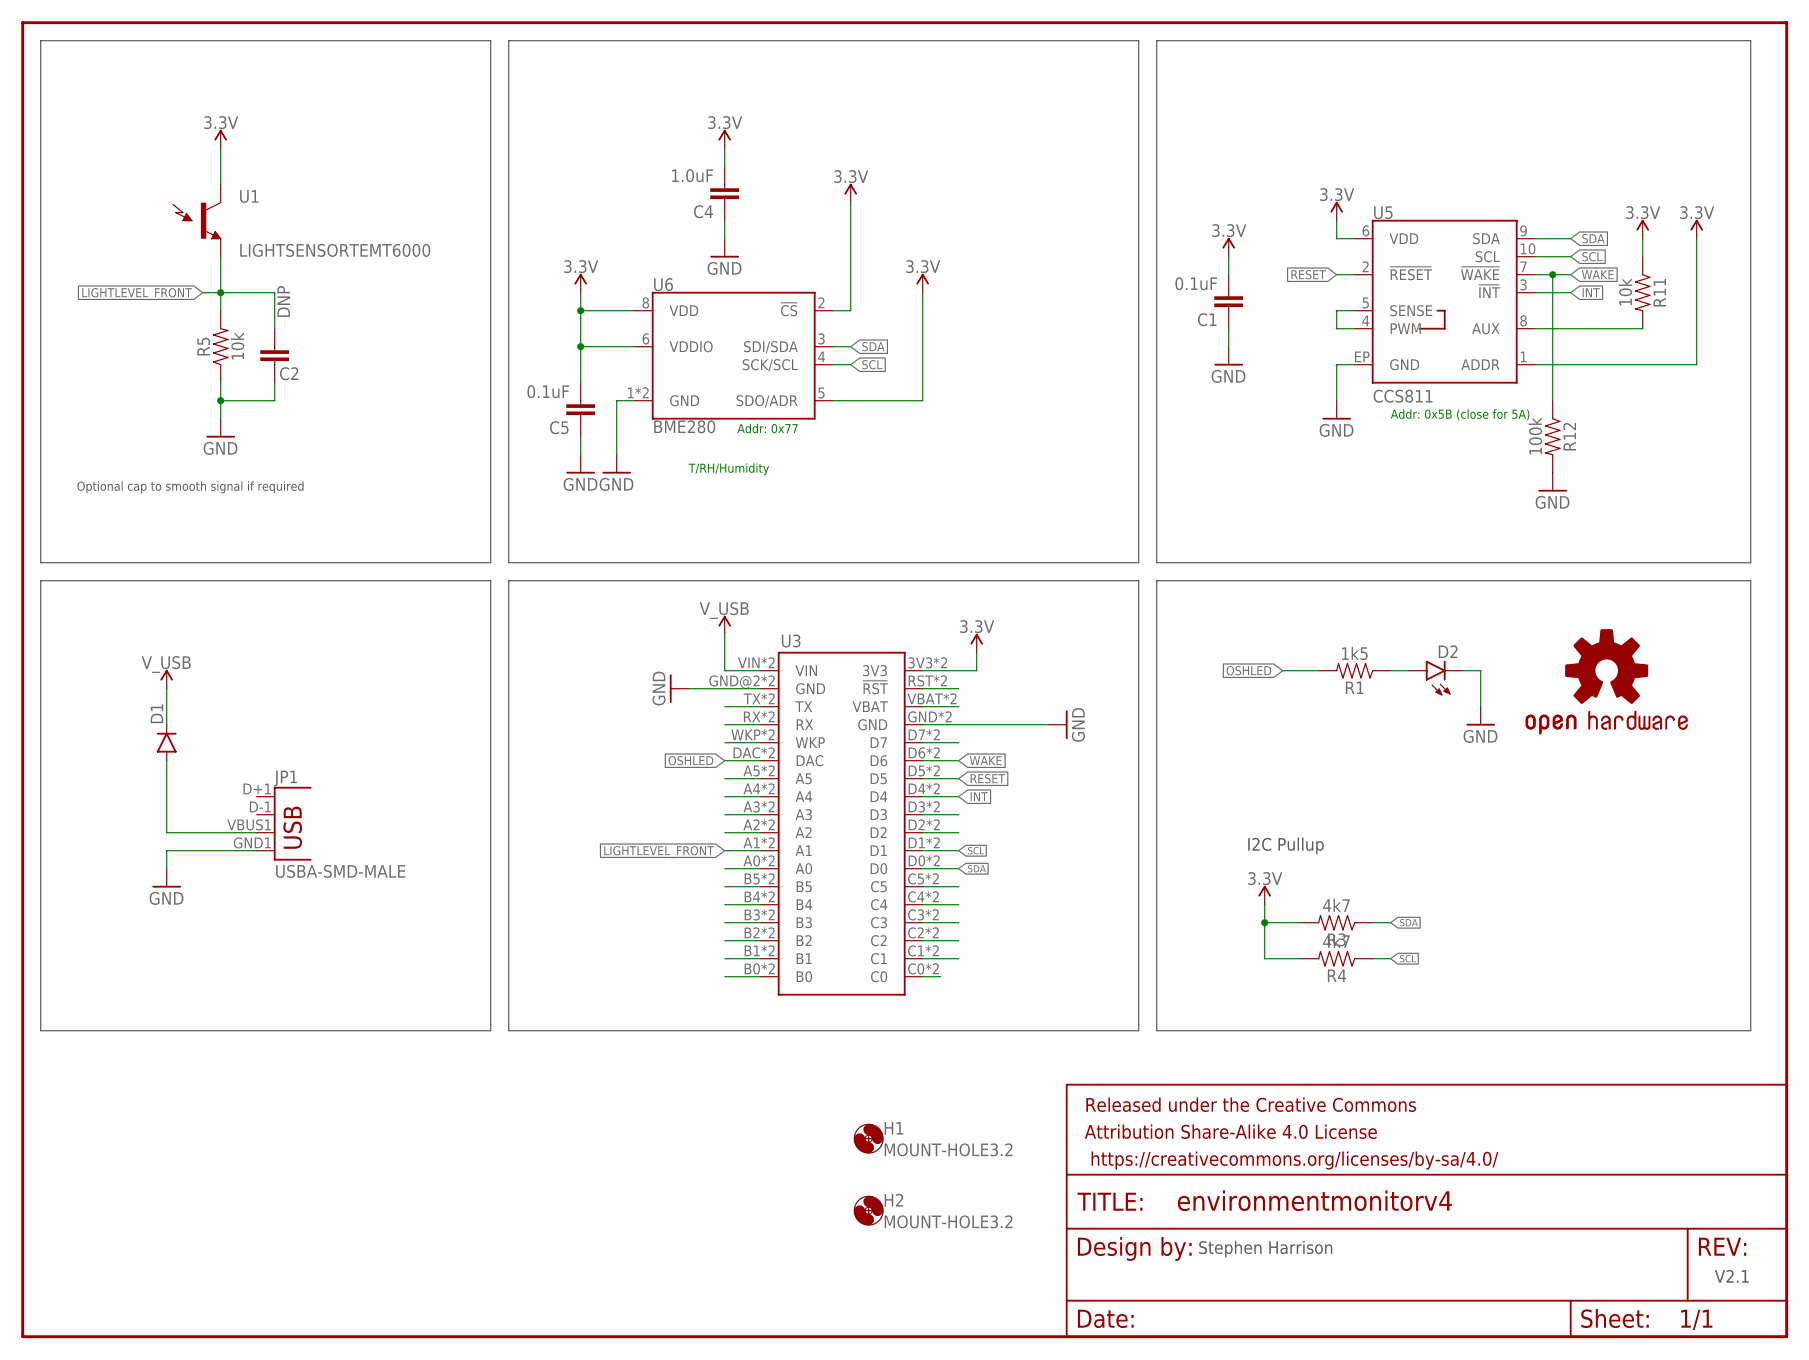
[picture p103: schematic EnvironmentMonitorV4.sch]

Parts:
C1, C5: 0.1uF; 0805-CAP
C2: DNP; 0805-CAP
C4: 1.0uF; 0805-CAP
D1: DIODESMA; SMA-DIODE
D2: LED1206-BOTTOM; LED-1206-BOTTOM
FRAME1: FRAME-LETTER; CREATIVE_COMMONS
H1, H2: MOUNT-HOLE3.2; 3,2
JP1: USBA-SMD-MALE; USB-A-SMT-MALE
LOGO1: OSHW-LOGOM; OSHW-LOGO-M
R1: 1k5; 0805
R3, R4: 4k7; 0805
R5, R11: 10k; 0805
R12: 100k; 0805
U1: LIGHTSENSORTEMT6000; TEMT6000-SEN
U3: ELECTRONDUALNAMED; ELECTRON_SIMPLE_SILK_NAMES_DUAL
U5: CCS811; LGA10
U6: BME280; LGA-8-2.5X2.5

Connections:
3.3V: C1.2, C4.2, C5.2, R3.2, R4.2, R11.1, U1.COLLECTOR (C1), U3.3V3, U3.3V3_1 (3V3), U5.1 (ADDR), U5.6 (VDD), U6.2 (!CS), U6.5 (SDO/ADR), U6.6 (VDDIO), U6.8 (VDD)
AUX: R11.2, U5.8 (AUX)
GND: C1.1, C2.1, C4.1, C5.1, D2.C, JP1.GND1 (GND), R5.1, R12.2, U3.GND, U3.GND@2 (GND), U3.GND_1 (GND), U3.GND_1B (GND), U5.EP (GND), U6.1 (GND), U6.7 (GND)
INT: U3.D4, U3.D4_1 (D4), U5.3 (!INT!)
LIGHTLEVEL_FRONT: C2.2, R5.2, U1.EMITTER (E1), U3.A1, U3.A1_1 (A1)
LIGHTLEVEL_REAR: U3.A0, U3.A0_1 (A0)
unnamed: U3.RST (!RST), U3.RST_1 (!RST)
unnamed: U3.VBAT, U3.VBATT_1 (VBAT)
unnamed: U3.WKP, U3.WKP_1 (WKP)
unnamed: D1.A, JP1.VBUS1 (VBUS)
unnamed: D2.A, R1.1
unnamed: U3.D7, U3.D7_1 (D7)
unnamed: U3.D2, U3.D2_1 (D2)
unnamed: U3.D3, U3.D3_1 (D3)
unnamed: U3.C5, U3.C5_1 (C5)
unnamed: U3.C4, U3.C4_1 (C4)
unnamed: U3.C3, U3.C3_1 (C3)
unnamed: U3.C2, U3.C2_1 (C2)
unnamed: U3.C1, U3.C1_1 (C1)
unnamed: U3.C0, U3.C0_1 (C0)
unnamed: U3.B0, U3.B0_1 (B0)
unnamed: U3.B1, U3.B1_1 (B1)
unnamed: U3.B2, U3.B2_1 (B2)
unnamed: U3.B3, U3.B3_1 (B3)
unnamed: U3.B4, U3.B4_1 (B4)
unnamed: U3.B5, U3.B5_1 (B5)
unnamed: U3.A2, U3.A2_1 (A2)
unnamed: U3.A3, U3.A3_1 (A3)
unnamed: U3.A4, U3.A4_1 (A4)
unnamed: U3.A5, U3.A5_1 (A5)
unnamed: U3.RX, U3.RX_1 (RX)
unnamed: U3.TX, U3.TX_1 (TX)
NTC_SENSE: U5.4 (PWM), U5.5 (SENSE)
OSHLED: R1.2, U3.DAC, U3.DAC_1 (DAC)
RESET: U3.D5, U3.D5_1 (D5), U5.2 (!RESET!)
SCL: R4.1, U3.D1, U3.D1_1 (D1), U5.10 (SCL), U6.4 (SCK/SCL)
SDA: R3.1, U3.D0, U3.D0_1 (D0), U5.9 (SDA), U6.3 (SDI/SDA)
V_USB: D1.C, U3.VIN, U3.VIN_1B (VIN)
WAKE: R12.1, U3.D6, U3.D6_1 (D6), U5.7 (!WAKE!)

Notes on the sheet:
I2C Pullup
V2.1
Stephen Harrison
T/RH/Humidity
Addr: 0x77
Addr: 0x5B (close for 5A)
Optional cap to smooth signal if required

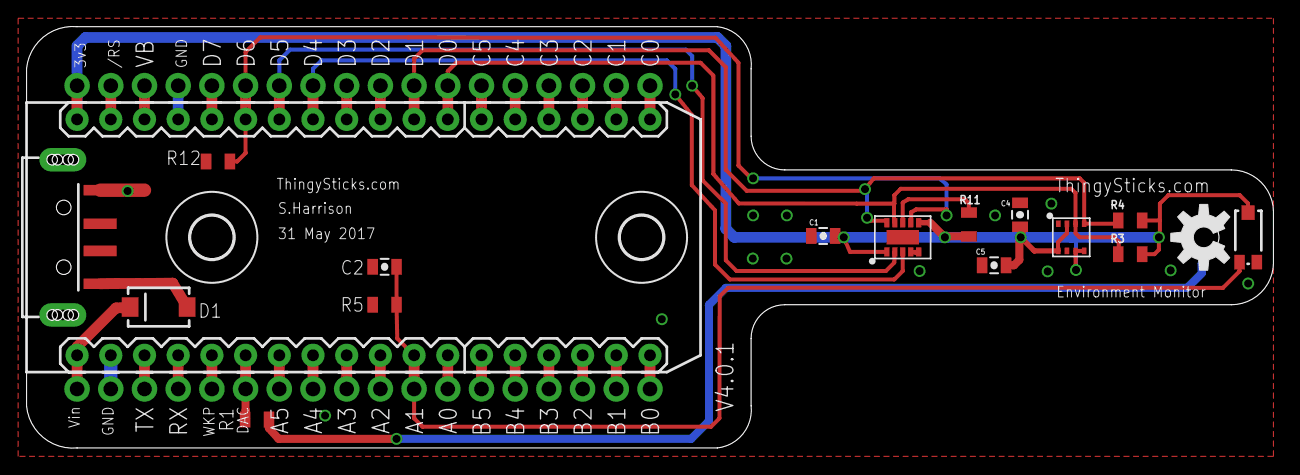
[picture p104: board EnvironmentMonitorV4.brd from above]

Board: 2 copper layers, 94.0 x 31.8 mm, 21 parts (1 on the bottom side), 39 nets.
