ThingySticks/EnvironmentMonitor/Photon/V4.1/PCB/EnvironmentMonitorV4.1.brd

## EAGLE design Photon/V4.1/PCB/EnvironmentMonitorV4.1.brd (2017-05-22)

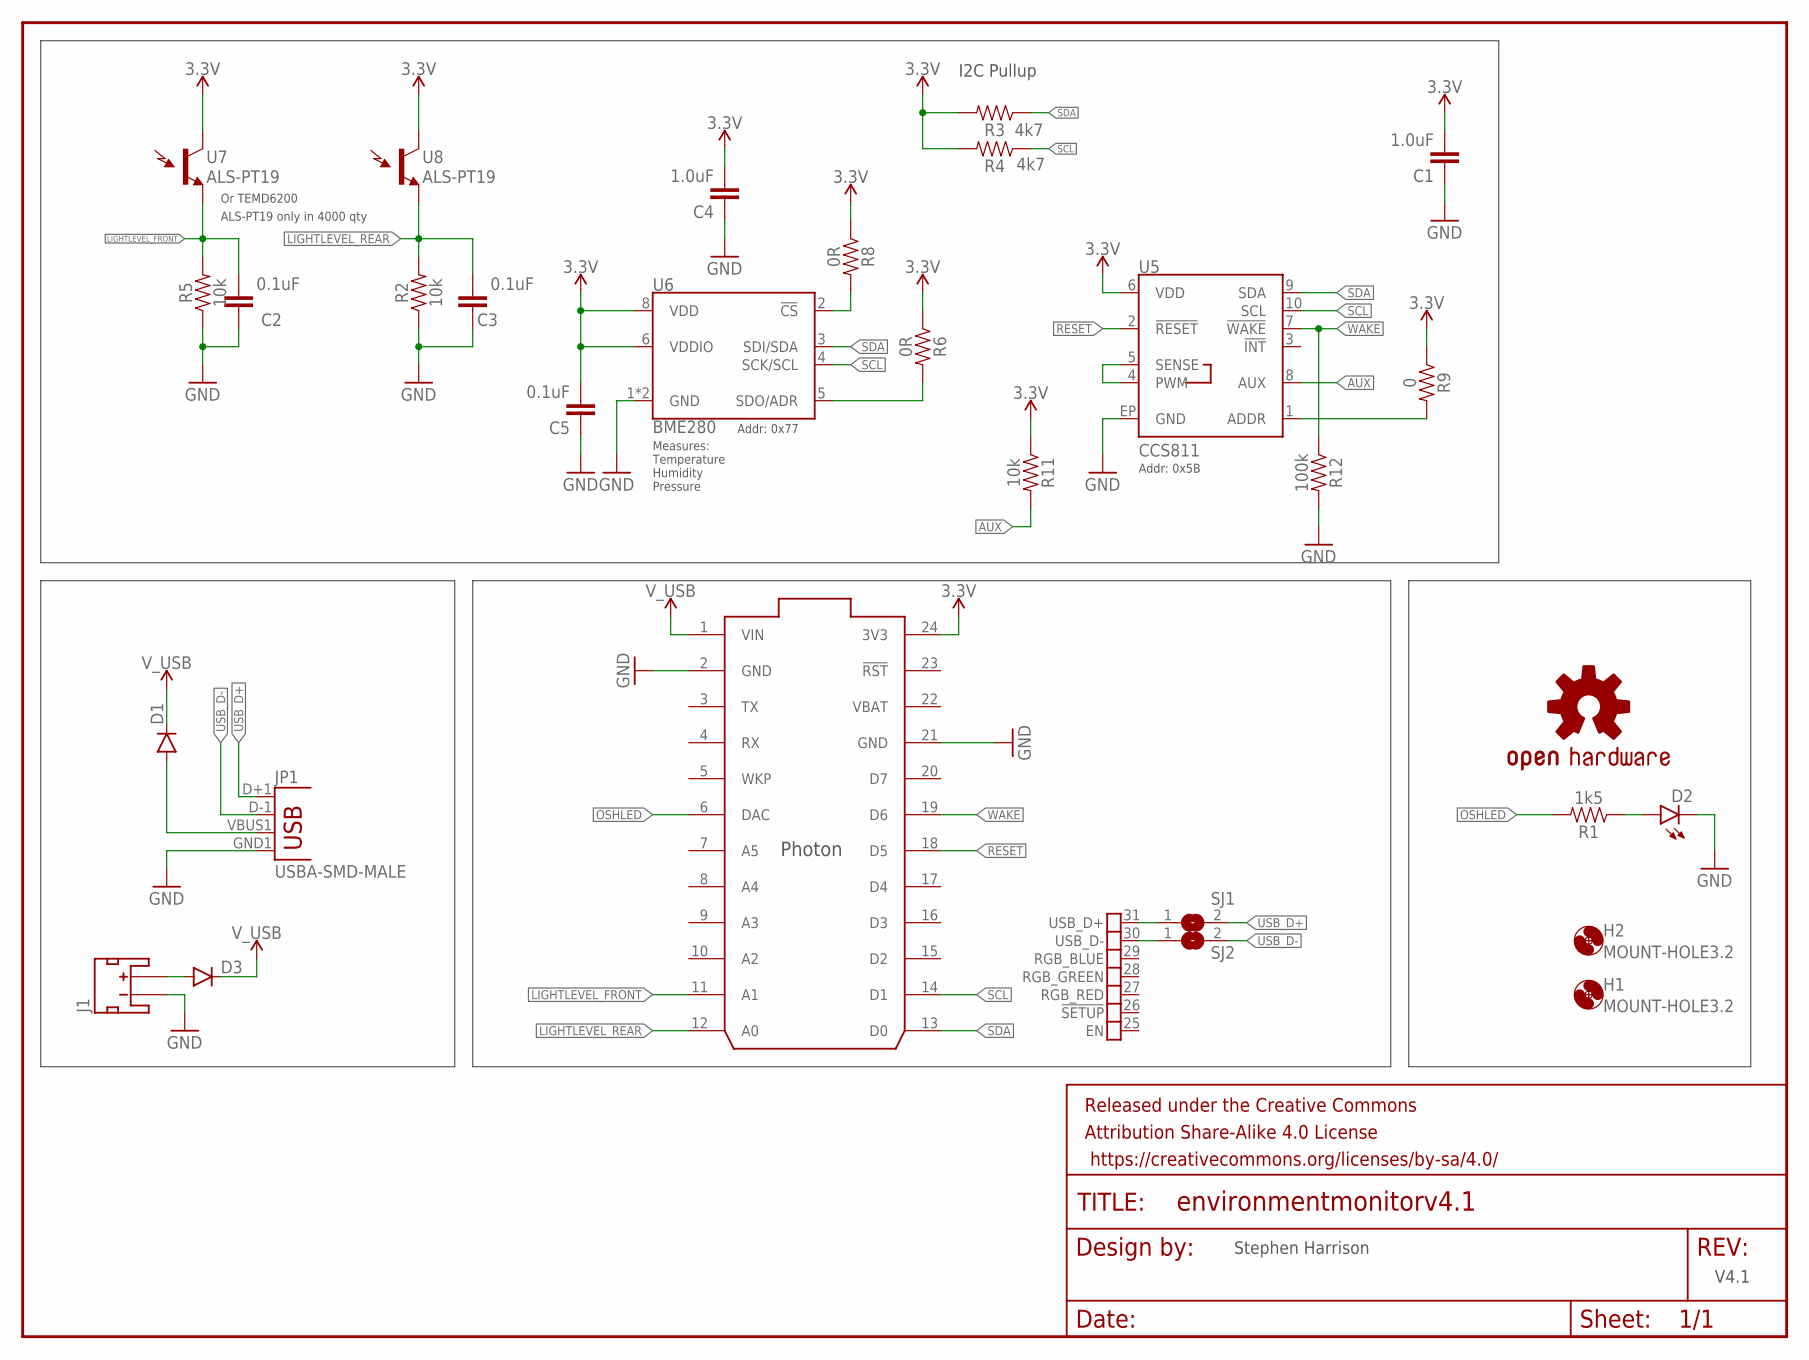
[picture p105: schematic EnvironmentMonitorV4.1.sch]

Parts:
C1, C4: 1.0uF; 0805-CAP
C2, C3, C5: 0.1uF; 0805-CAP
D1, D3: DIODESMA; SMA-DIODE
D2: LED1206-BOTTOM; LED-1206-BOTTOM
FRAME1: FRAME-LETTER; CREATIVE_COMMONS
H1, H2: MOUNT-HOLE3.2; 3,2
J1: JST_2MM_MALE; JST-2-SMD
JP1: USBA-SMD-MALE; USB-A-SMT-MALE
LOGO1: OSHW-LOGOM; OSHW-LOGO-M
R1: 1k5; 0805
R2, R5, R11: 10k; 0805
R3, R4: 4k7; 0805
R6, R8: 0R; 0805
R9: 0; 0805
R12: 100k; 0805
SJ1, SJ2: SJ
U5: CCS811; LGA10
U6: BME280; LGA-8-2.5X2.5
U7, U8: ALS-PT19
U$1: PHOTON_SMD

Connections:
3.3V: C1.2, C4.2, C5.2, R3.2, R4.2, R6.1, R8.1, R9.1, R11.1, U5.6 (VDD), U6.6 (VDDIO), U6.8 (VDD), U7.C (C1), U8.C (C1), U$1.24 (3V3)
AUX: R11.2, U5.8 (AUX)
BME280_CS: R8.2, U6.2 (!CS)
GND: C1.1, C2.1, C3.1, C4.1, C5.1, D2.C, J1.1 (-), JP1.GND1 (GND), R2.1, R5.1, R12.2, U5.EP (GND), U6.1 (GND), U6.7 (GND), U$1.2 (GND), U$1.21 (GND)
LIGHTLEVEL_FRONT: C2.2, R5.2, U7.E (E1), U$1.11 (A1)
LIGHTLEVEL_REAR: C3.2, R2.2, U8.E (E1), U$1.12 (A0)
unnamed: SJ1.1, U$1.31 (USB_D+)
unnamed: SJ2.1, U$1.30 (USB_D-)
unnamed: R6.2, U6.5 (SDO/ADR)
unnamed: D3.A, J1.2 (+)
unnamed: D1.A, JP1.VBUS1 (VBUS)
unnamed: D2.A, R1.1
unnamed: R9.2, U5.1 (ADDR)
NTC_SENSE: U5.4 (PWM), U5.5 (SENSE)
OSHLED: R1.2, U$1.6 (DAC)
RESET: U5.2 (!RESET!), U$1.18 (D5)
SCL: R4.1, U5.10 (SCL), U6.4 (SCK/SCL), U$1.14 (D1)
SDA: R3.1, U5.9 (SDA), U6.3 (SDI/SDA), U$1.13 (D0)
USB_D+: JP1.D+1 (D+), SJ1.2
USB_D-: JP1.D-1 (D-), SJ2.2
VBAT: U$1.22 (VBAT)
V_USB: D1.C, D3.C, U$1.1 (VIN)
WAKE: R12.1, U5.7 (!WAKE!), U$1.19 (D6)

Notes on the sheet:
I2C Pullup
V4.1
Stephen Harrison
Or TEMD6200
ALS-PT19 only in 4000 qty
Measures: Temperature Humidity Pressure
Addr: 0x77
Addr: 0x5B

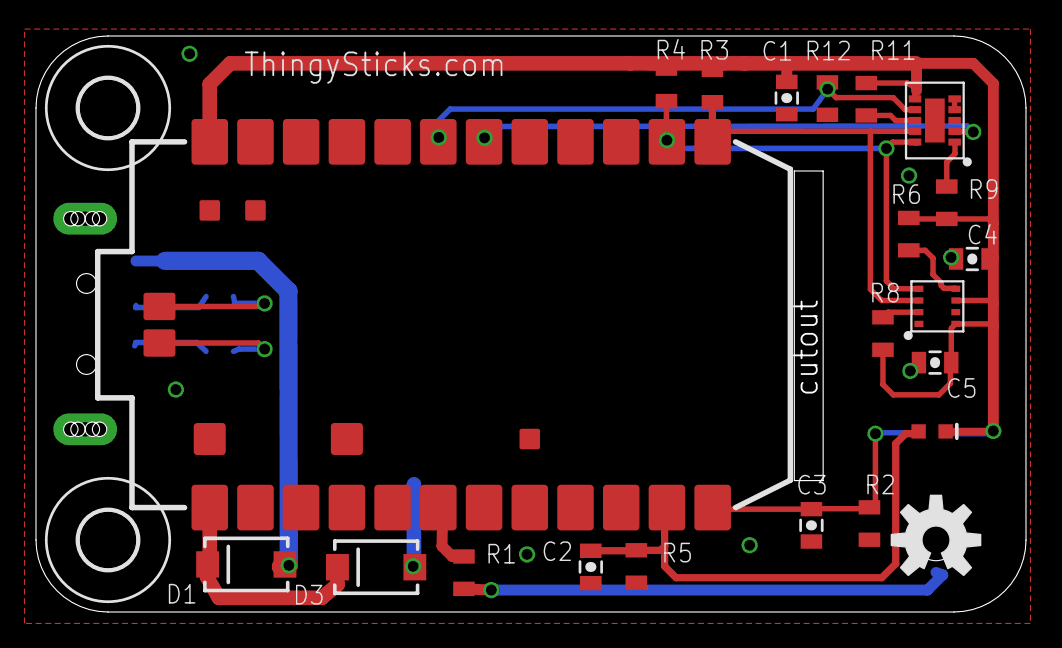
[picture p106: board EnvironmentMonitorV4.1.brd from above]

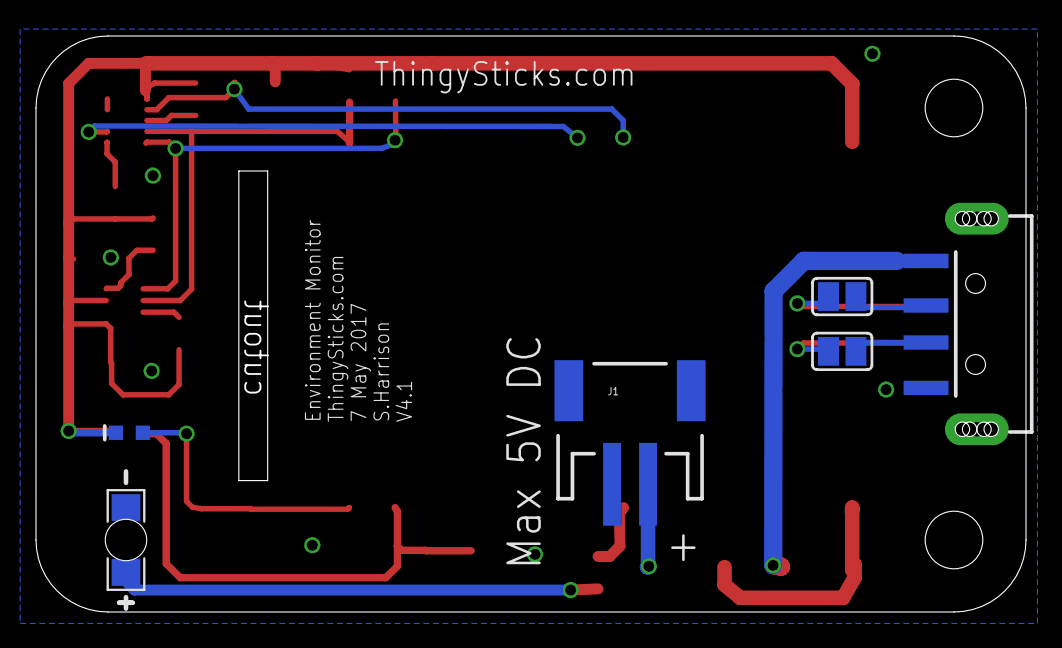
[picture p107: board EnvironmentMonitorV4.1.brd from below]

Board: 2 copper layers, 55.0 x 32.0 mm, 31 parts (6 on the bottom side), 22 nets.
